sungmin9910/ColdChain-DigitalTwin-Platform/scratch/sensor_flip_guide.png

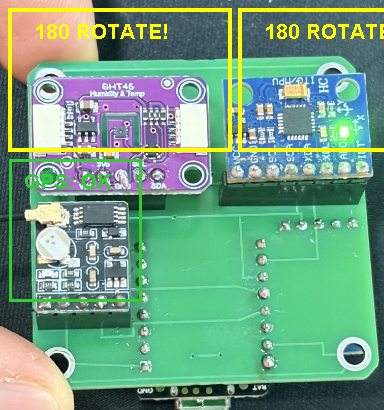
scratch/sensor_flip_guide.png
