sungmin9910/ColdChain-DigitalTwin-Platform/Final_Experiment/3_Consumer_Dashboard/consumer_guide.png

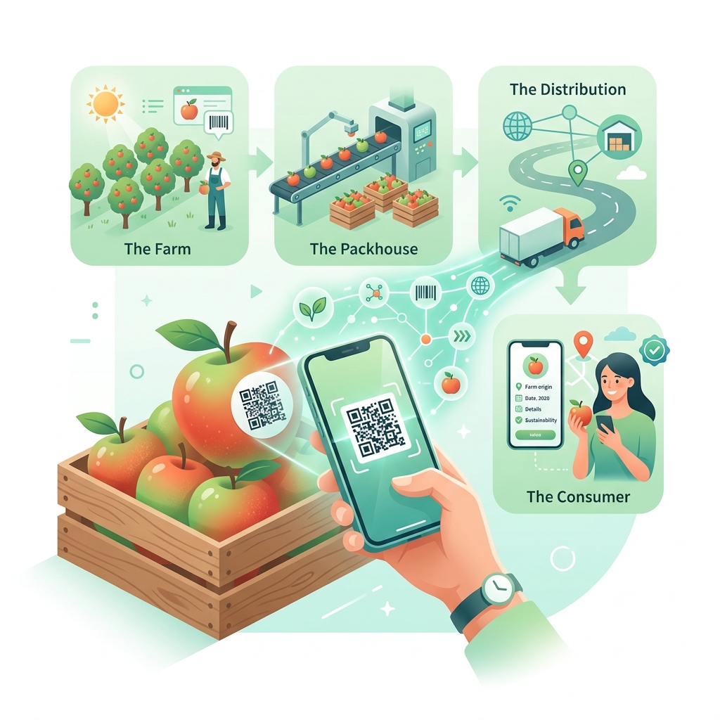
Final_Experiment/3_Consumer_Dashboard/consumer_guide.png
