sungmin9910/ColdChain-DigitalTwin-Platform/3D modeling/adafruit-sht45-breakout-board-1.snapshot.2/5665-00.jpg

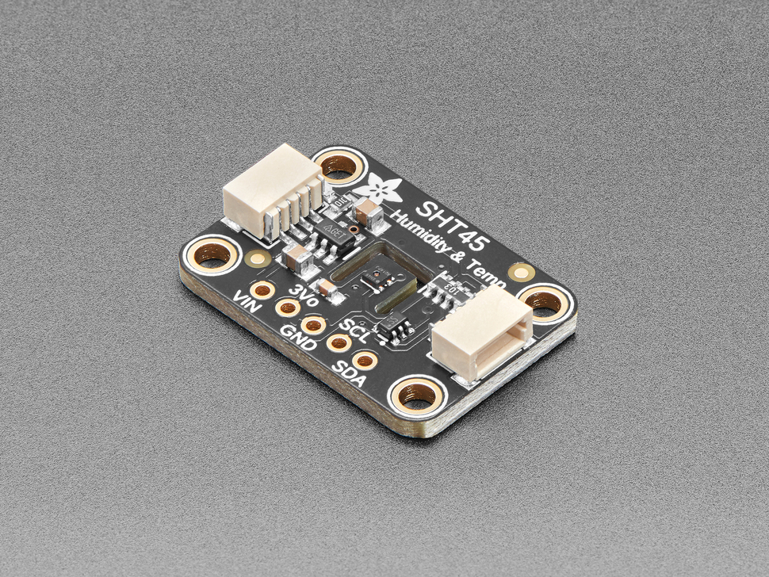
3D modeling/adafruit-sht45-breakout-board-1.snapshot.2/5665-00.jpg
