sungmin9910/ColdChain-DigitalTwin-Platform/3D modeling/CarrierBoard_BeetleC6_EdgeUSB_50x50_NoText/Fig2_CarrierBoard_3D_Isometric_Engineering_Drawing.png

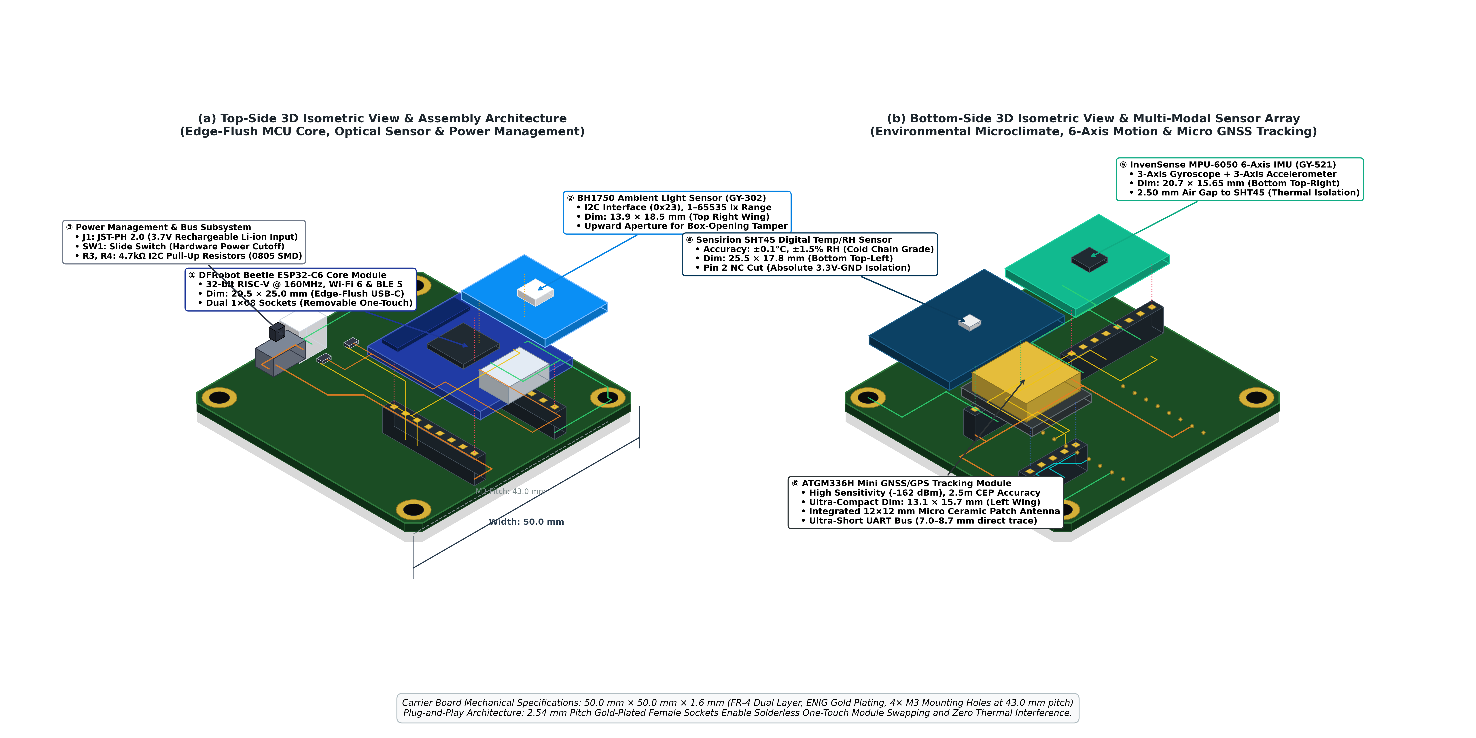
3D modeling/CarrierBoard_BeetleC6_EdgeUSB_50x50_NoText/Fig2_CarrierBoard_3D_Isometric_Engineering_Drawing.png
