sungmin9910/ColdChain-DigitalTwin-Platform/3D modeling/CarrierBoard_BeetleC6_EdgeUSB_50x50_NoText/Fig7_FDT_CrossSection_Engineering_Schematic.png

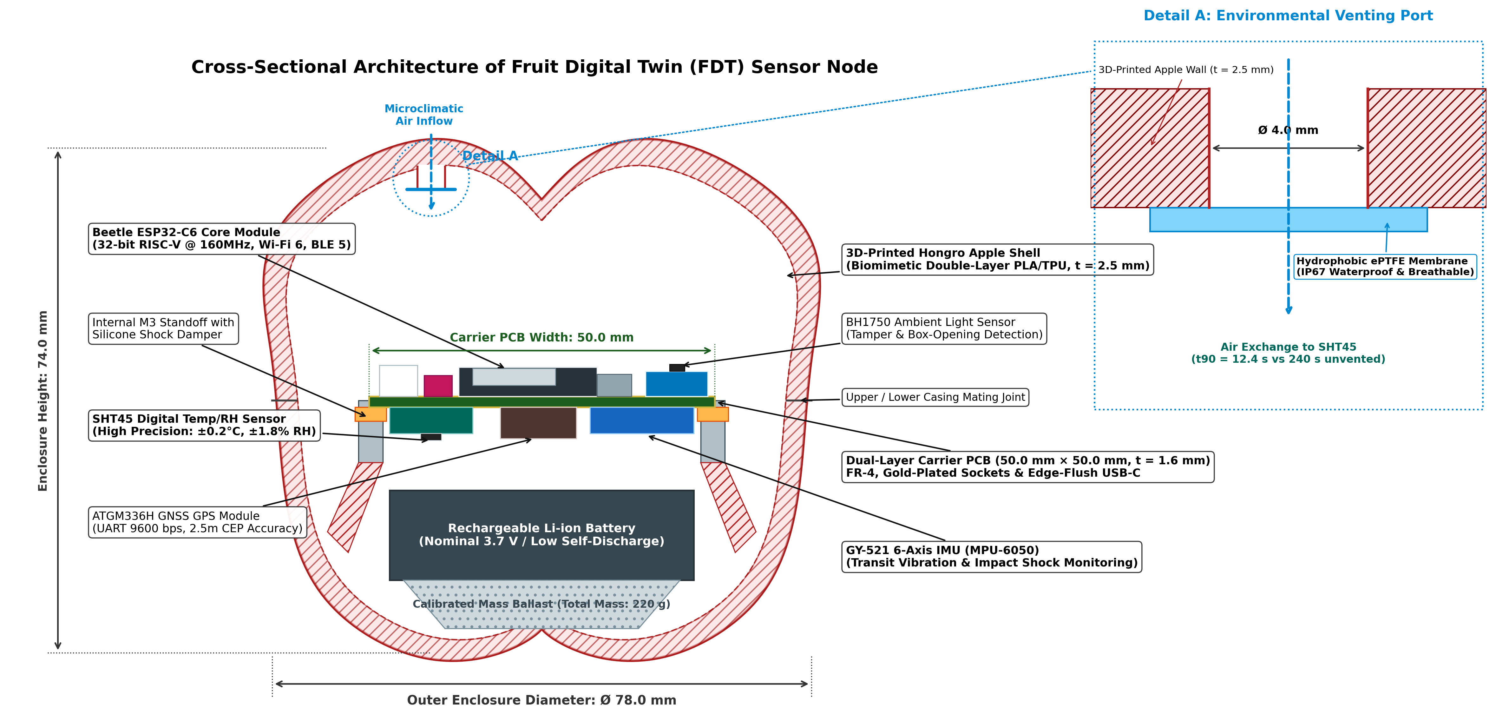
3D modeling/CarrierBoard_BeetleC6_EdgeUSB_50x50_NoText/Fig7_FDT_CrossSection_Engineering_Schematic.png
