sungmin9910/ColdChain-DigitalTwin-Platform/3D modeling/CarrierBoard_BeetleC6_EdgeUSB_50x50_NoText/Render_Bottom_NoText.png

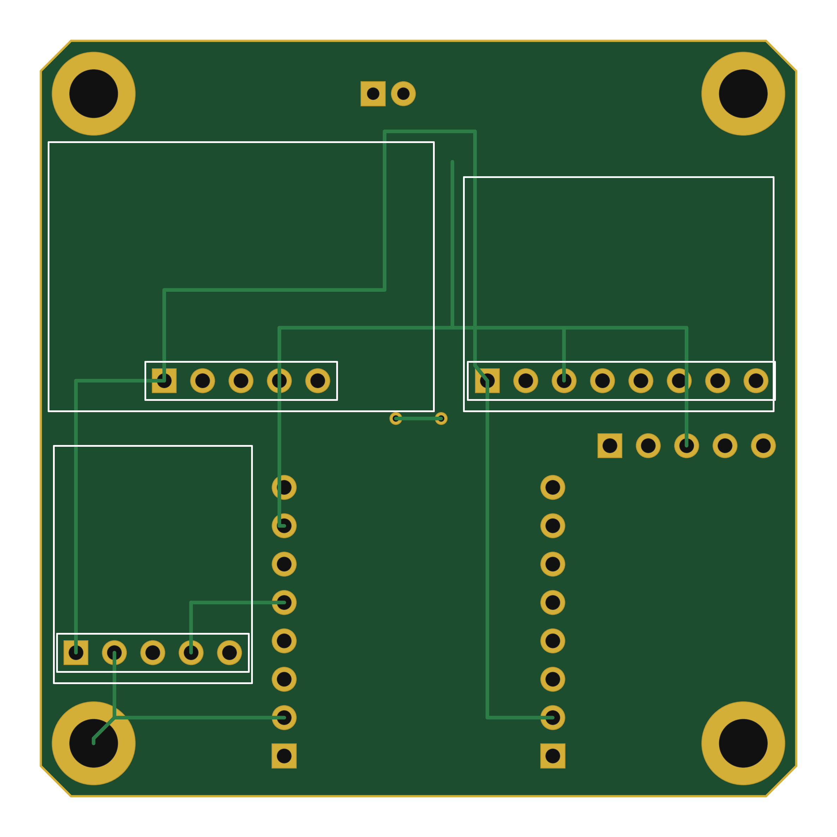
3D modeling/CarrierBoard_BeetleC6_EdgeUSB_50x50_NoText/Render_Bottom_NoText.png
