sungmin9910/ColdChain-DigitalTwin-Platform/3D modeling/CarrierBoard_BeetleC6_EdgeUSB_50x50_NoText/render_top_pcb.png

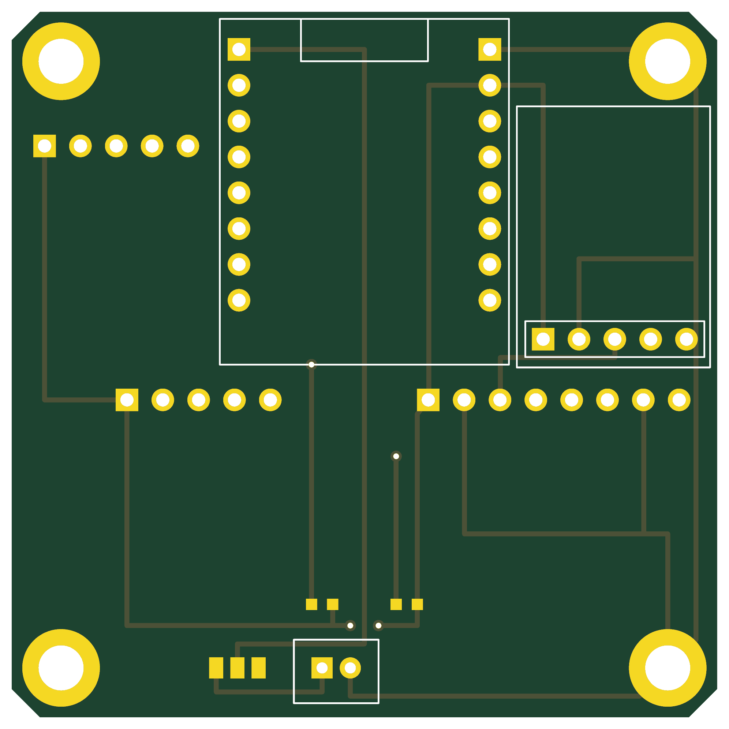
3D modeling/CarrierBoard_BeetleC6_EdgeUSB_50x50_NoText/render_top_pcb.png
