sungmin9910/ColdChain-DigitalTwin-Platform/3D modeling/GyroSensor_GY-521/Renderings/GY-521 MPU-6050_Webv004.jpg

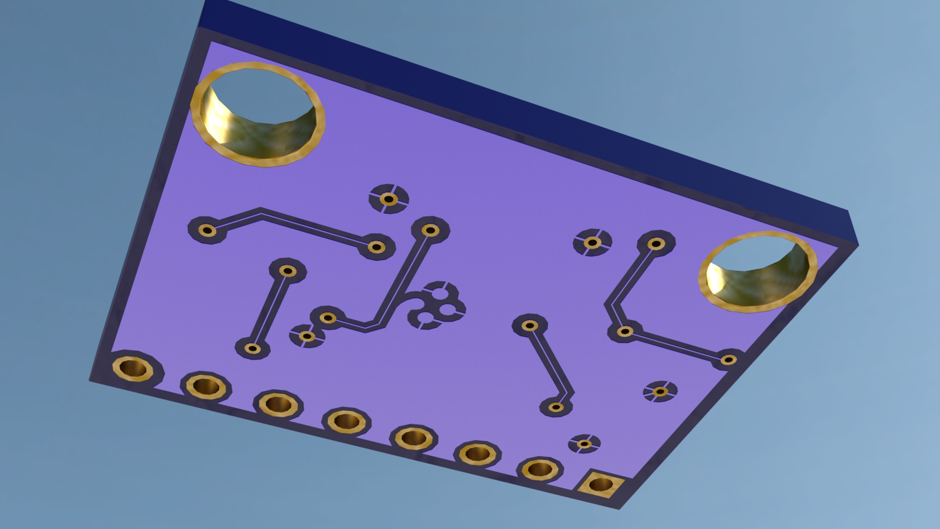
3D modeling/GyroSensor_GY-521/Renderings/GY-521 MPU-6050_Webv004.jpg
