sungmin9910/ColdChain-DigitalTwin-Platform/3D modeling/hw-373-1.snapshot.2/pic.jpg

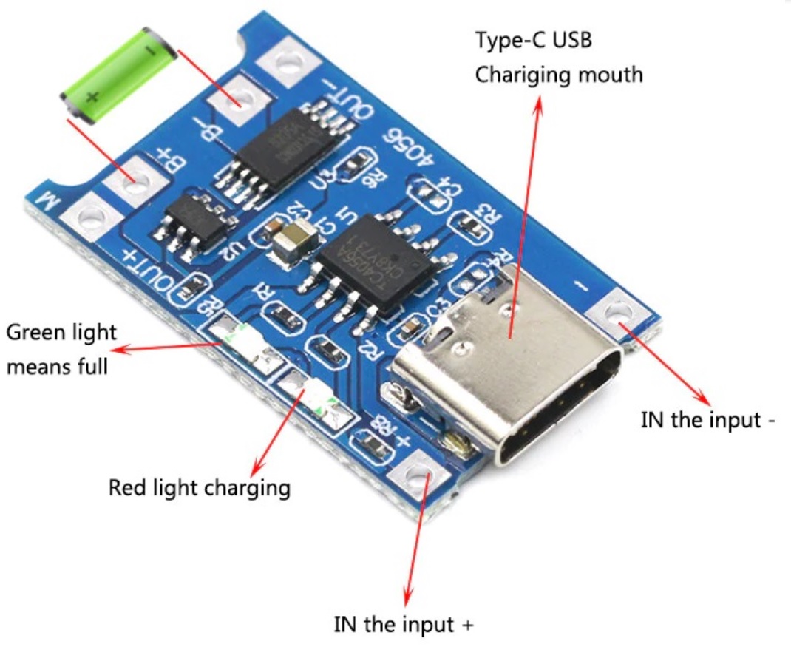
3D modeling/hw-373-1.snapshot.2/pic.jpg
