sungmin9910/ColdChain-DigitalTwin-Platform/3D modeling/mini dc dc boost module/mini dc dc boost module.png

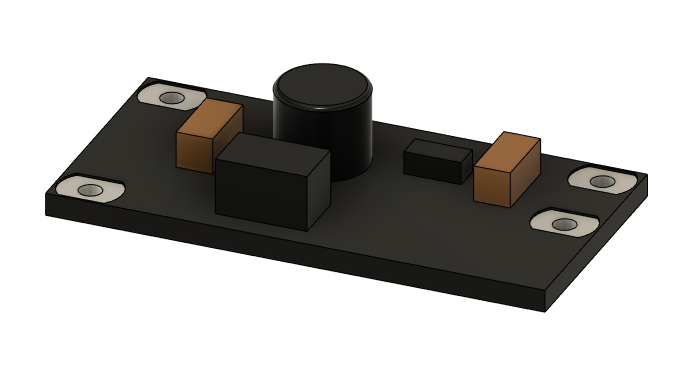
3D modeling/mini dc dc boost module/mini dc dc boost module.png
