sungmin9910/ColdChain-DigitalTwin-Platform/3D modeling/Neo-6m-0-001/Neo-6m-0-001.png

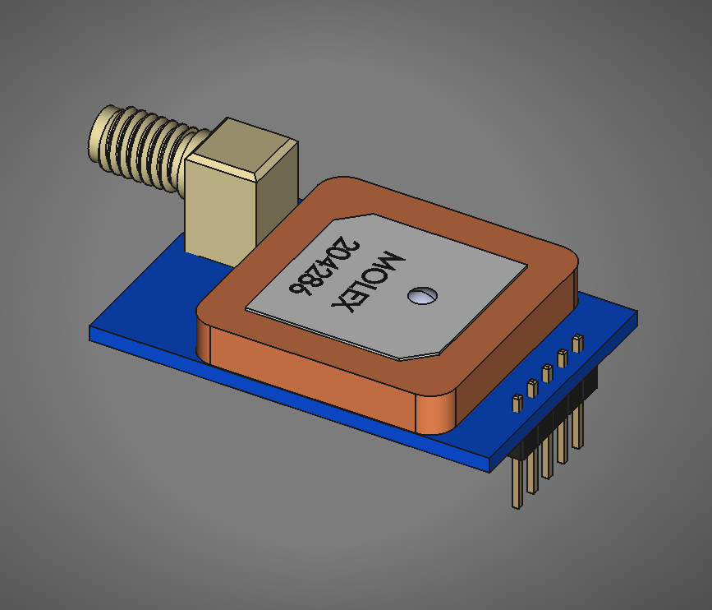
3D modeling/Neo-6m-0-001/Neo-6m-0-001.png
