sungmin9910/ColdChain-DigitalTwin-Platform/3D modeling/회로도.kicad_sch/pcb_layout.png

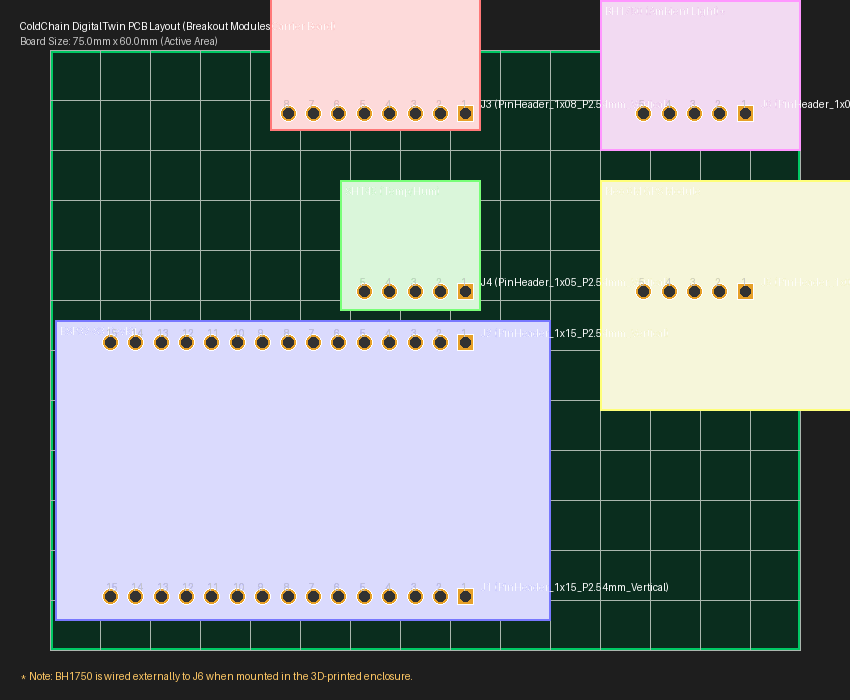
3D modeling/회로도.kicad_sch/pcb_layout.png
