sungmin9910/ColdChain-DigitalTwin-Platform/3D modeling/회로도_stack/pcb_stack_layout.png

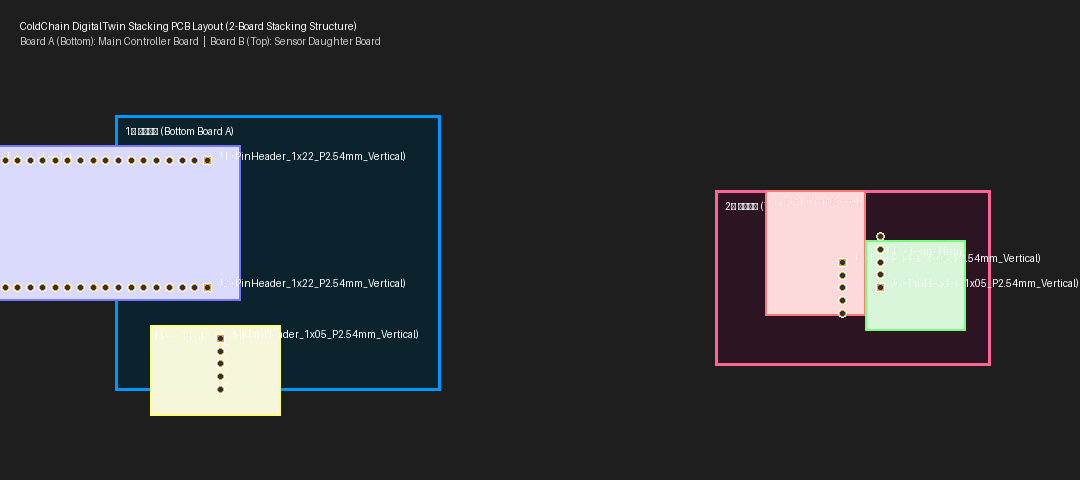
3D modeling/회로도_stack/pcb_stack_layout.png
