sungmin9910/ColdChain-DigitalTwin-Platform/KSHS/digital_twin_v2.png

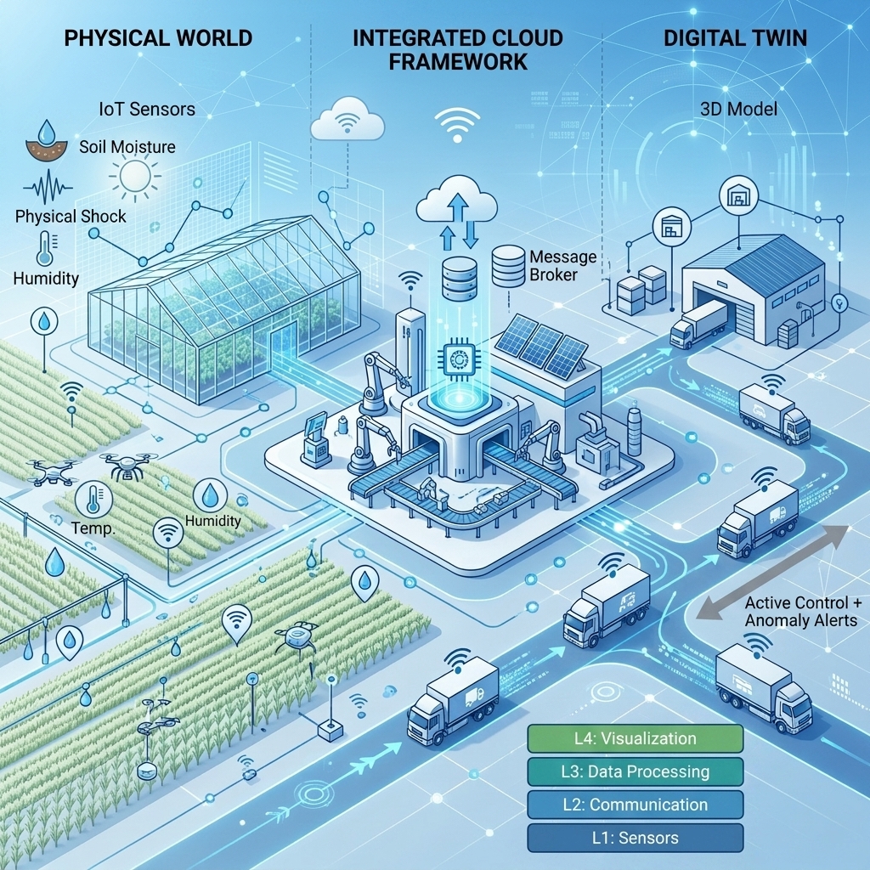
KSHS/digital_twin_v2.png
