sungmin9910/ColdChain-DigitalTwin-Platform/KSHS/extracted_images/slide_1_img_24_449x393.jpg

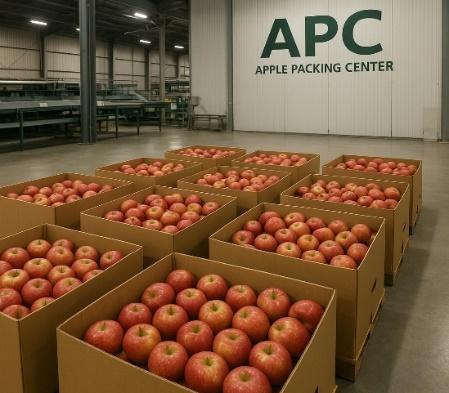
KSHS/extracted_images/slide_1_img_24_449x393.jpg
