sungmin9910/ColdChain-DigitalTwin-Platform/KSHS/extracted_images/slide_1_img_32_4032x2268.png

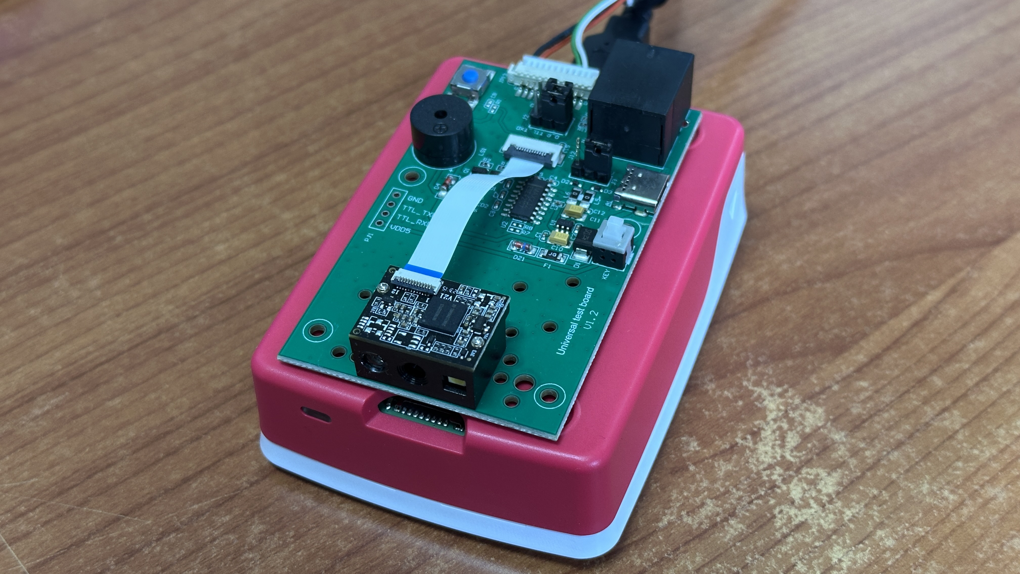
KSHS/extracted_images/slide_1_img_32_4032x2268.png
