sungmin9910/ColdChain-DigitalTwin-Platform/KSHS/extracted_images/slide_1_img_35_1330x1266.png

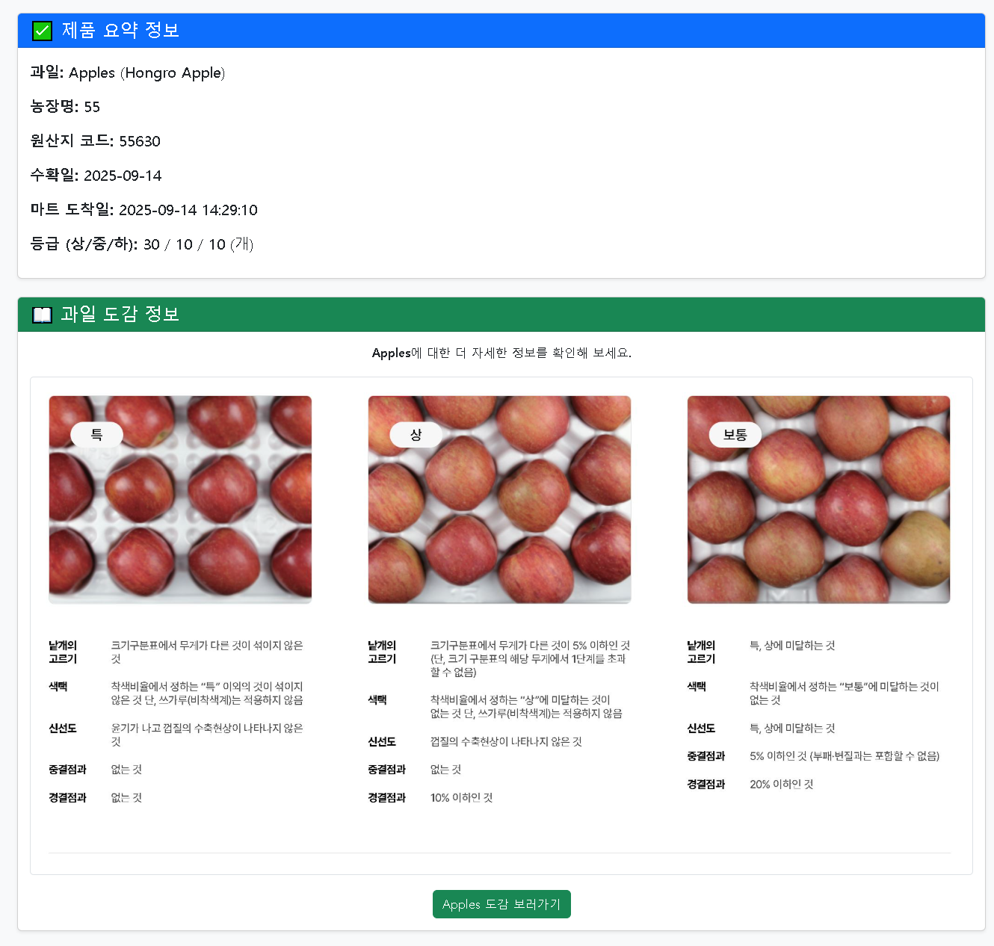
KSHS/extracted_images/slide_1_img_35_1330x1266.png
