sungmin9910/ColdChain-DigitalTwin-Platform/KSHS/extracted_images/slide_1_img_36_530x530.png

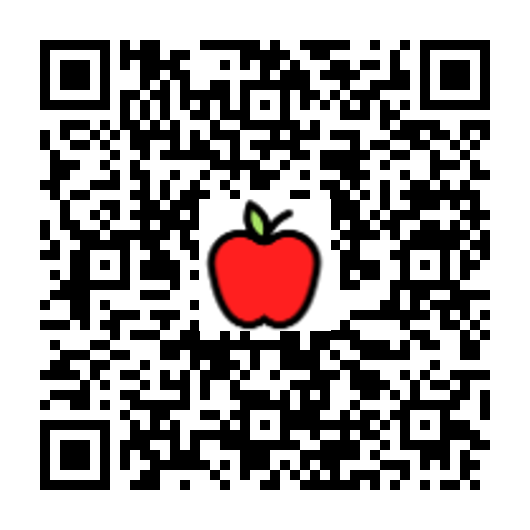
KSHS/extracted_images/slide_1_img_36_530x530.png
