sungmin9910/ColdChain-DigitalTwin-Platform/KSHS/extracted_images/slide_1_img_37_433x433.png

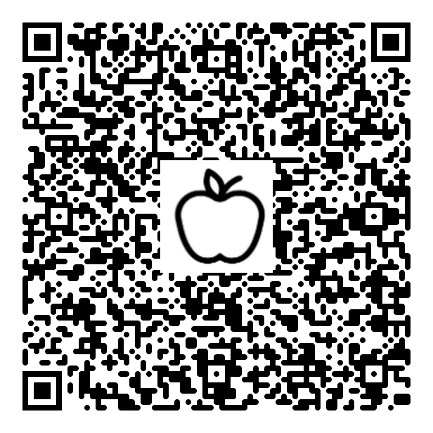
KSHS/extracted_images/slide_1_img_37_433x433.png
