sungmin9910/ColdChain-DigitalTwin-Platform/KSHS/extracted_images/slide_1_img_38_3024x3024.png

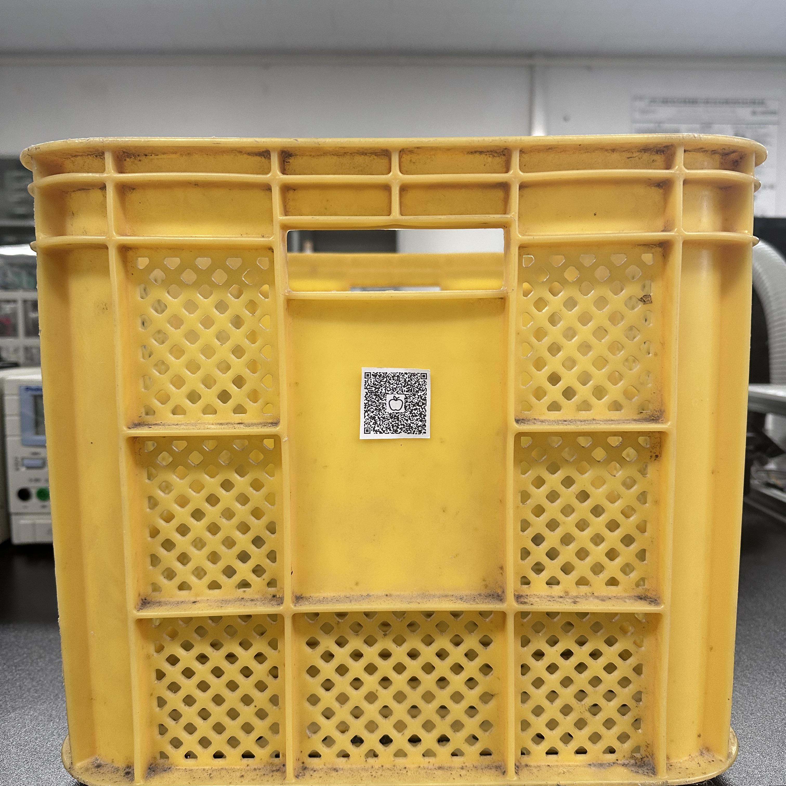
KSHS/extracted_images/slide_1_img_38_3024x3024.png
