sungmin9910/ColdChain-DigitalTwin-Platform/KSHS/extracted_images/slide_1_img_41_285x221.jpg

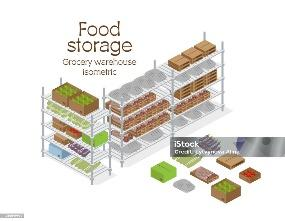
KSHS/extracted_images/slide_1_img_41_285x221.jpg
