sungmin9910/ColdChain-DigitalTwin-Platform/KSHS/extracted_images/slide_1_img_46_1651x1844.png

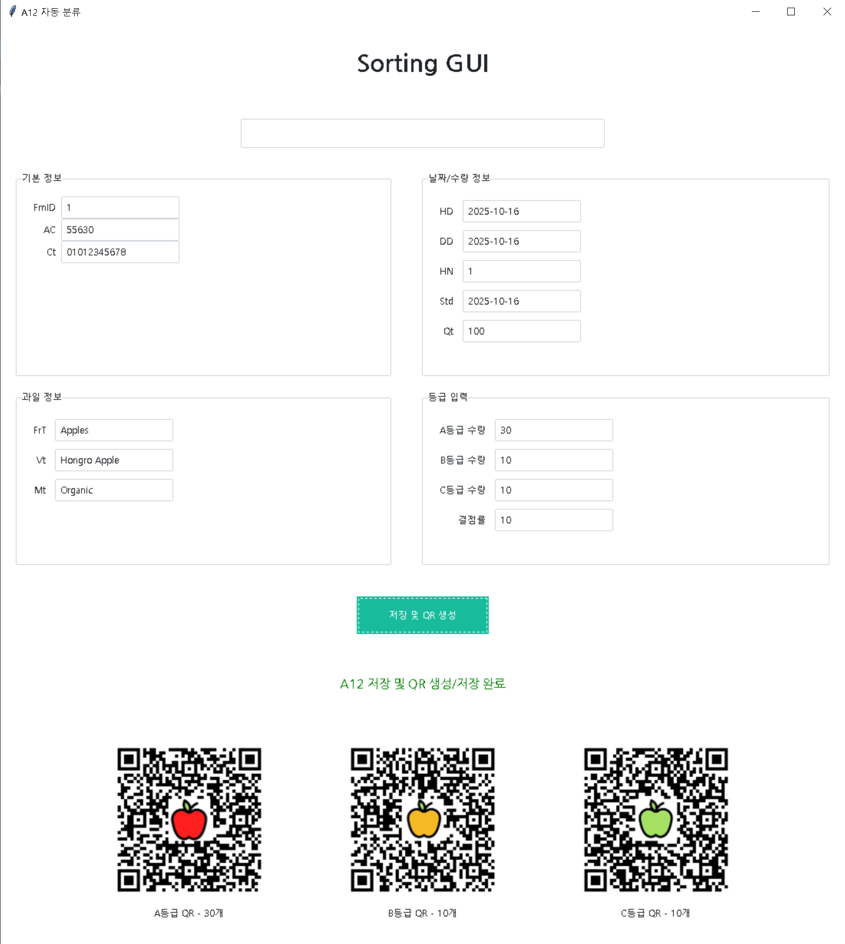
KSHS/extracted_images/slide_1_img_46_1651x1844.png
