sungmin9910/ColdChain-DigitalTwin-Platform/KSHS/extracted_images/slide_1_img_47_241x160.jpg

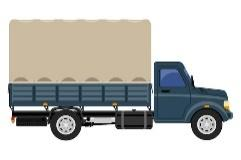
KSHS/extracted_images/slide_1_img_47_241x160.jpg
