sungmin9910/ColdChain-DigitalTwin-Platform/KSHS/extracted_images/slide_1_img_48_3216x1916.png

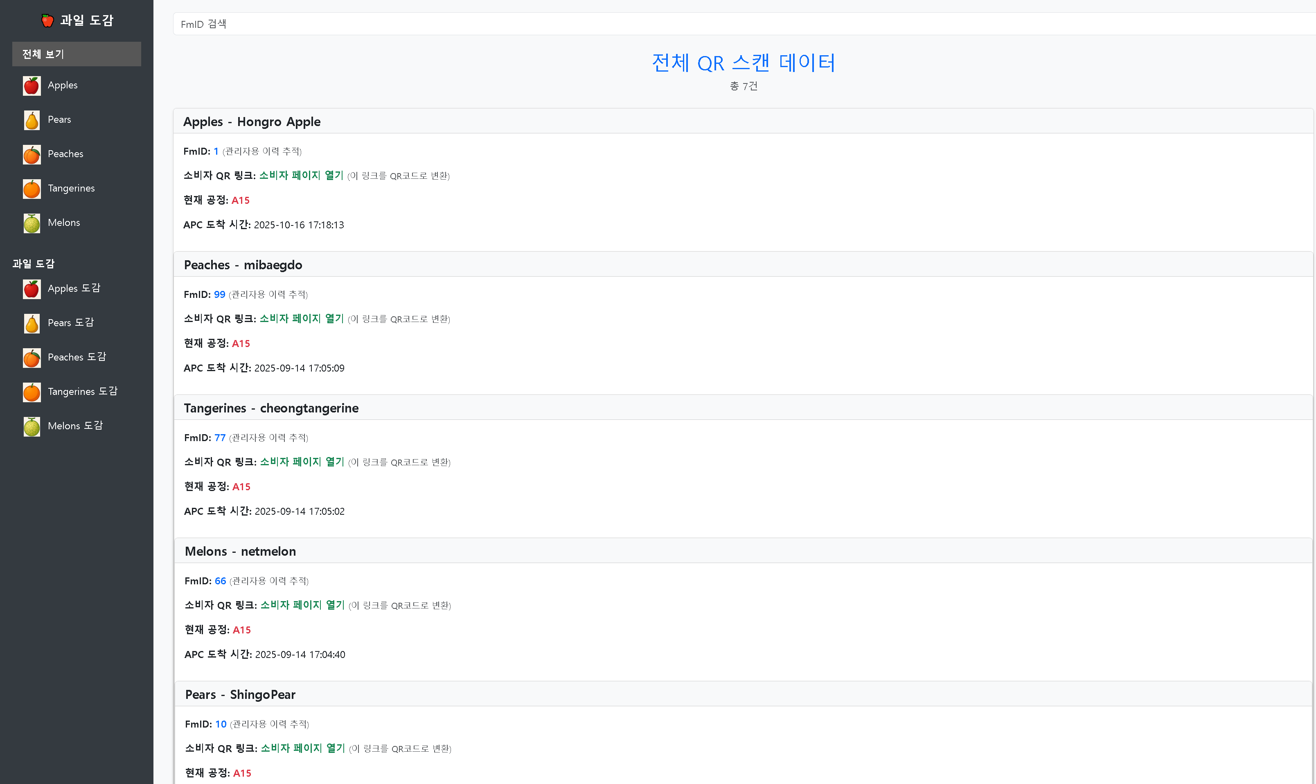
KSHS/extracted_images/slide_1_img_48_3216x1916.png
