sungmin9910/ColdChain-DigitalTwin-Platform/KSHS/extracted_images/slide_1_img_50_1024x1024.png

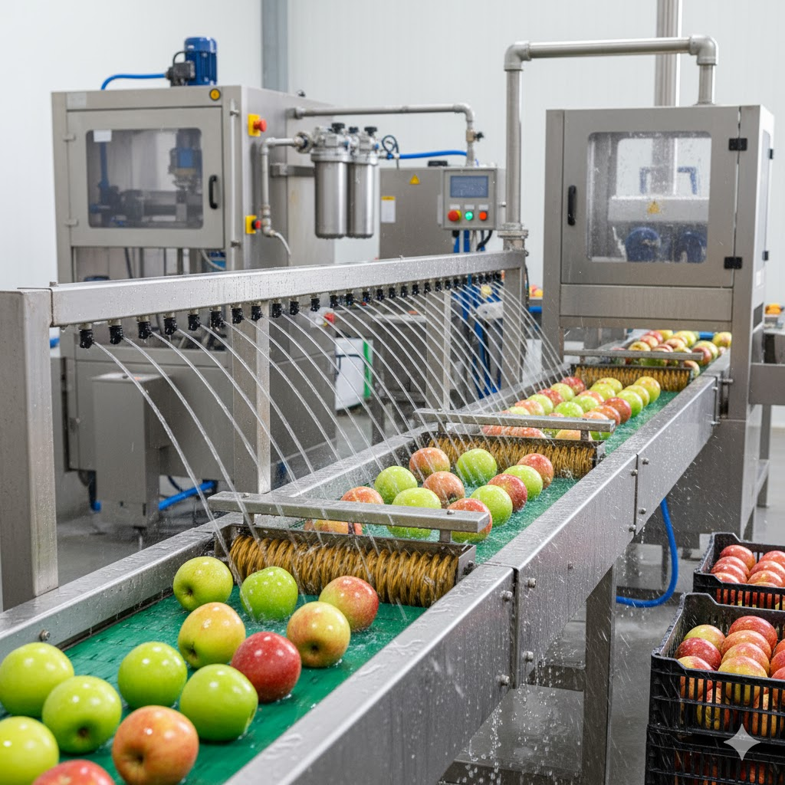
KSHS/extracted_images/slide_1_img_50_1024x1024.png
