sungmin9910/ColdChain-DigitalTwin-Platform/KSHS/extracted_images/slide_1_img_52_1024x1024.png

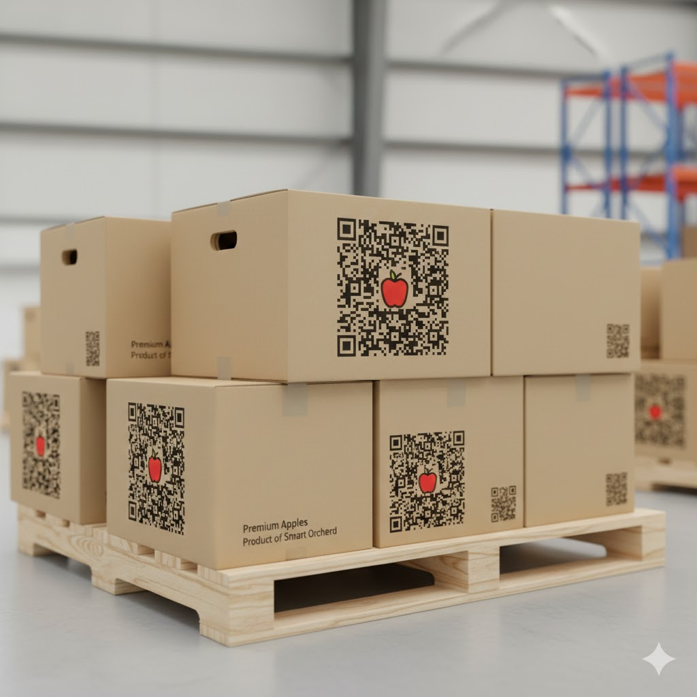
KSHS/extracted_images/slide_1_img_52_1024x1024.png
