sungmin9910/ColdChain-DigitalTwin-Platform/KSHS/extracted_images/slide_1_img_55_1232x591.png

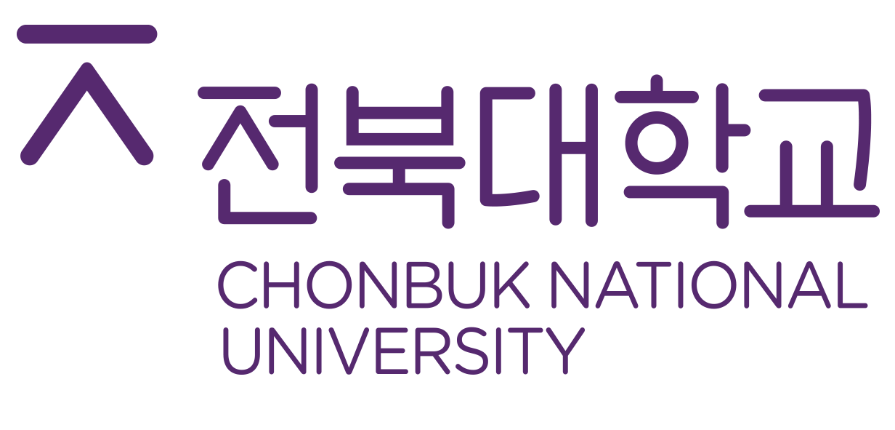
KSHS/extracted_images/slide_1_img_55_1232x591.png
