sungmin9910/ColdChain-DigitalTwin-Platform/KSHS/extracted_pdf_images/Agricultural_Digital_Twins_p2_img1_3823x2134.png

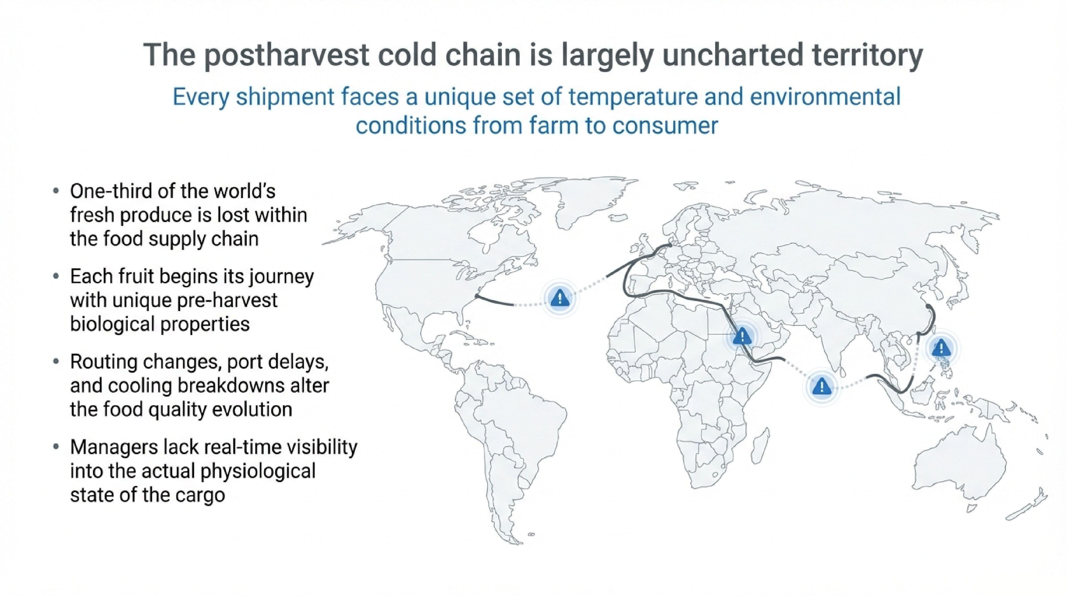
KSHS/extracted_pdf_images/Agricultural_Digital_Twins_p2_img1_3823x2134.png
