sungmin9910/ColdChain-DigitalTwin-Platform/KSHS/extracted_pdf_images/Digital_Produce_Logistics_p17_img1_3823x2134.png

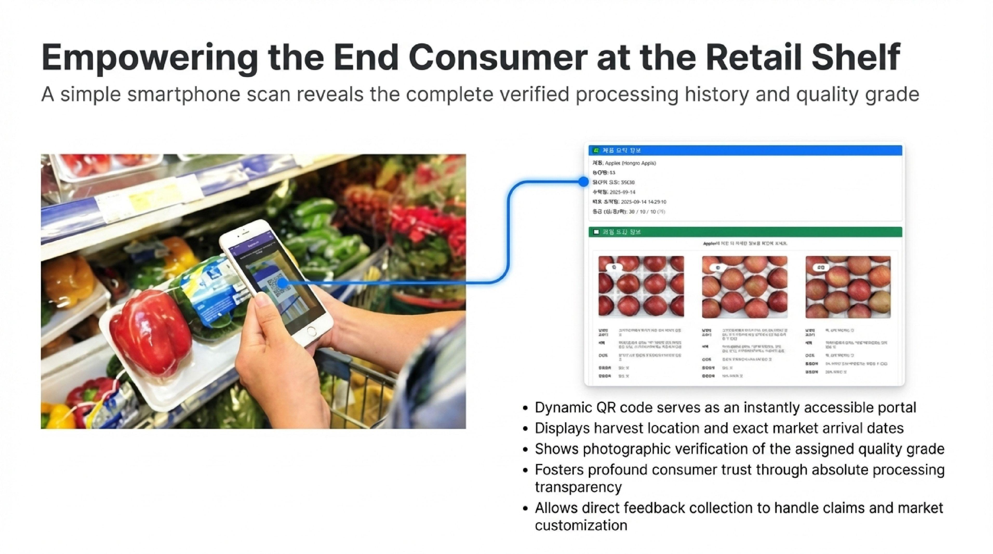
KSHS/extracted_pdf_images/Digital_Produce_Logistics_p17_img1_3823x2134.png
