sungmin9910/ColdChain-DigitalTwin-Platform/KSHS/extracted_pdf_images/디지털트윈 기반 APC농산물 유통 저장 통합 품질관리시스템 개발_p5_img1_2294x1281.png

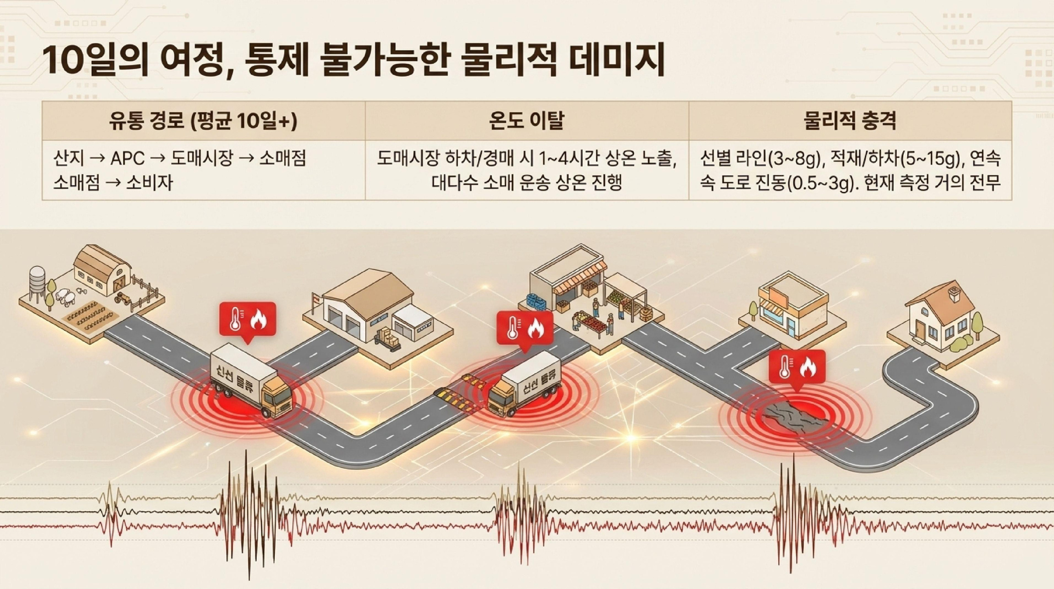
KSHS/extracted_pdf_images/디지털트윈 기반 APC농산물 유통 저장 통합 품질관리시스템 개발_p5_img1_2294x1281.png
