sungmin9910/ColdChain-DigitalTwin-Platform/KSHS/four_layer_digital_twin.png

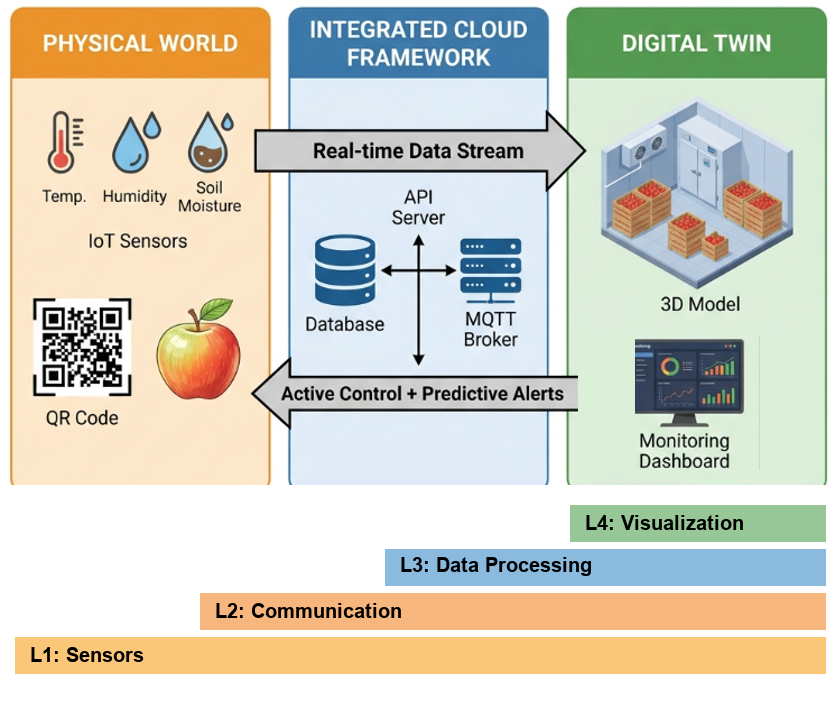
KSHS/four_layer_digital_twin.png
