sungmin9910/ColdChain-DigitalTwin-Platform/scratch/beetle_crop.png

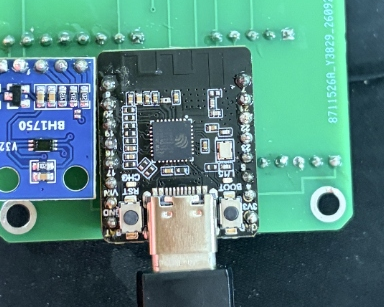
scratch/beetle_crop.png
