sungmin9910/ColdChain-DigitalTwin-Platform/scratch/bh1750_crop.png

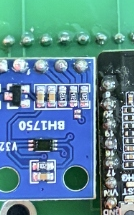
scratch/bh1750_crop.png
