sungmin9910/ColdChain-DigitalTwin-Platform/scratch/crop_bh1750.jpg

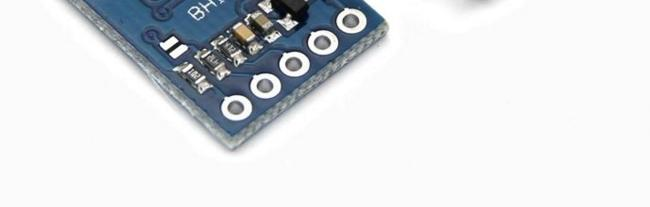
scratch/crop_bh1750.jpg
