sungmin9910/ColdChain-DigitalTwin-Platform/scratch/crop_gps.png

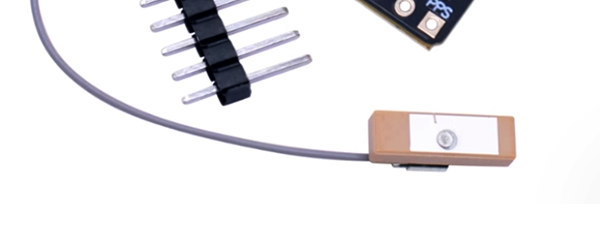
scratch/crop_gps.png
