sungmin9910/ColdChain-DigitalTwin-Platform/scratch/crop_gy521_bot.jpg

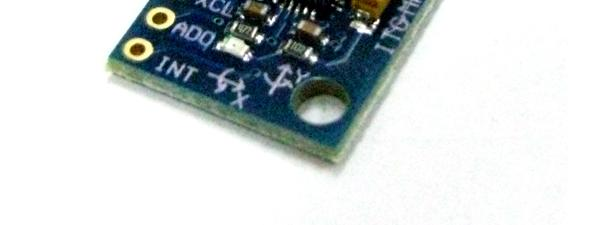
scratch/crop_gy521_bot.jpg
