sungmin9910/ColdChain-DigitalTwin-Platform/scratch/crop_gy521_top.jpg

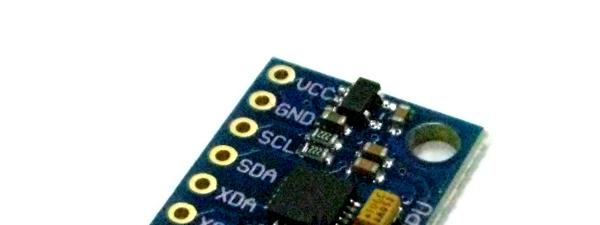
scratch/crop_gy521_top.jpg
