sungmin9910/ColdChain-DigitalTwin-Platform/scratch/crop_sht45.png

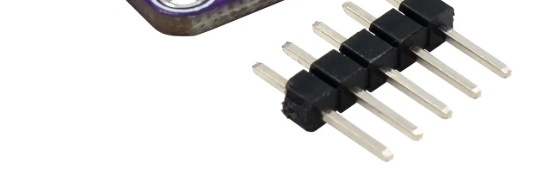
scratch/crop_sht45.png
