sungmin9910/ColdChain-DigitalTwin-Platform/scratch/DFR1117_dimension.png

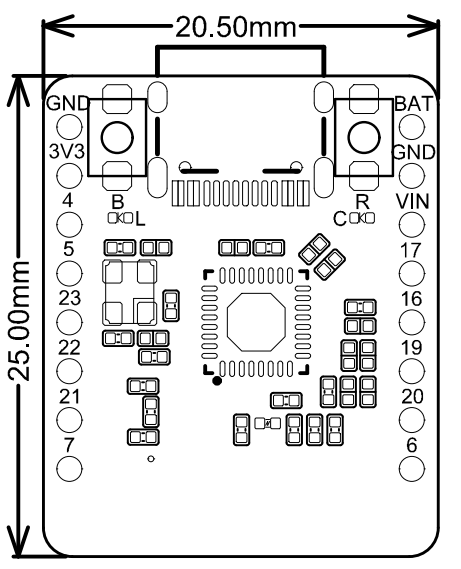
scratch/DFR1117_dimension.png
