sungmin9910/ColdChain-DigitalTwin-Platform/scratch/images/BH1750_2.jpg

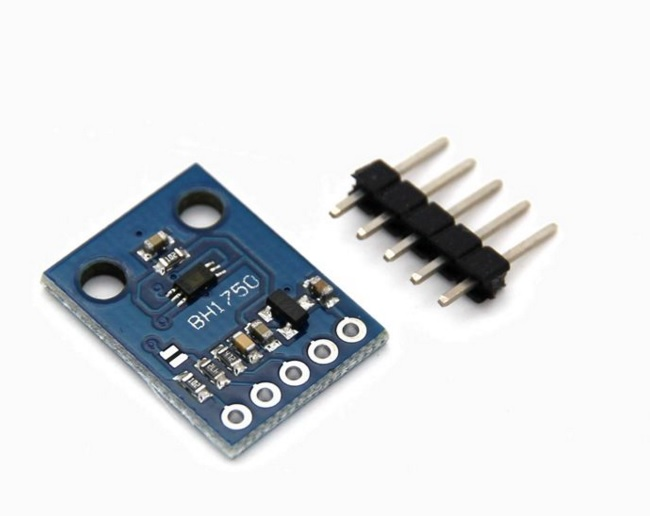
scratch/images/BH1750_2.jpg
