sungmin9910/ColdChain-DigitalTwin-Platform/scratch/images/BH1750_3.jpg

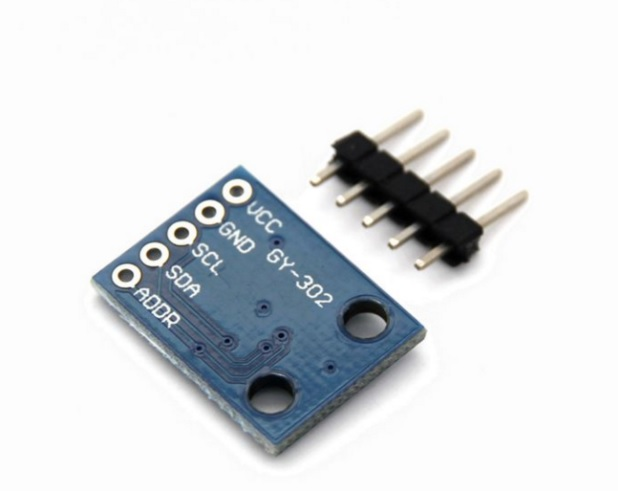
scratch/images/BH1750_3.jpg
