sungmin9910/ColdChain-DigitalTwin-Platform/scratch/images/GPS_ATGM336H_0.png

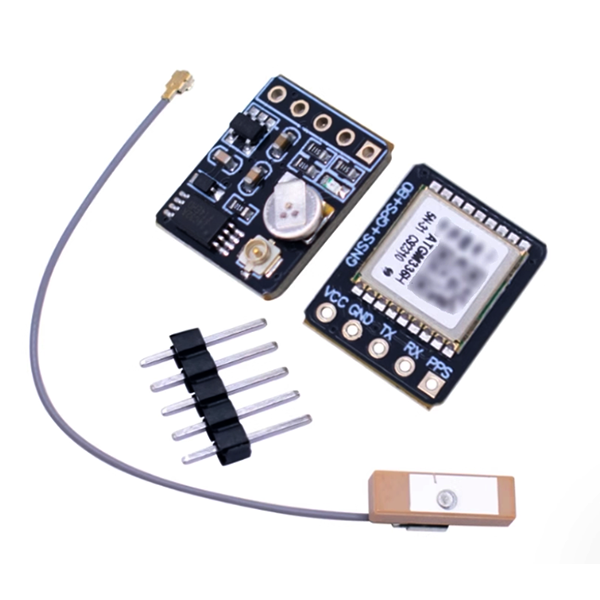
scratch/images/GPS_ATGM336H_0.png
