sungmin9910/ColdChain-DigitalTwin-Platform/scratch/images/GY-521_4.jpg

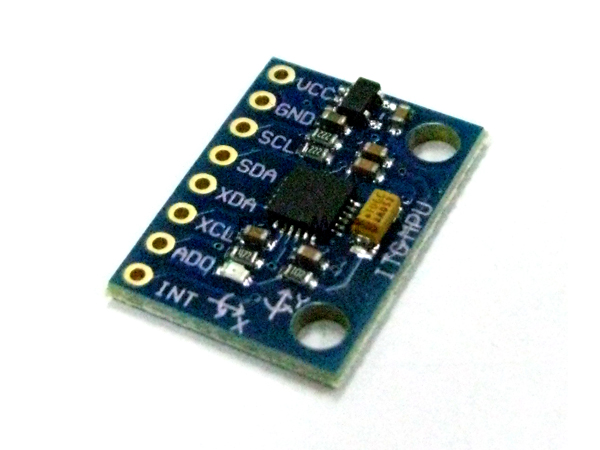
scratch/images/GY-521_4.jpg
