sungmin9910/ColdChain-DigitalTwin-Platform/scratch/images/GY-521_5.jpg

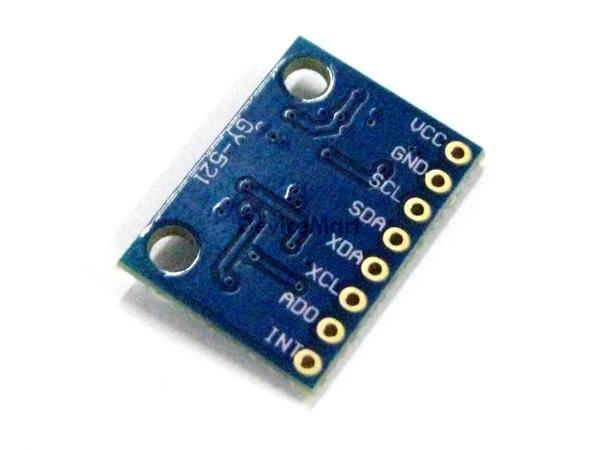
scratch/images/GY-521_5.jpg
