sungmin9910/ColdChain-DigitalTwin-Platform/scratch/images/GY-521_6.JPG

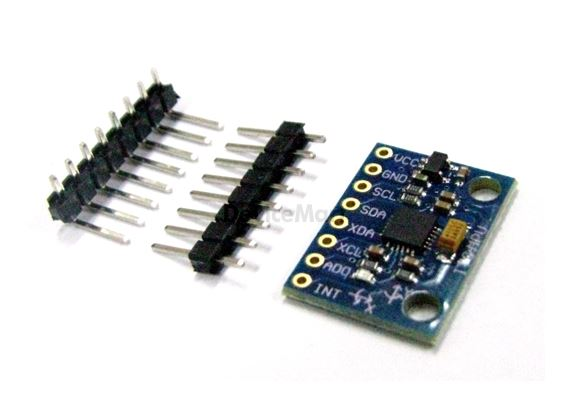
scratch/images/GY-521_6.JPG
