sungmin9910/ColdChain-DigitalTwin-Platform/scratch/images/SHT45_0.png

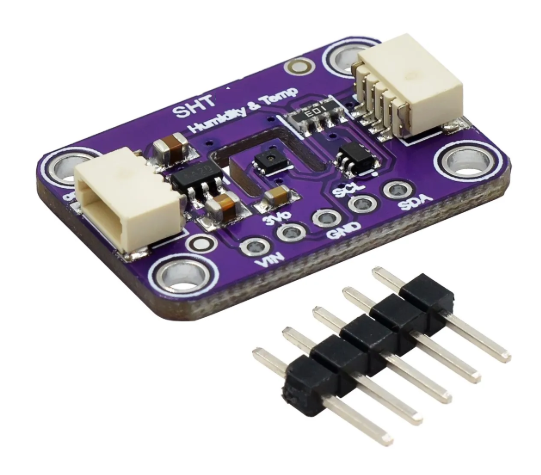
scratch/images/SHT45_0.png
