sungmin9910/ColdChain-DigitalTwin-Platform/scratch/pcb_photo_comparison.png

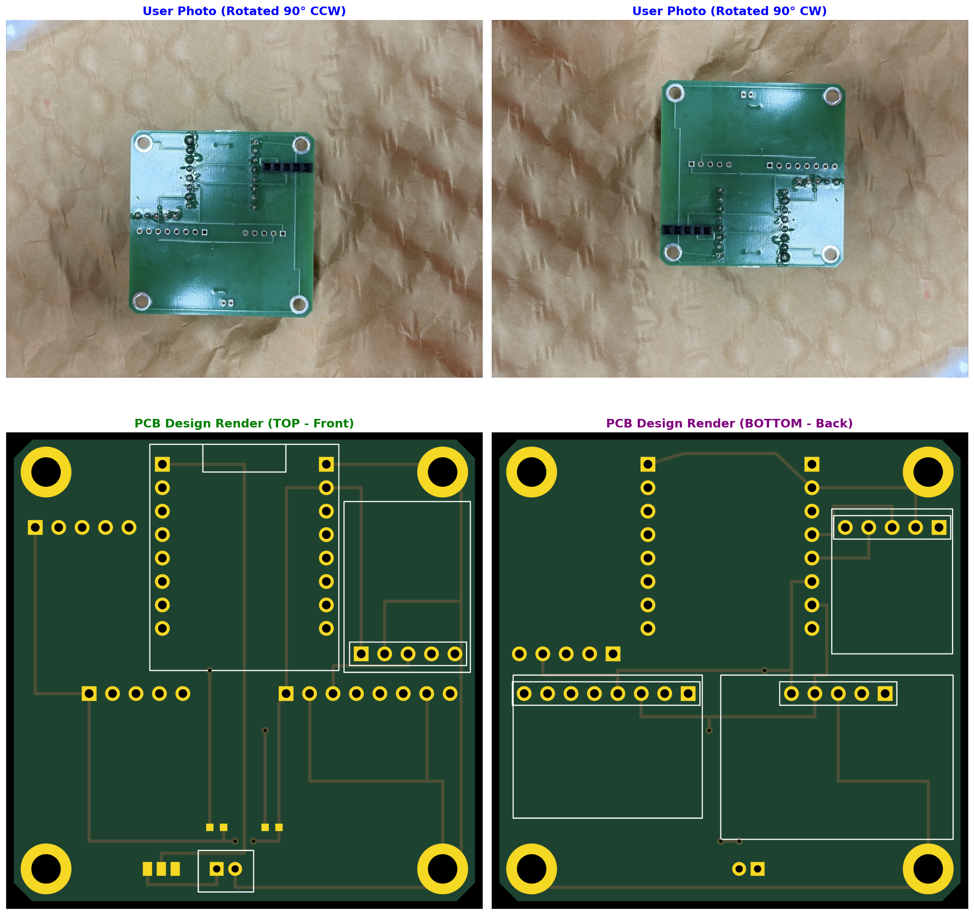
scratch/pcb_photo_comparison.png
