sungmin9910/ColdChain-DigitalTwin-Platform/scratch/photo_rot_180.jpg

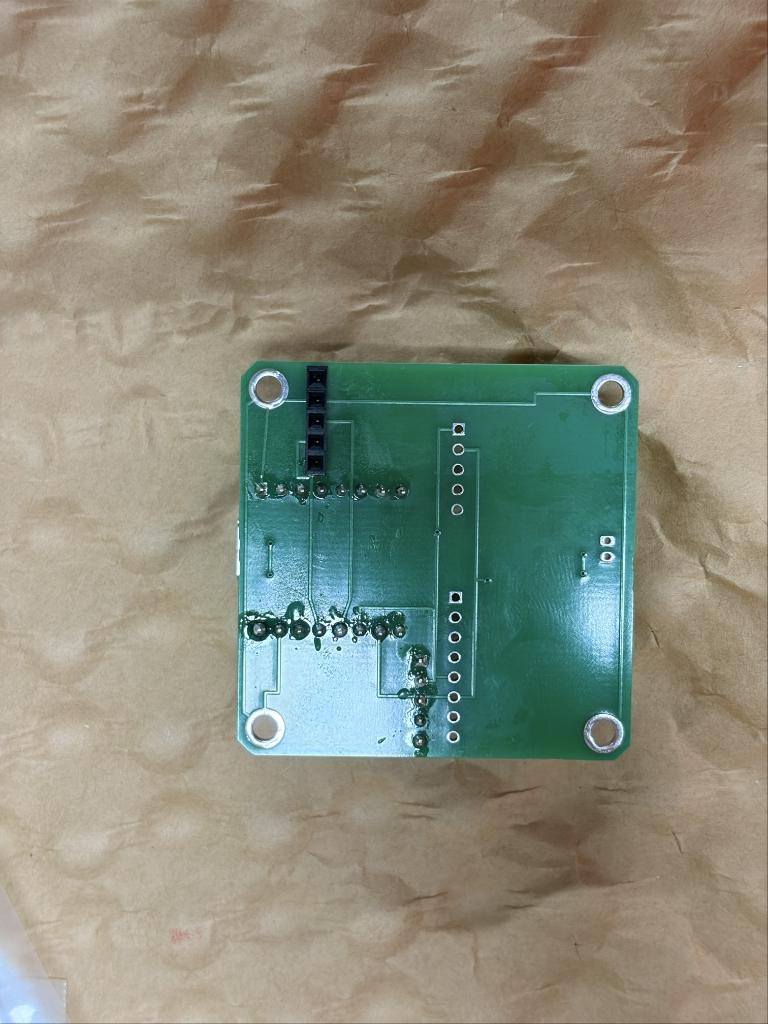
scratch/photo_rot_180.jpg
