sungmin9910/ColdChain-DigitalTwin-Platform/scratch/photo_rot_ccw.jpg

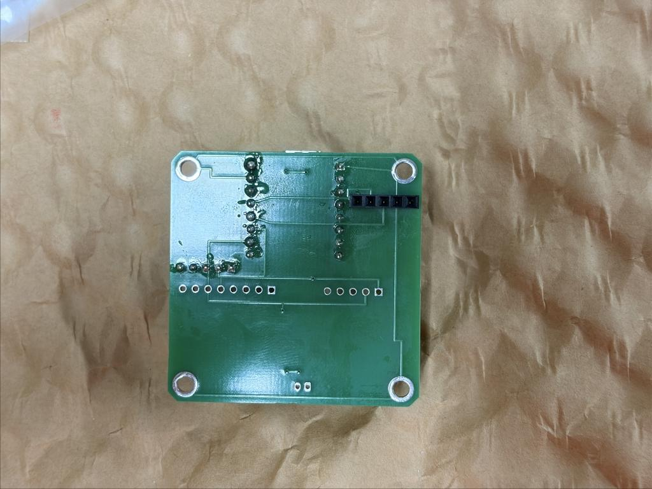
scratch/photo_rot_ccw.jpg
