sungmin9910/ColdChain-DigitalTwin-Platform/scratch/photo_rot_cw.jpg

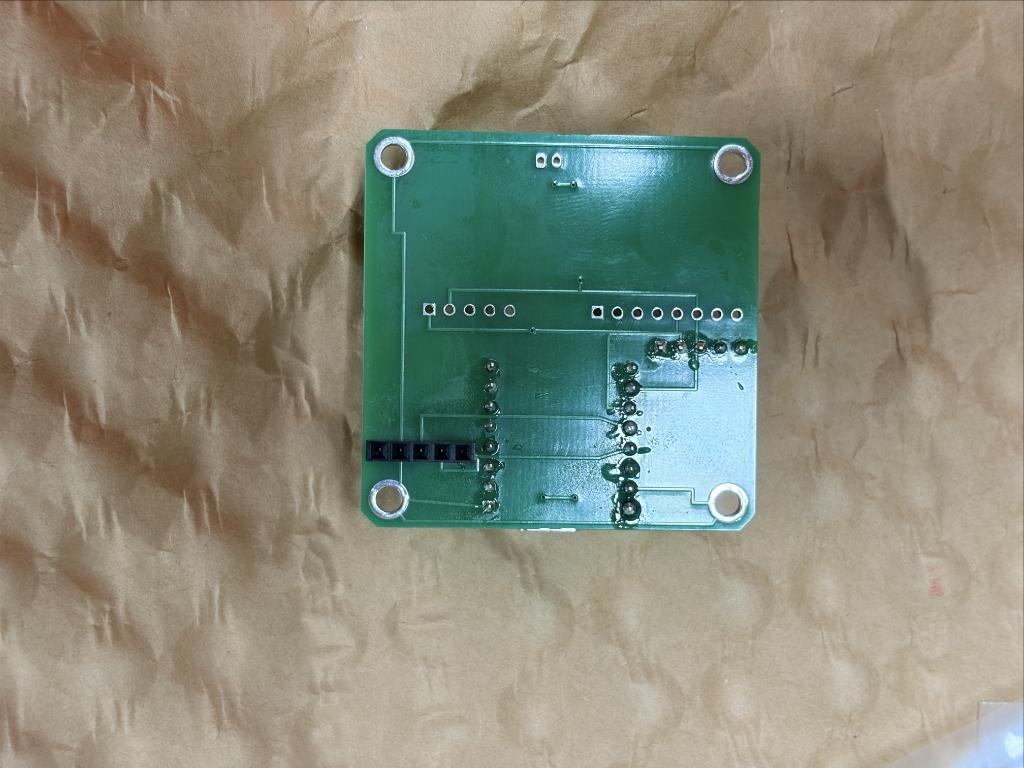
scratch/photo_rot_cw.jpg
