sungmin9910/ColdChain-DigitalTwin-Platform/scratch/preview_aesthetic_master.png

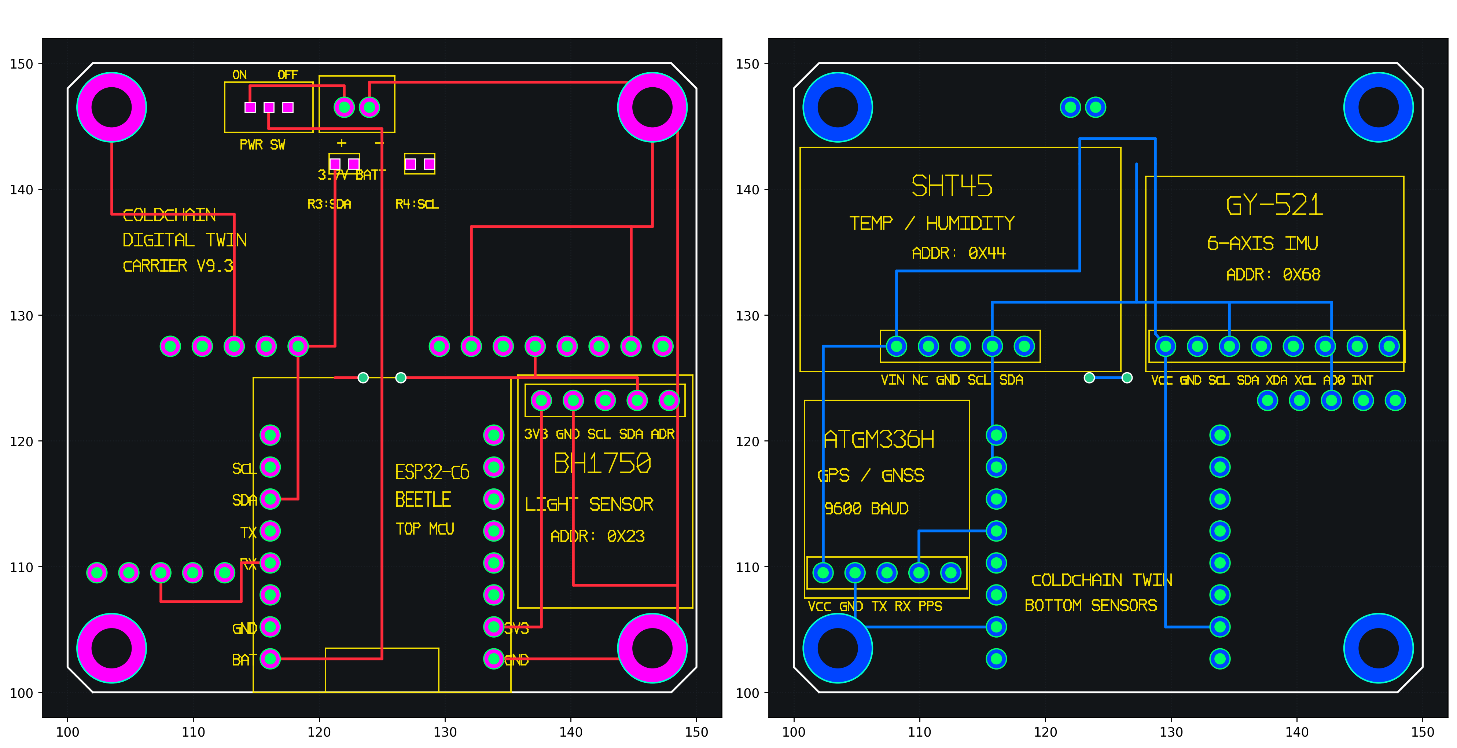
scratch/preview_aesthetic_master.png
