sungmin9910/ColdChain-DigitalTwin-Platform/scratch/preview_clean_layout.png

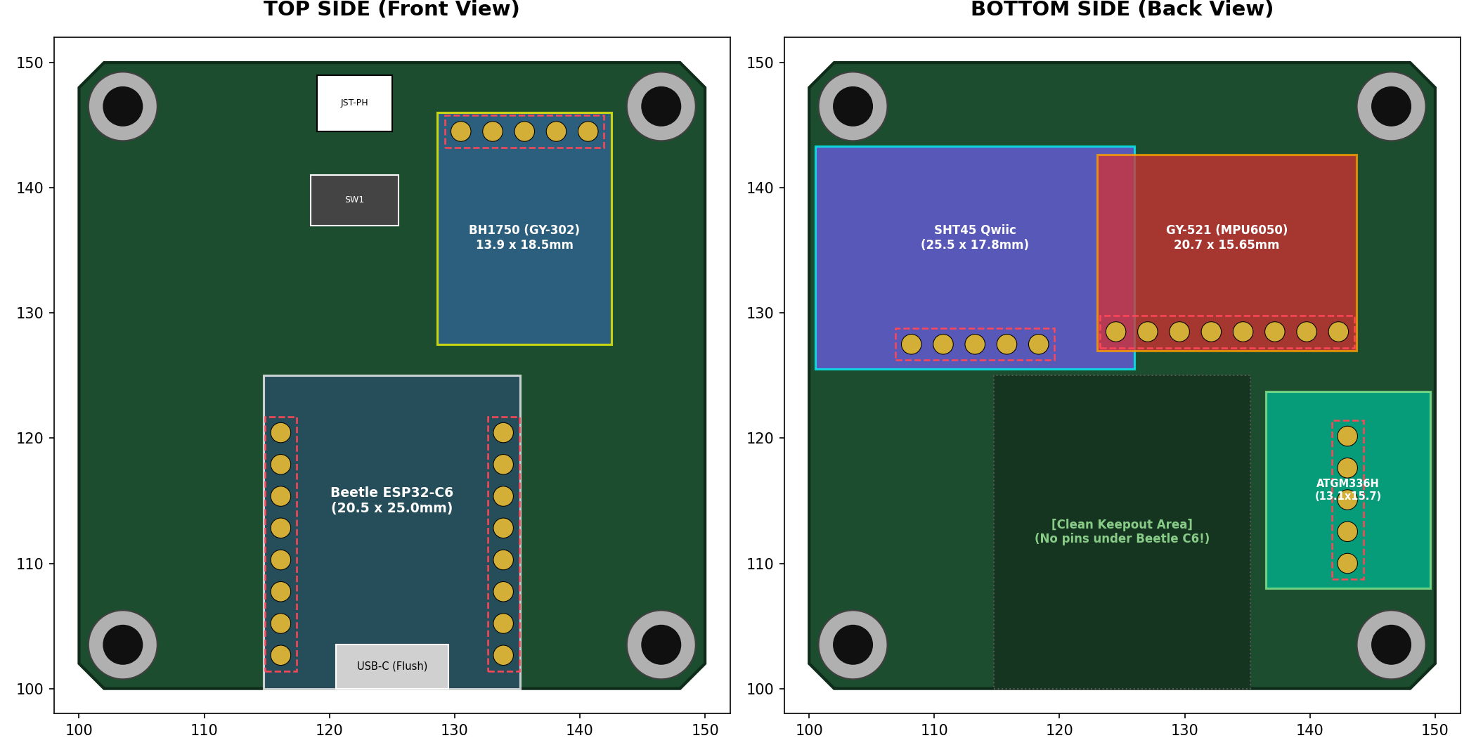
scratch/preview_clean_layout.png
