sungmin9910/ColdChain-DigitalTwin-Platform/scratch/preview_perfect_router.png

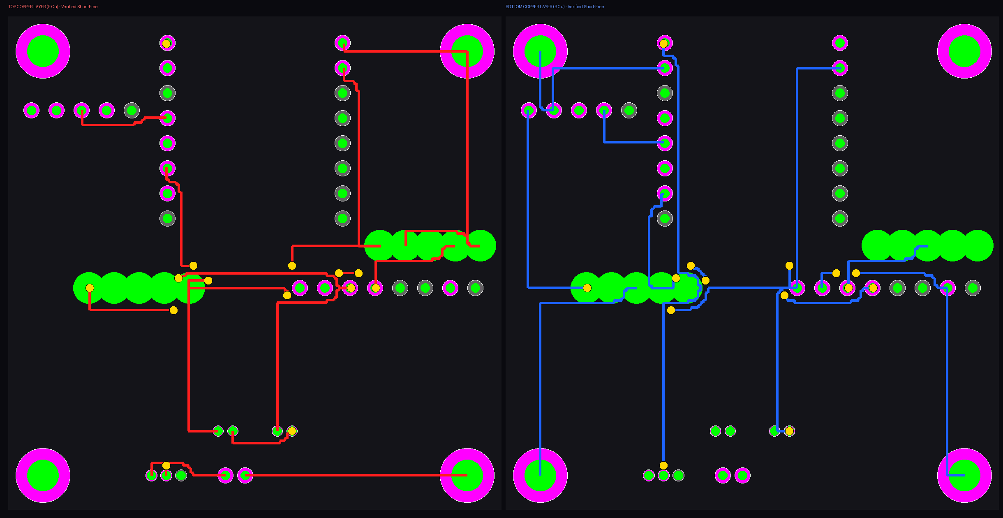
scratch/preview_perfect_router.png
