sungmin9910/ColdChain-DigitalTwin-Platform/scratch/preview_routed_layers.png

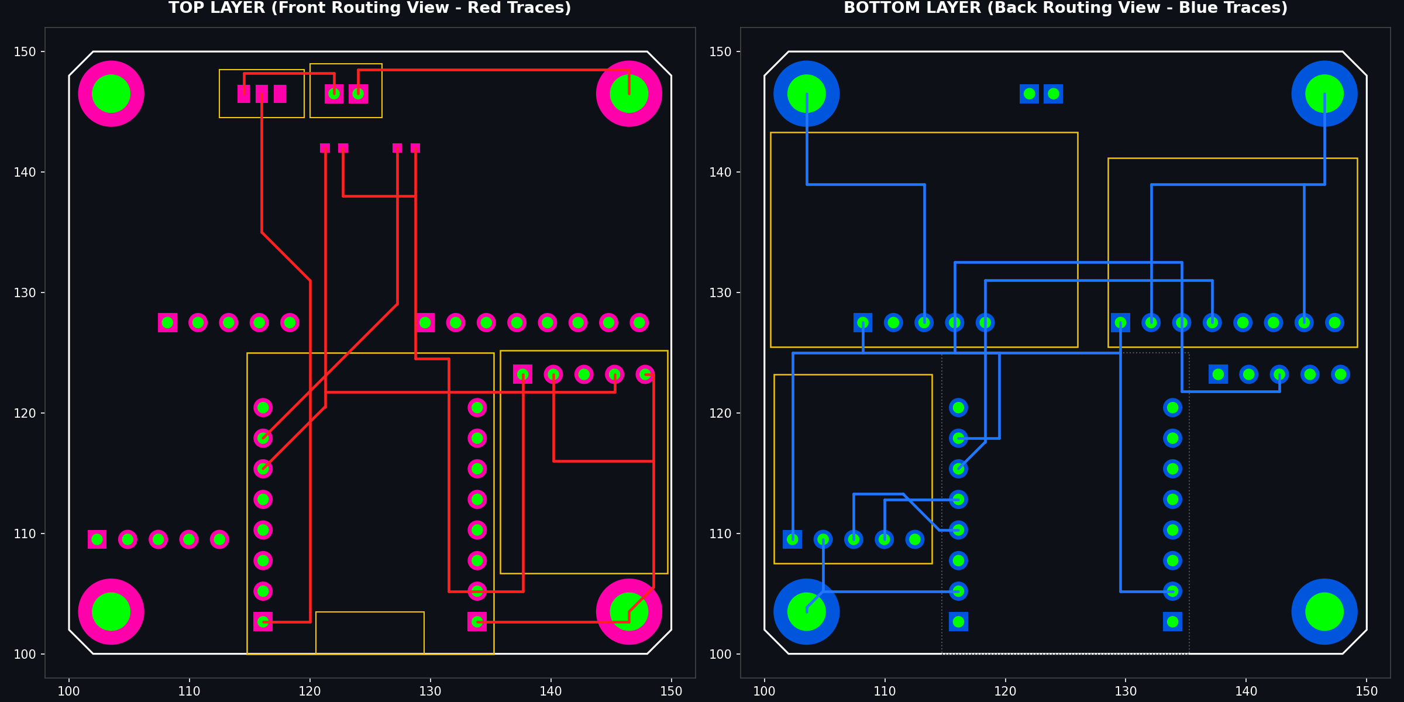
scratch/preview_routed_layers.png
