sungmin9910/ColdChain-DigitalTwin-Platform/scratch/preview_zero_overlap_v8.png

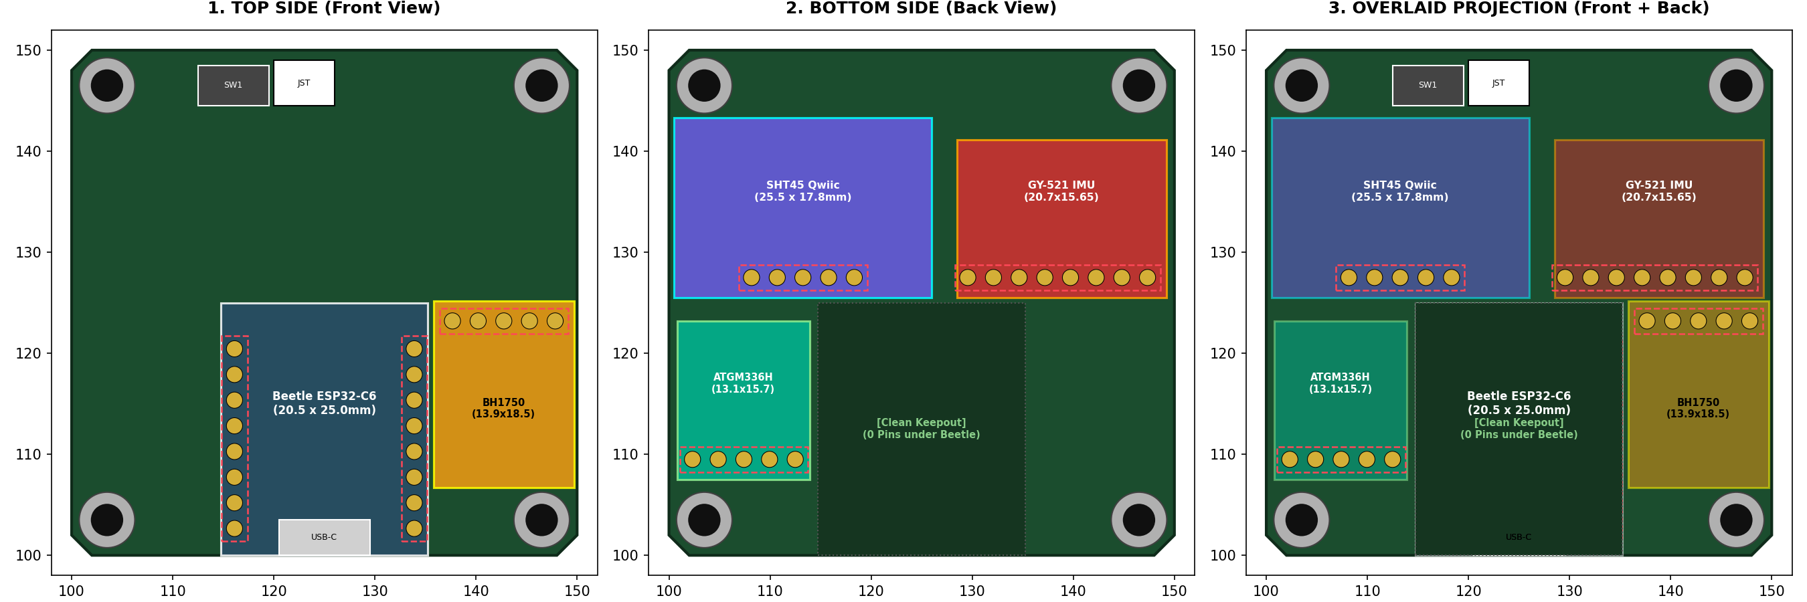
scratch/preview_zero_overlap_v8.png
