sungmin9910/ColdChain-DigitalTwin-Platform/3D_Printer_Housing/v14_QR_Scanner_Housing_Final/14_housing_right.stl

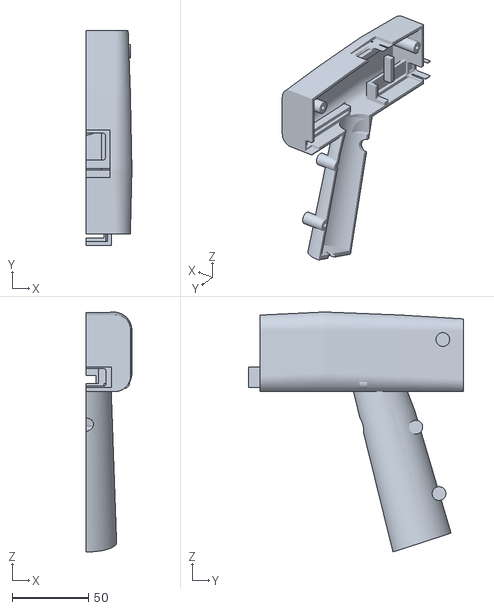
[picture p144: CAD file, 2026-06-22]
3D_Printer_Housing/v14_QR_Scanner_Housing_Final/14_housing_right.stl
30.0 x 140.6 x 157.0
