sungmin9910/ColdChain-DigitalTwin-Platform/3D_Printer_Housing/v17_QR_Scanner_Housing/17_qr_scanner_housing_right_half.stl

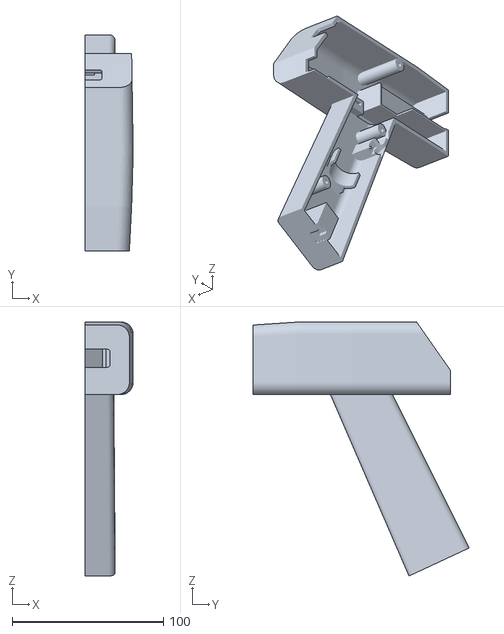
[picture p145: CAD file, 2026-07-07]
3D_Printer_Housing/v17_QR_Scanner_Housing/17_qr_scanner_housing_right_half.stl
32.0 x 143.3 x 168.1
