sungmin9910/ColdChain-DigitalTwin-Platform/3D_Printer_Housing/v18_Apple_Sensor_Pod/18_apple_stem.stl

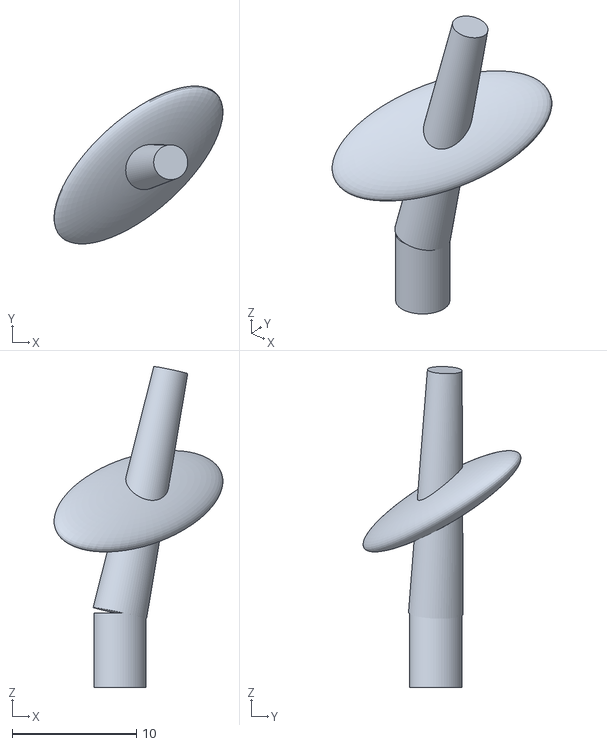
[picture p146: CAD file, 2026-09-14]
3D_Printer_Housing/v18_Apple_Sensor_Pod/18_apple_stem.stl
13.6 x 12.7 x 25.9
