sungmin9910/ColdChain-DigitalTwin-Platform/3D_Printer_Housing/v19_Apple_Sensor_Pod_5000mAh/19_apple_stem.stl

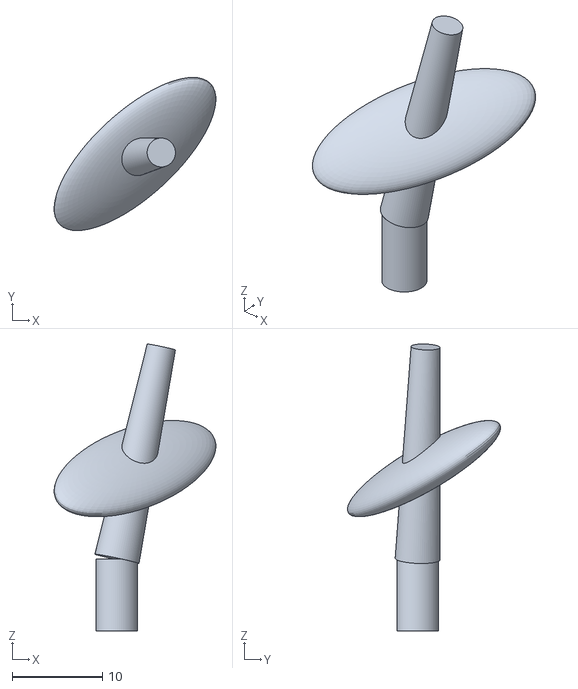
[picture p147: CAD file, 2026-10-10]
3D_Printer_Housing/v19_Apple_Sensor_Pod_5000mAh/19_apple_stem.stl
17.9 x 17.0 x 31.8
