sungmin9910/ColdChain-DigitalTwin-Platform/3D modeling/Neo-6m-0-001/Neo-6m-0-001.step

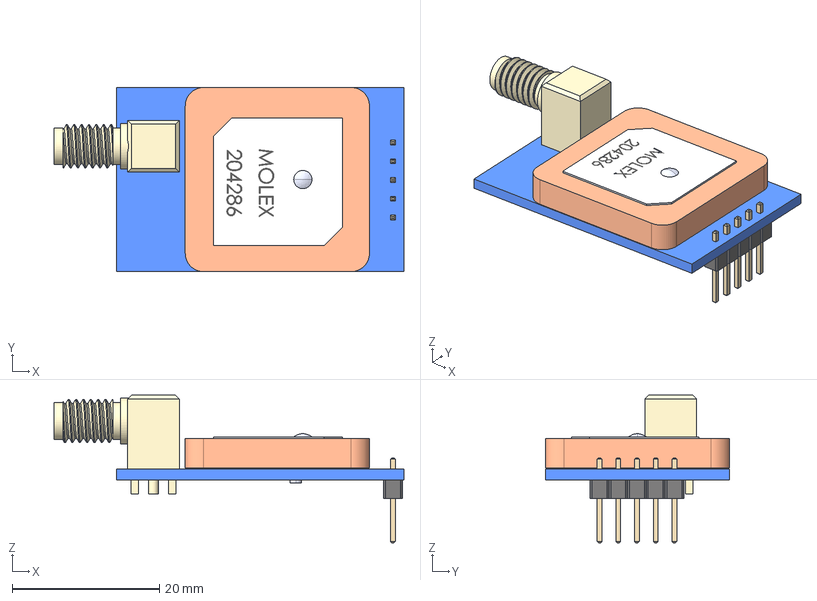
[picture p148: CAD file, 2026-07-27]
3D modeling/Neo-6m-0-001/Neo-6m-0-001.step
47.5 x 25.0 x 20.0 mm
Cubo x 2
L-KLS1-SMA006 v3 x 2
MOLEX 2042860001 x 2
PinHeader_1x05_P254mm_Vertical x 2
