sungmin9910/ColdChain-DigitalTwin-Platform/3D modeling/zsp32-s3-wroom-1-devkit-1.snapshot.9/ESP32-S3-WROOM-1_devkit_2xUSBC.FCStd

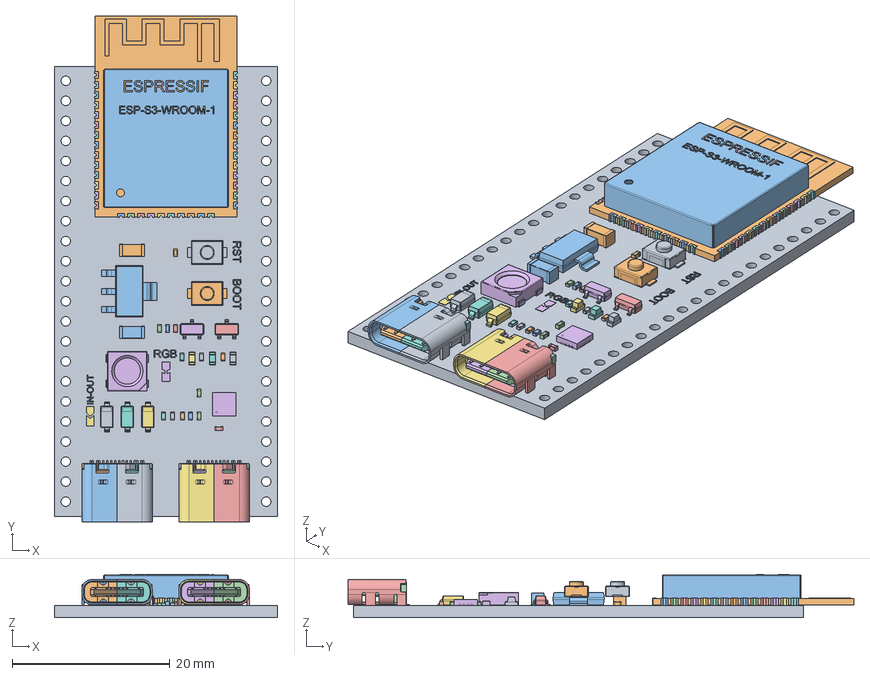
[picture p149: CAD file, 2026-07-27]
3D modeling/zsp32-s3-wroom-1-devkit-1.snapshot.9/ESP32-S3-WROOM-1_devkit_2xUSBC.FCStd
28.3 x 64.1 x 5.45 mm
Corps
PCB_mince
Text_ESP32
Text_ESP033
Text_ESP034
Text_ESP035
Text_ESP036
Text_ESP037
Text_ESP038
Text_ESP039
Text_ESP040
Text_ESP041
Text_ESP042
Text_ESP043
Text_ESP044
Text_ESP045
Text_Espressif
Text_Espressif001
Text_Espressif002
Text_Espressif003
Text_Espressif004
Text_Espressif005
Text_Espressif006
Text_Espressif007
Text_Espressif008
pin_002
pin_003
pin_004
pin_005
pin_006
pin_007
pin_008
pin_009
pin_010
pin_011
pin_012
pin_013
pin_014
pin_015
pin_016
pin_017
pin_018
pin_019
pin_020
pin_021
pin_022
pin_023
pin_024
pin_025
pin_026
pin_027
pin_028
pin_029
pin_030
pin_031
pin_032
pin_033
pin_034
pin_035
pin_036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
