sungmin9910/ColdChain-DigitalTwin-Platform/3D_Printer_Housing/10_cable_clip_abs.stl

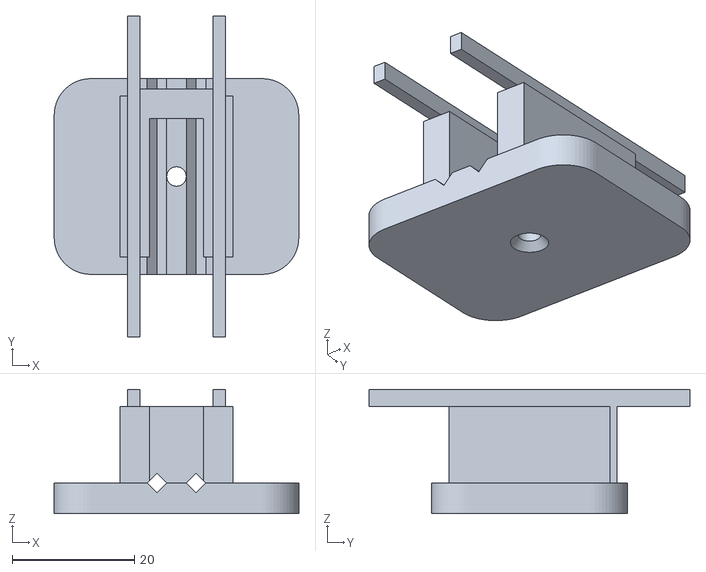
[picture p150: CAD file, 2026-09-09]
3D_Printer_Housing/10_cable_clip_abs.stl
40.0 x 52.5 x 20.3
