sungmin9910/ColdChain-DigitalTwin-Platform/3D_Printer_Housing/v06_Housing_And_Stand/06_housing_body.stl

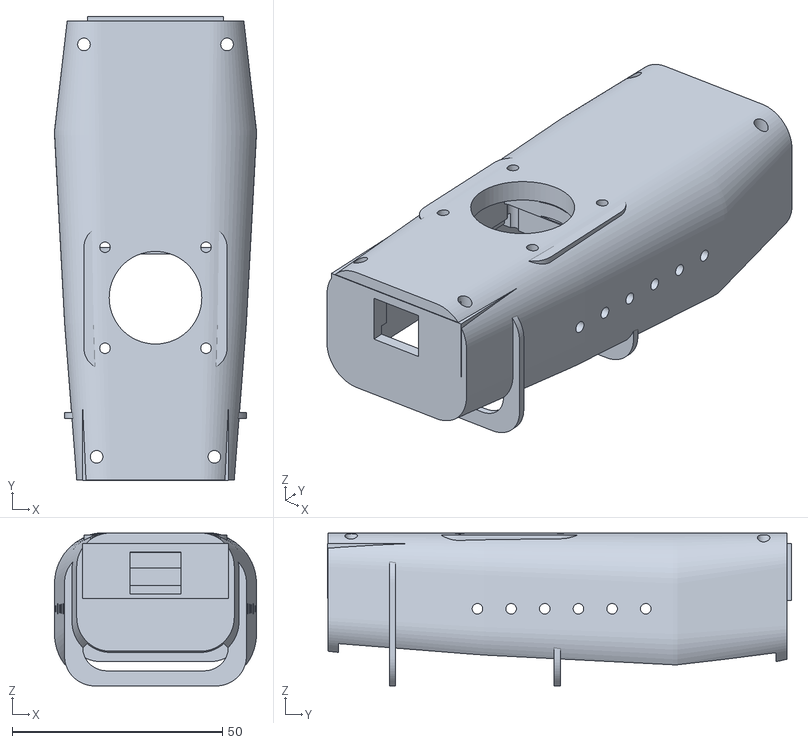
[picture p151: CAD file, 2026-05-31]
3D_Printer_Housing/v06_Housing_And_Stand/06_housing_body.stl
48.0 x 110.3 x 36.3
