sungmin9910/ColdChain-DigitalTwin-Platform/3D_Printer_Housing/v09_QR_Scanner_Housing_Snapfit/09_left_half_v2.stl

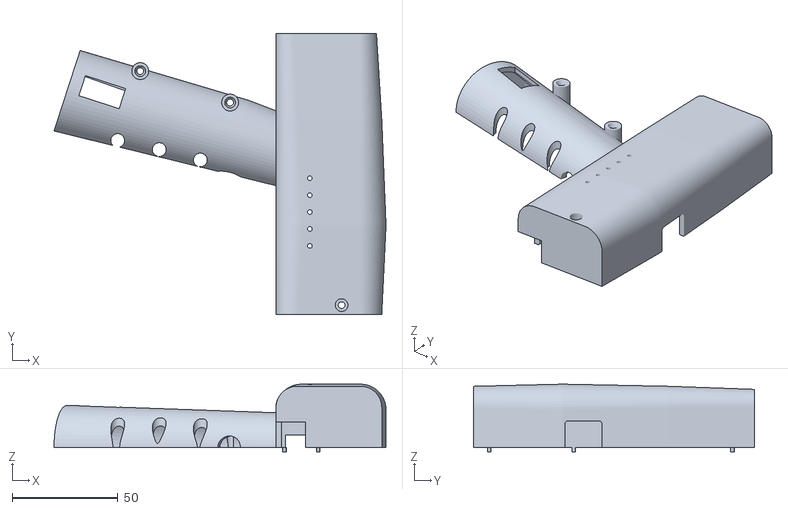
[picture p152: CAD file, 2026-06-23]
3D_Printer_Housing/v09_QR_Scanner_Housing_Snapfit/09_left_half_v2.stl
157.0 x 133.0 x 32.0
