sungmin9910/ColdChain-DigitalTwin-Platform/3D_Printer_Housing/v11_QR_Scanner_Housing_Flush_OLED/11_housing_right.stl

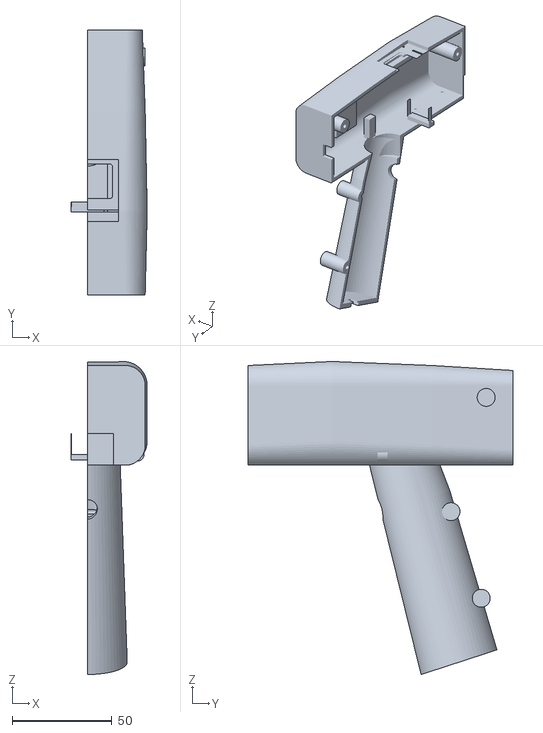
[picture p153: CAD file, 2026-06-22]
3D_Printer_Housing/v11_QR_Scanner_Housing_Flush_OLED/11_housing_right.stl
38.3 x 133.0 x 157.0
