sungmin9910/ColdChain-DigitalTwin-Platform/3D_Printer_Housing/v13_QR_Scanner_Housing_Slide_Fit/13_housing_left.stl

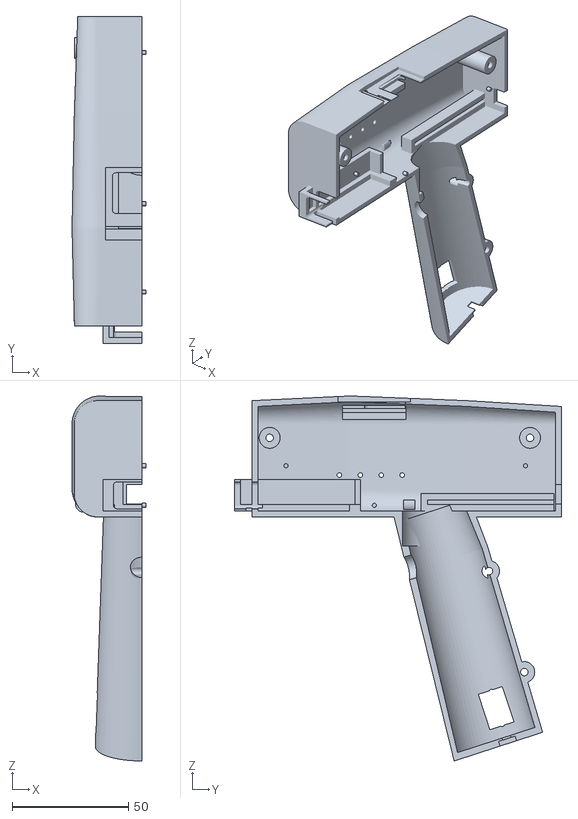
[picture p154: CAD file, 2026-06-22]
3D_Printer_Housing/v13_QR_Scanner_Housing_Slide_Fit/13_housing_left.stl
31.8 x 140.6 x 157.0
