sungmin9910/ColdChain-DigitalTwin-Platform/3D_Printer_Housing/v20_Apple_Sensor_Pod_Modular5000mAh/20_apple_front_shell.stl

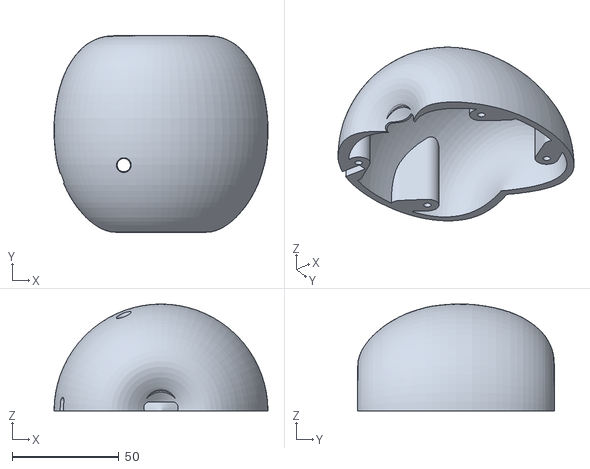
[picture p157: CAD file, 2026-10-10]
3D_Printer_Housing/v20_Apple_Sensor_Pod_Modular5000mAh/20_apple_front_shell.stl
100.0 x 91.9 x 50.0
