sungmin9910/ColdChain-DigitalTwin-Platform/3D modeling/Neo-6m-0-001/L-KLS1-SMA006 v3.step

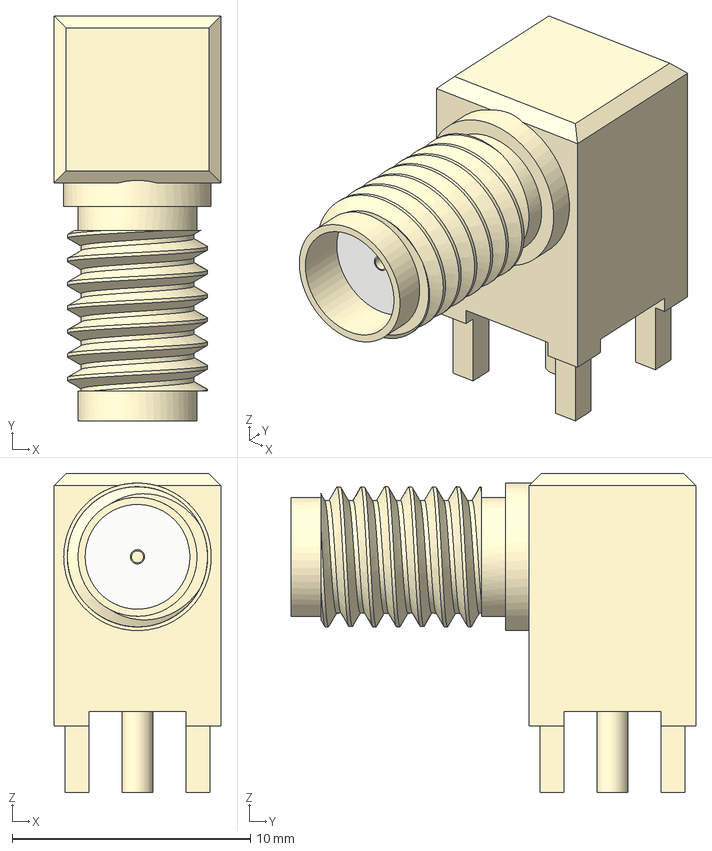
[picture p158: CAD file, 2026-07-27]
3D modeling/Neo-6m-0-001/L-KLS1-SMA006 v3.step
7.00 x 17.0 x 13.4 mm
