sungmin9910/ColdChain-DigitalTwin-Platform/3D_Printer_Housing/v06_Housing_And_Stand/06_housing_handle.stl

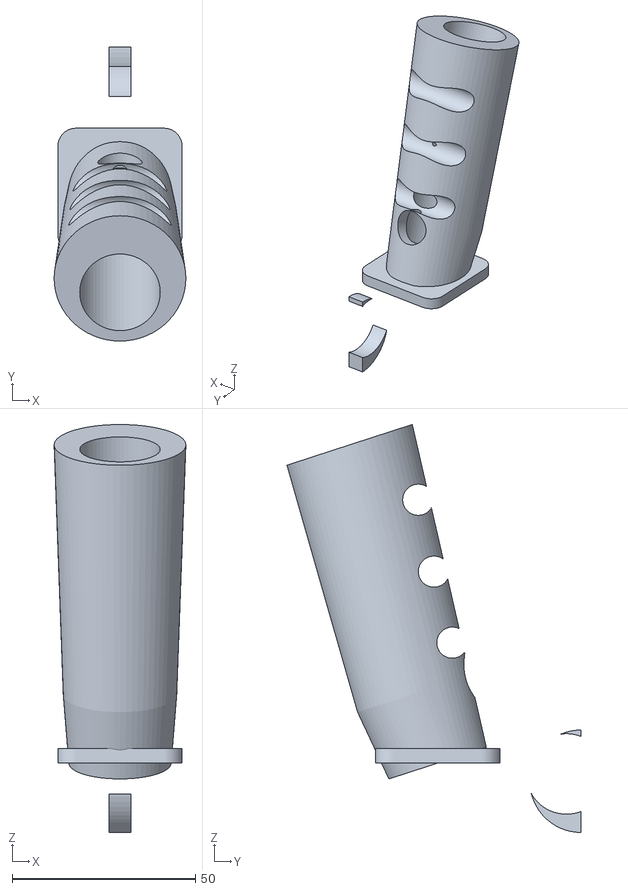
[picture p159: CAD file, 2026-05-31]
3D_Printer_Housing/v06_Housing_And_Stand/06_housing_handle.stl
36.0 x 80.3 x 111.4
