sungmin9910/ColdChain-DigitalTwin-Platform/3D_Printer_Housing/v09_QR_Scanner_Housing_Snapfit/09_trigger_v2.stl

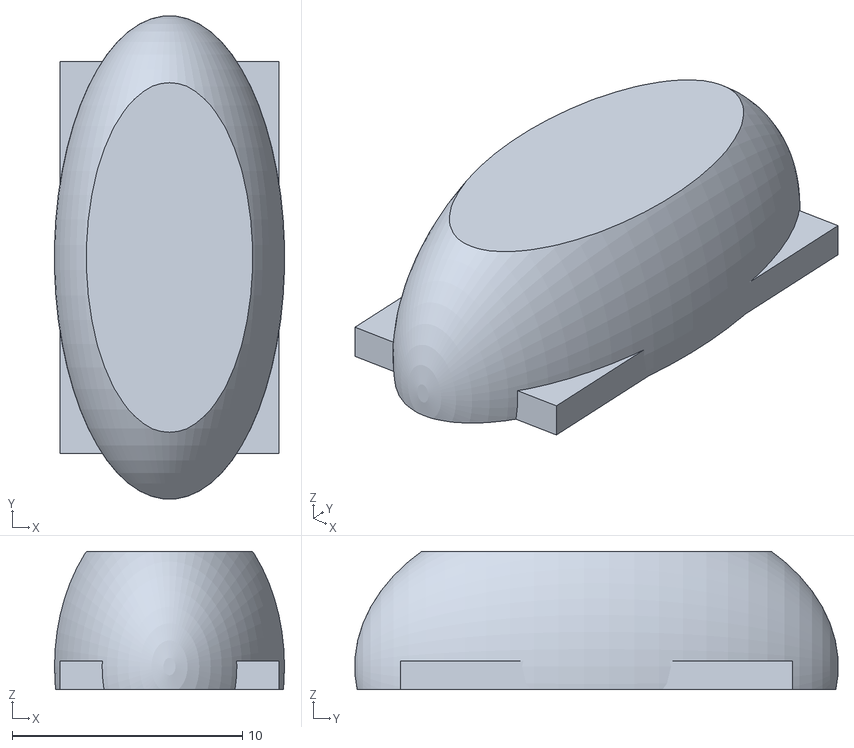
[picture p160: CAD file, 2026-06-23]
3D_Printer_Housing/v09_QR_Scanner_Housing_Snapfit/09_trigger_v2.stl
9.99 x 21.0 x 6.00
