sungmin9910/ColdChain-DigitalTwin-Platform/3D_Printer_Housing/v11_QR_Scanner_Housing_Flush_OLED/11_housing_left.stl

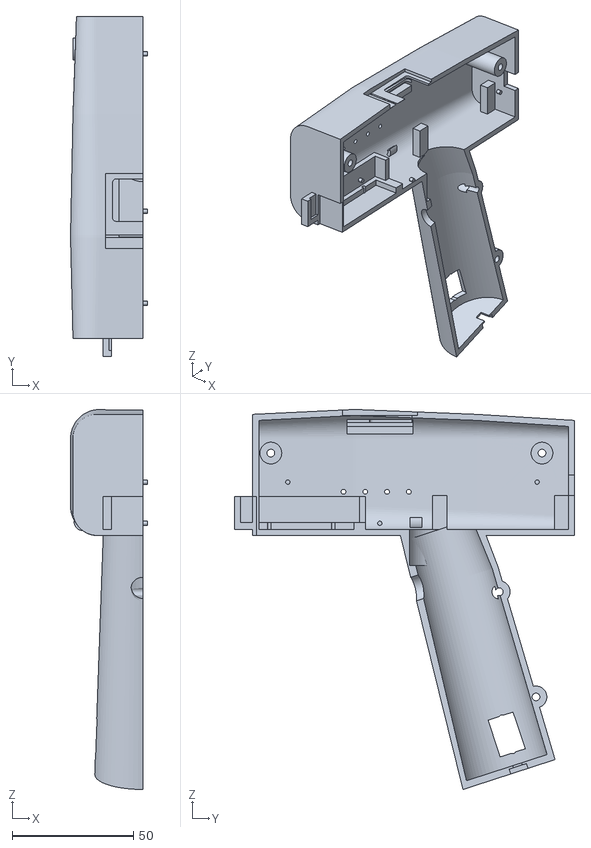
[picture p161: CAD file, 2026-06-22]
3D_Printer_Housing/v11_QR_Scanner_Housing_Flush_OLED/11_housing_left.stl
31.8 x 140.6 x 157.0
