sungmin9910/ColdChain-DigitalTwin-Platform/3D_Printer_Housing/v17_QR_Scanner_Housing/17_qr_scanner_housing_left_half.stl

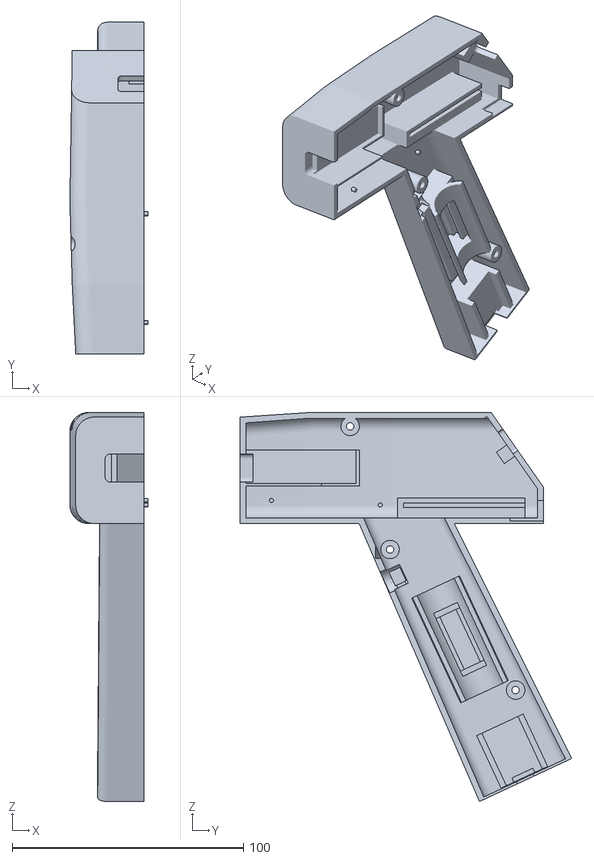
[picture p162: CAD file, 2026-07-07]
3D_Printer_Housing/v17_QR_Scanner_Housing/17_qr_scanner_housing_left_half.stl
33.8 x 143.3 x 168.1
