sungmin9910/ColdChain-DigitalTwin-Platform/3D_Printer_Housing/v18_Apple_Sensor_Pod/18_apple_front_shell.stl

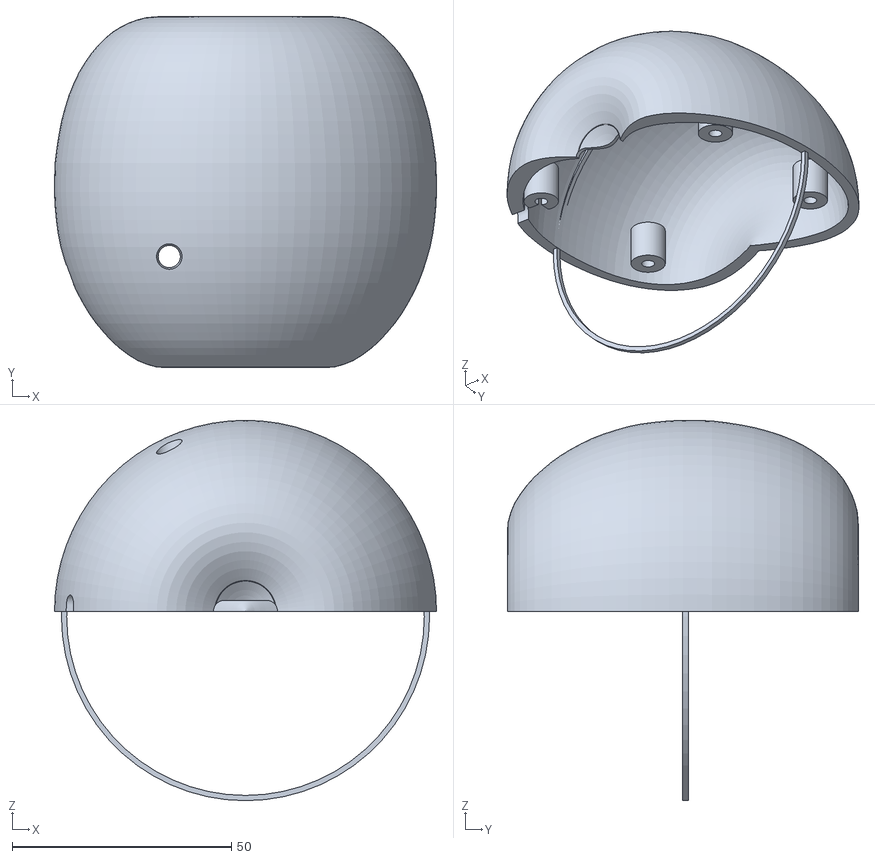
[picture p163: CAD file, 2026-09-14]
3D_Printer_Housing/v18_Apple_Sensor_Pod/18_apple_front_shell.stl
87.1 x 80.0 x 86.7
