sungmin9910/ColdChain-DigitalTwin-Platform/3D_Printer_Housing/v19_Apple_Sensor_Pod_5000mAh/19_apple_rear_shell.stl

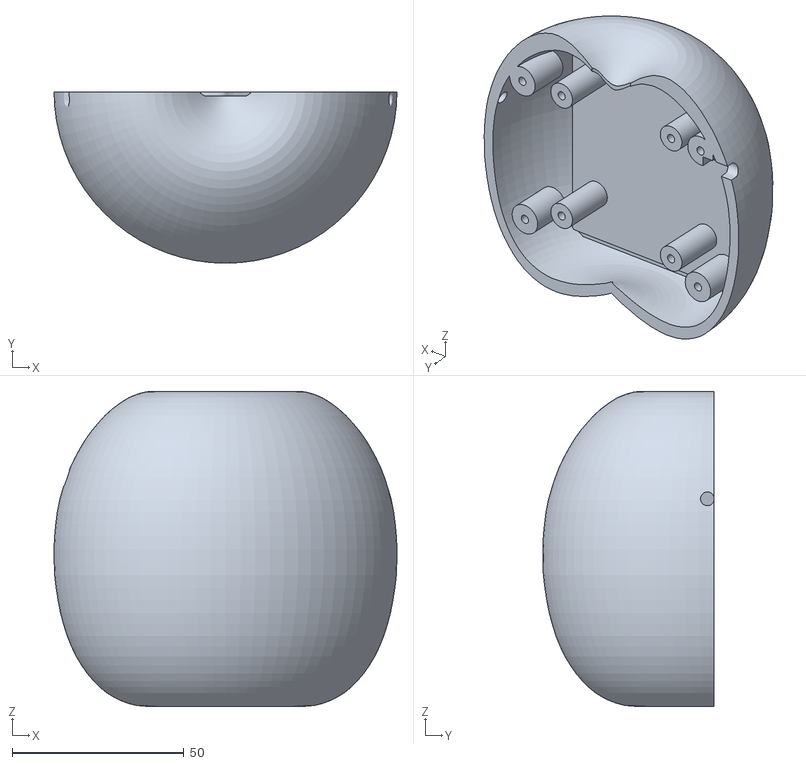
[picture p164: CAD file, 2026-10-10]
3D_Printer_Housing/v19_Apple_Sensor_Pod_5000mAh/19_apple_rear_shell.stl
100.0 x 50.0 x 91.9
