sungmin9910/ColdChain-DigitalTwin-Platform/3D modeling/Neo-6m-0-001/PinHeader.step

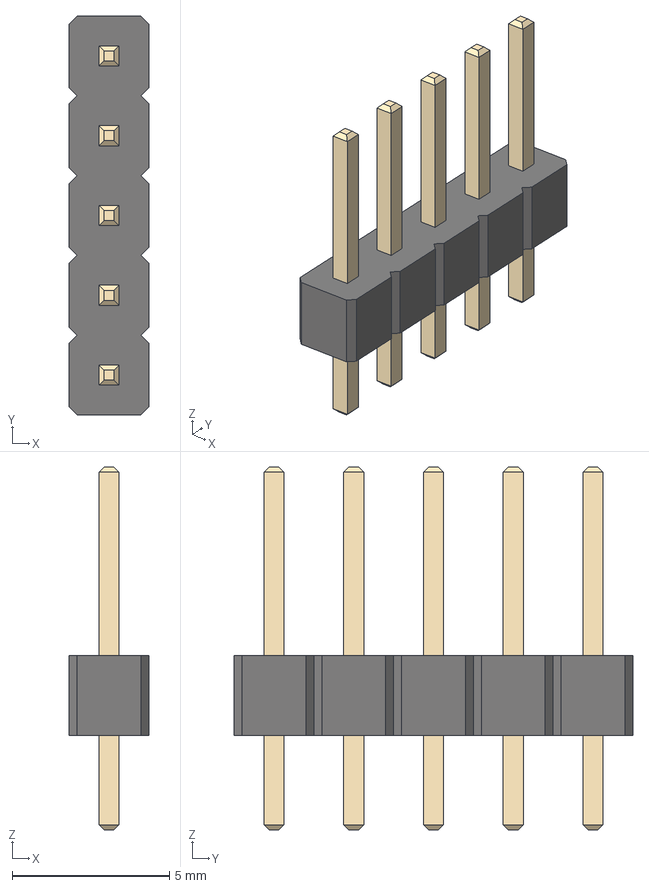
[picture p165: CAD file, 2026-07-27]
3D modeling/Neo-6m-0-001/PinHeader.step
2.54 x 12.7 x 11.5 mm
