sungmin9910/ColdChain-DigitalTwin-Platform/3D_Printer_Housing/v06_Housing_And_Stand/06_housing_lid.stl

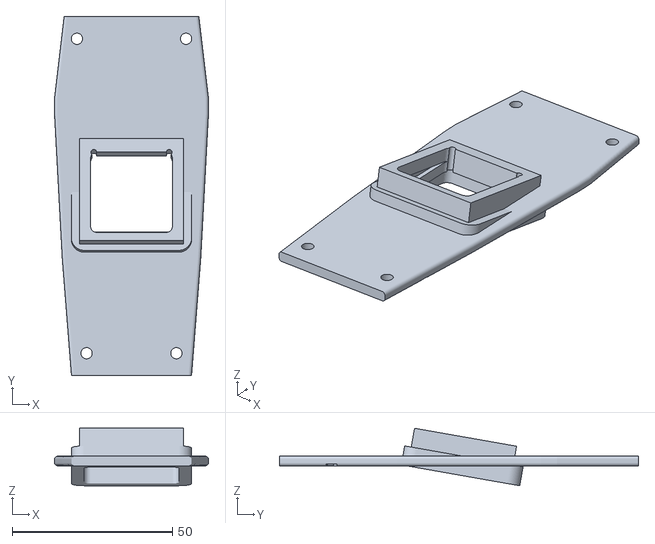
[picture p166: CAD file, 2026-05-31]
3D_Printer_Housing/v06_Housing_And_Stand/06_housing_lid.stl
48.0 x 112.0 x 17.9
