sungmin9910/ColdChain-DigitalTwin-Platform/3D_Printer_Housing/v09_QR_Scanner_Housing_Snapfit/09_right_half_v2.stl

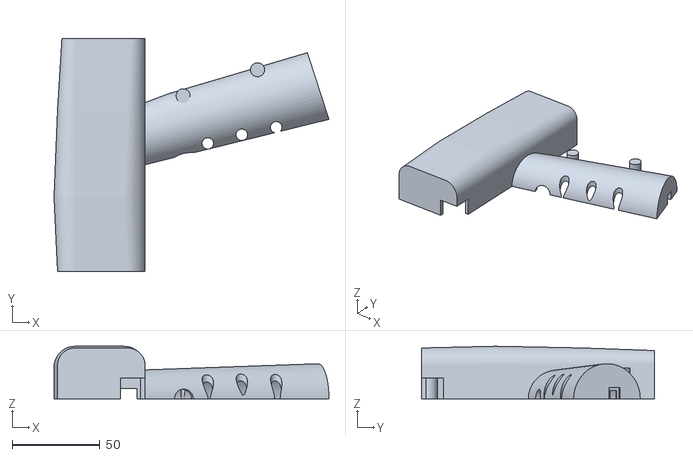
[picture p167: CAD file, 2026-06-23]
3D_Printer_Housing/v09_QR_Scanner_Housing_Snapfit/09_right_half_v2.stl
157.0 x 133.0 x 30.0
