sungmin9910/ColdChain-DigitalTwin-Platform/3D_Printer_Housing/v20_Apple_Sensor_Pod_Modular5000mAh/20_apple_battery_tray.stl

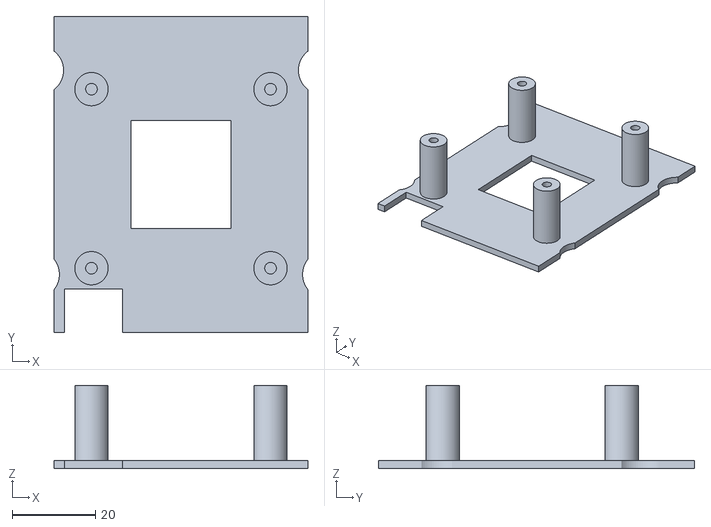
[picture p168: CAD file, 2026-10-10]
3D_Printer_Housing/v20_Apple_Sensor_Pod_Modular5000mAh/20_apple_battery_tray.stl
61.0 x 76.0 x 20.0
