sungmin9910/ColdChain-DigitalTwin-Platform/3D_Printer_Housing/v09_QR_Scanner_Housing_Snapfit/09_plug_v2.stl

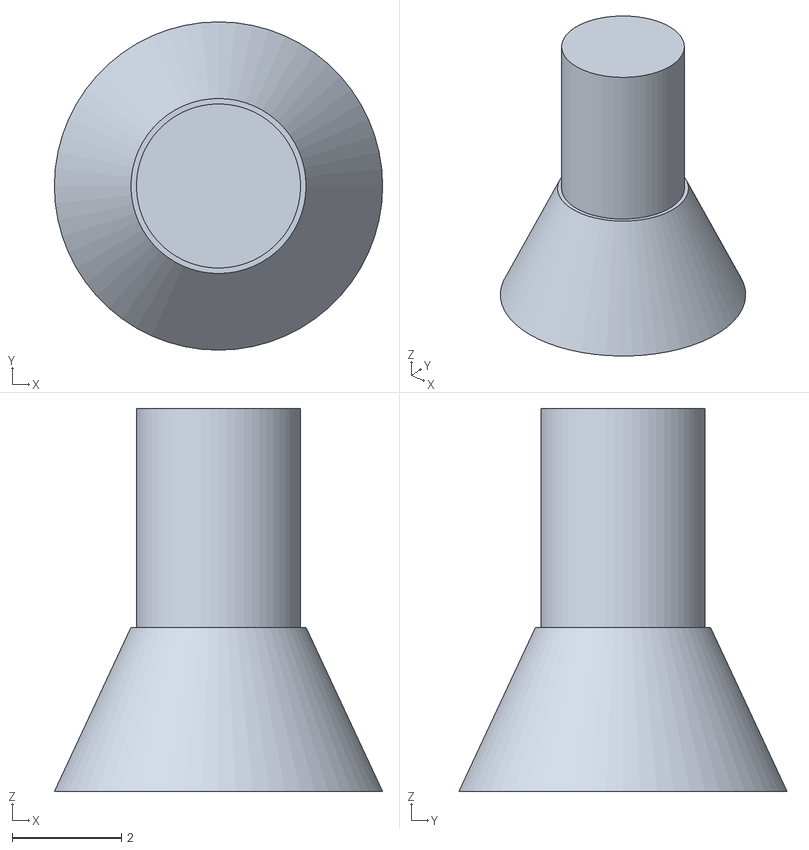
[picture p169: CAD file, 2026-06-23]
3D_Printer_Housing/v09_QR_Scanner_Housing_Snapfit/09_plug_v2.stl
6.00 x 6.00 x 7.00
