sungmin9910/ColdChain-DigitalTwin-Platform/3D_Printer_Housing/v09_QR_Scanner_Housing_Snapfit/09_print_all_v2.stl

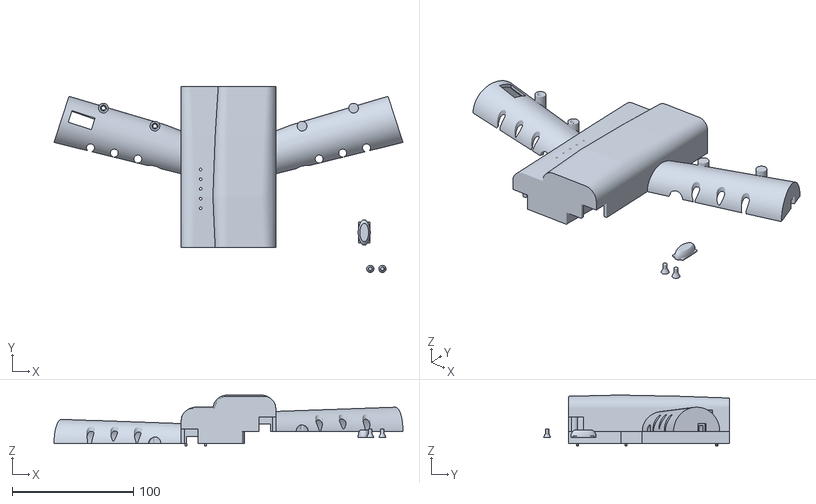
[picture p170: CAD file, 2026-06-23]
3D_Printer_Housing/v09_QR_Scanner_Housing_Snapfit/09_print_all_v2.stl
288.0 x 153.5 x 42.0
