sungmin9910/ColdChain-DigitalTwin-Platform/3D_Printer_Housing/v09_QR_Scanner_Housing_Snapfit/09_housing_left.stl

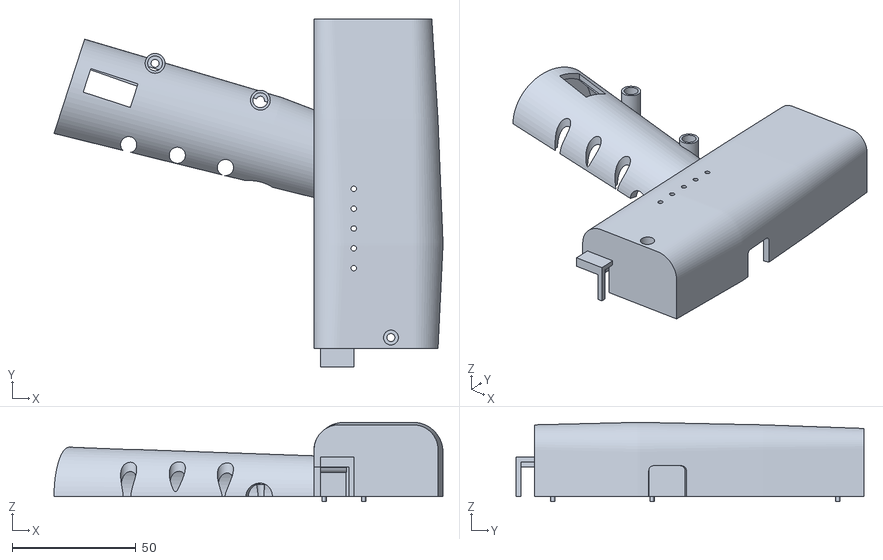
[picture p171: CAD file, 2026-06-22]
3D_Printer_Housing/v09_QR_Scanner_Housing_Snapfit/09_housing_left.stl
157.0 x 140.3 x 32.0
