sungmin9910/ColdChain-DigitalTwin-Platform/3D_Printer_Housing/v09_QR_Scanner_Housing_Snapfit/09_housing_print_all.stl

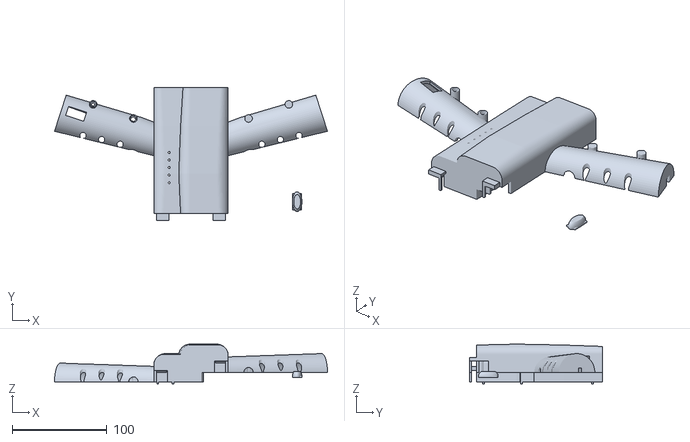
[picture p172: CAD file, 2026-06-22]
3D_Printer_Housing/v09_QR_Scanner_Housing_Snapfit/09_housing_print_all.stl
288.0 x 140.3 x 42.0
