sungmin9910/ColdChain-DigitalTwin-Platform/3D_Printer_Housing/v09_QR_Scanner_Housing_Snapfit/09_housing_right.stl

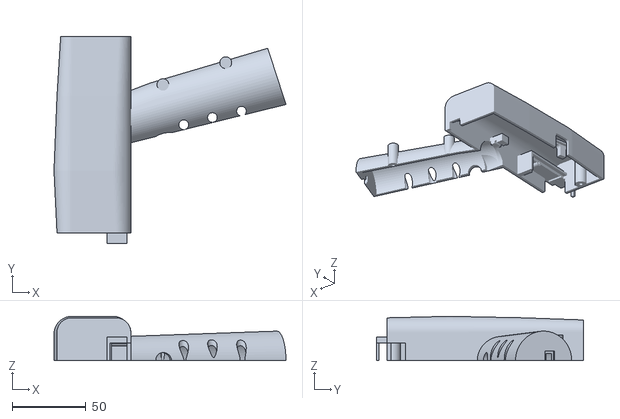
[picture p173: CAD file, 2026-06-22]
3D_Printer_Housing/v09_QR_Scanner_Housing_Snapfit/09_housing_right.stl
157.0 x 140.3 x 30.0
