sungmin9910/ColdChain-DigitalTwin-Platform/scratch/apple_profiles.scad

// Auto-generated apple profile coordinates

apple_outer_profile = [
  [0.0, -32.5],
  [1.22, -33.13],
  [2.44, -33.76],
  [3.65, -34.37],
  [4.86, -34.97],
  [6.08, -35.53],
  [7.28, -36.07],
  [8.49, -36.57],
  [9.7, -37.04],
  [10.92, -37.46],
  [12.15, -37.85],
  [13.4, -38.18],
  [14.68, -38.46],
  [15.99, -38.66],
  [17.35, -38.78],
  [18.77, -38.8],
  [20.25, -38.71],
  [21.78, -38.52],
  [23.32, -38.23],
  [24.86, -37.84],
  [26.38, -37.37],
  [27.85, -36.8],
  [29.3, -36.08],
  [30.7, -35.16],
  [32.07, -33.98],
  [33.42, -32.5],
  [34.72, -30.69],
  [35.99, -28.59],
  [37.19, -26.24],
  [38.33, -23.69],
  [39.39, -20.96],
  [40.35, -18.12],
  [41.2, -15.23],
  [41.93, -12.34],
  [42.53, -9.53],
  [42.98, -6.85],
  [43.29, -4.31],
  [43.47, -1.89],
  [43.54, 0.48],
  [43.53, 2.82],
  [43.45, 5.19],
  [43.31, 7.59],
  [43.1, 10.03],
  [42.8, 12.48],
  [42.41, 14.93],
  [41.9, 17.37],
  [41.29, 19.79],
  [40.58, 22.16],
  [39.77, 24.47],
  [38.86, 26.69],
  [37.87, 28.81],
  [36.78, 30.81],
  [35.61, 32.68],
  [34.33, 34.43],
  [32.95, 36.03],
  [31.47, 37.48],
  [29.9, 38.76],
  [28.26, 39.82],
  [26.59, 40.62],
  [24.92, 41.12],
  [23.26, 41.3],
  [21.62, 41.17],
  [20.01, 40.81],
  [18.4, 40.28],
  [16.8, 39.63],
  [15.2, 38.93],
  [13.62, 38.2],
  [12.07, 37.45],
  [10.58, 36.68],
  [9.17, 35.9],
  [7.85, 35.12],
  [6.63, 34.36],
  [5.51, 33.66],
  [4.48, 33.04],
  [3.55, 32.53],
  [2.72, 32.15],
  [1.97, 31.89],
  [1.28, 31.71],
  [0.63, 31.59],
  [0.0, 31.5],
];

apple_inner_profile = [
  [0.0, -29.0],
  [1.22, -29.64],
  [2.44, -30.27],
  [3.66, -30.89],
  [4.87, -31.48],
  [6.08, -32.03],
  [7.27, -32.55],
  [8.47, -33.03],
  [9.68, -33.47],
  [10.91, -33.88],
  [12.16, -34.24],
  [13.44, -34.57],
  [14.75, -34.84],
  [16.08, -35.05],
  [17.41, -35.17],
  [18.75, -35.2],
  [20.08, -35.12],
  [21.41, -34.94],
  [22.73, -34.66],
  [24.03, -34.31],
  [25.32, -33.89],
  [26.59, -33.38],
  [27.84, -32.74],
  [29.05, -31.93],
  [30.22, -30.88],
  [31.35, -29.55],
  [32.42, -27.92],
  [33.45, -26.03],
  [34.44, -23.89],
  [35.41, -21.55],
  [36.35, -19.04],
  [37.26, -16.41],
  [38.11, -13.72],
  [38.87, -11.04],
  [39.51, -8.42],
  [39.99, -5.93],
  [40.31, -3.59],
  [40.49, -1.36],
  [40.56, 0.8],
  [40.54, 2.93],
  [40.45, 5.08],
  [40.3, 7.26],
  [40.09, 9.47],
  [39.79, 11.72],
  [39.4, 13.99],
  [38.91, 16.3],
  [38.3, 18.62],
  [37.59, 20.9],
  [36.78, 23.12],
  [35.87, 25.24],
  [34.86, 27.22],
  [33.76, 29.04],
  [32.56, 30.71],
  [31.29, 32.23],
  [29.94, 33.6],
  [28.51, 34.82],
  [27.03, 35.87],
  [25.5, 36.73],
  [23.95, 37.37],
  [22.39, 37.75],
  [20.84, 37.85],
  [19.31, 37.71],
  [17.79, 37.38],
  [16.28, 36.89],
  [14.78, 36.31],
  [13.29, 35.69],
  [11.81, 35.04],
  [10.37, 34.38],
  [8.98, 33.73],
  [7.66, 33.08],
  [6.43, 32.46],
  [5.29, 31.87],
  [4.26, 31.35],
  [3.34, 30.89],
  [2.55, 30.52],
  [1.88, 30.25],
  [1.31, 30.06],
  [0.83, 29.94],
  [0.4, 29.86],
  [0.0, 29.8],
];
