sungmin9910/ColdChain-DigitalTwin-Platform/scratch/test_apple.scad

// test_apple.scad
$fn = 60;

apple_profile = [
  [0.0, -32.34],
  [1.21, -32.94],
  [2.42, -33.54],
  [3.64, -34.15],
  [4.86, -34.76],
  [6.08, -35.38],
  [7.3, -36.0],
  [8.52, -36.6],
  [9.74, -37.18],
  [10.95, -37.72],
  [12.15, -38.19],
  [13.33, -38.59],
  [14.51, -38.9],
  [15.72, -39.13],
  [16.95, -39.28],
  [18.25, -39.34],
  [19.6, -39.31],
  [21.01, -39.17],
  [22.44, -38.91],
  [23.9, -38.52],
  [25.37, -37.99],
  [26.82, -37.3],
  [28.26, -36.44],
  [29.67, -35.43],
  [31.06, -34.25],
  [32.42, -32.9],
  [33.73, -31.37],
  [35.0, -29.67],
  [36.2, -27.79],
  [37.33, -25.73],
  [38.38, -23.47],
  [39.35, -21.03],
  [40.22, -18.44],
  [40.99, -15.73],
  [41.66, -12.94],
  [42.24, -10.08],
  [42.71, -7.2],
  [43.07, -4.32],
  [43.32, -1.48],
  [43.47, 1.31],
  [43.5, 3.99],
  [43.43, 6.57],
  [43.26, 9.05],
  [43.0, 11.42],
  [42.67, 13.7],
  [42.27, 15.88],
  [41.8, 17.98],
  [41.24, 20.01],
  [40.59, 21.99],
  [39.82, 23.94],
  [38.92, 25.87],
  [37.89, 27.78],
  [36.73, 29.64],
  [35.42, 31.44],
  [33.98, 33.15],
  [32.4, 34.75],
  [30.71, 36.2],
  [28.95, 37.43],
  [27.18, 38.41],
  [25.43, 39.06],
  [23.74, 39.34],
  [22.11, 39.29],
  [20.52, 38.97],
  [18.92, 38.44],
  [17.31, 37.79],
  [15.65, 37.08],
  [13.96, 36.31],
  [12.29, 35.51],
  [10.69, 34.66],
  [9.18, 33.78],
  [7.81, 32.86],
  [6.57, 31.95],
  [5.46, 31.08],
  [4.46, 30.32],
  [3.55, 29.7],
  [2.74, 29.25],
  [1.99, 28.97],
  [1.3, 28.8],
  [0.64, 28.71],
  [0.0, 28.66]
];

// Revolve solid
module apple_solid() {
    rotate_extrude(angle=360, $fn=80) {
        polygon(concat([[0, apple_profile[0][1]]], apple_profile, [[0, apple_profile[len(apple_profile)-1][1]]]));
    }
}

// Hollow out with uniform wall thickness
module apple_shell(wall=2.8) {
    difference() {
        apple_solid();
        // Inner cavity
        scale([(87 - 2*wall)/87, (87 - 2*wall)/87, (78 - 2*wall)/78])
            apple_solid();
    }
}

// Split cut for inspection
difference() {
    color([0.85, 0.15, 0.15])
    apple_shell(wall=3.0);
    translate([0, -100, -100])
        cube([200, 200, 200]);
}

// PCB mockup inside
color([0.1, 0.5, 0.2, 0.9])
translate([0, 0, 5])
cube([50, 1.6, 50], center=true);

// Battery mockup below PCB
color([0.7, 0.7, 0.7, 0.9])
translate([0, 0, -26])
cube([48, 8, 25], center=true);
