sungmin9910/ColdChain-DigitalTwin-Platform/3D_Printer_Housing/10_cable_clip_abs_preview.png

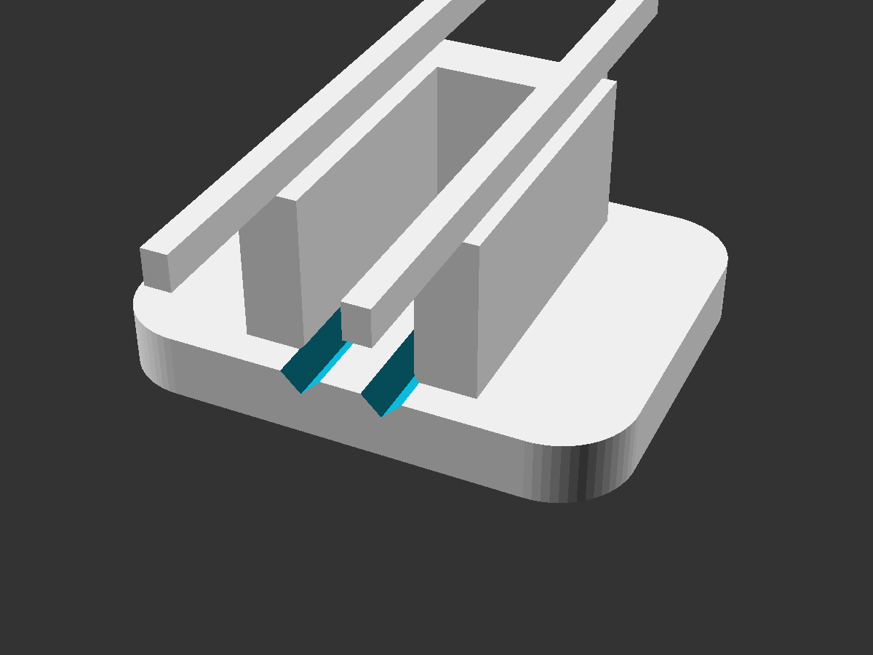
3D_Printer_Housing/10_cable_clip_abs_preview.png
