sungmin9910/ColdChain-DigitalTwin-Platform/3D_Printer_Housing/10_cable_clip_preview.png

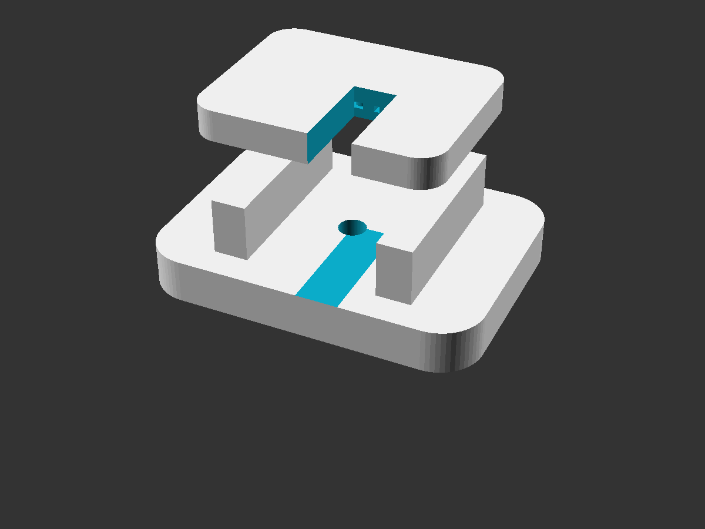
3D_Printer_Housing/10_cable_clip_preview.png
