sungmin9910/ColdChain-DigitalTwin-Platform/3D_Printer_Housing/v06_Housing_And_Stand/06_assembly_view.png

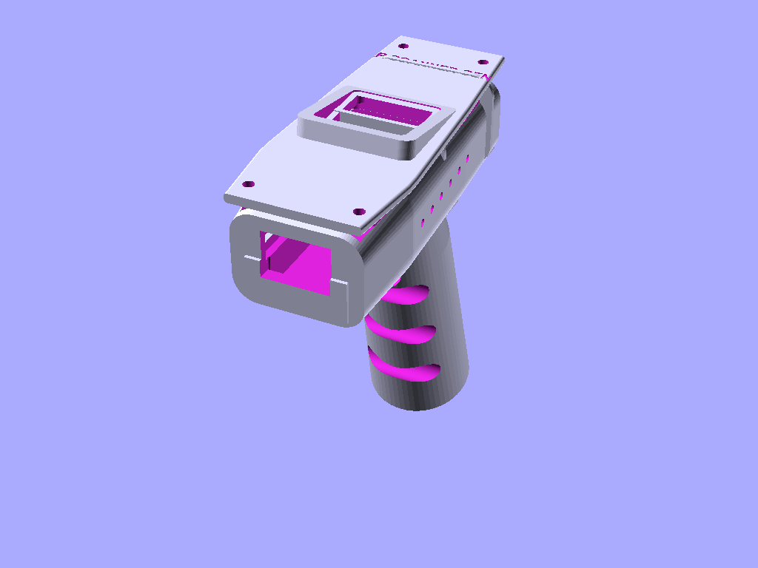
3D_Printer_Housing/v06_Housing_And_Stand/06_assembly_view.png
