sungmin9910/ColdChain-DigitalTwin-Platform/3D_Printer_Housing/v07_Coldchain_Sensor_Pod/07_exploded_view.png

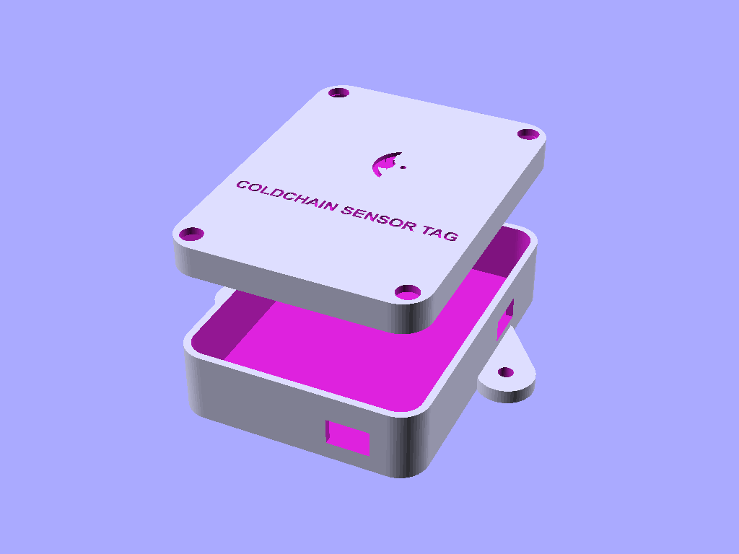
3D_Printer_Housing/v07_Coldchain_Sensor_Pod/07_exploded_view.png
