sungmin9910/ColdChain-DigitalTwin-Platform/3D_Printer_Housing/v09_QR_Scanner_Housing_Snapfit/09_finished_product_render.png

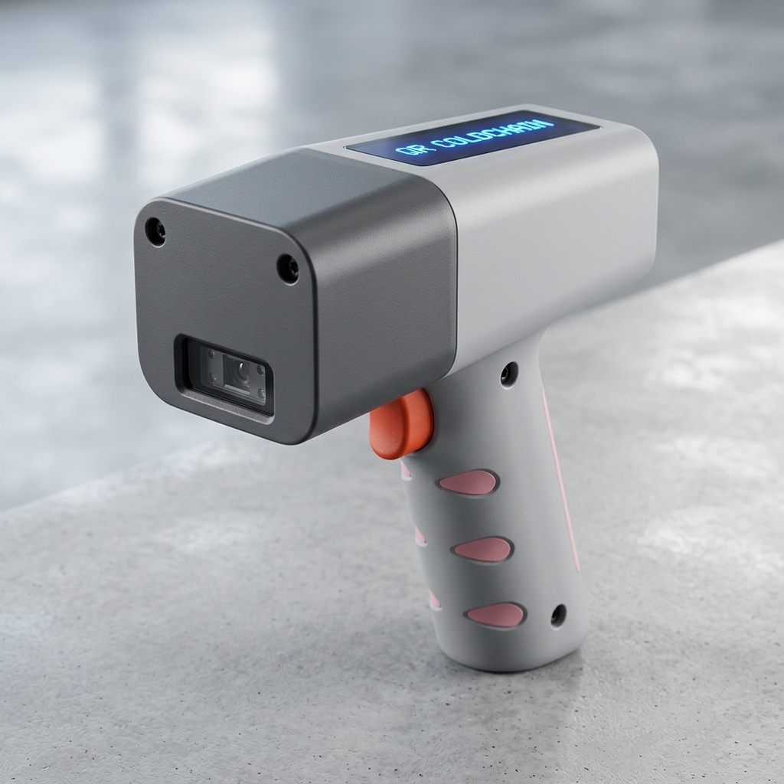
3D_Printer_Housing/v09_QR_Scanner_Housing_Snapfit/09_finished_product_render.png
