sungmin9910/ColdChain-DigitalTwin-Platform/3D_Printer_Housing/v10_QR_Scanner_Housing_Industrial/10_assembly_view.png

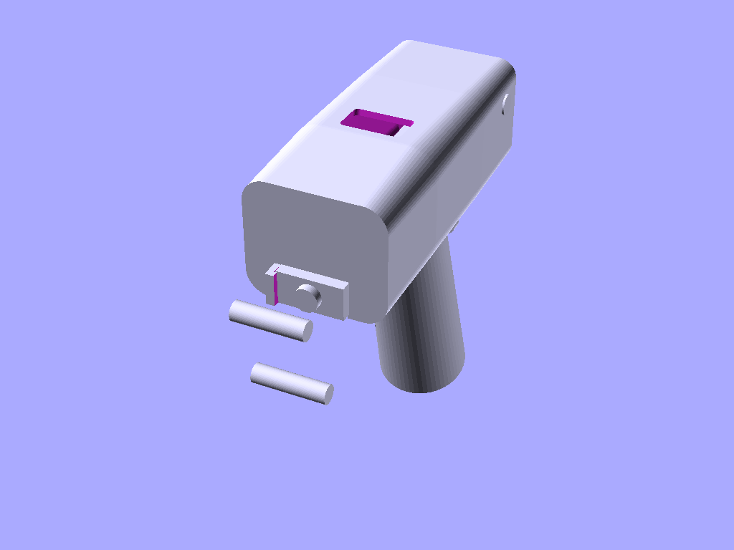
3D_Printer_Housing/v10_QR_Scanner_Housing_Industrial/10_assembly_view.png
