sungmin9910/ColdChain-DigitalTwin-Platform/3D_Printer_Housing/v11_QR_Scanner_Housing_Flush_OLED/11_cross_section_view.png

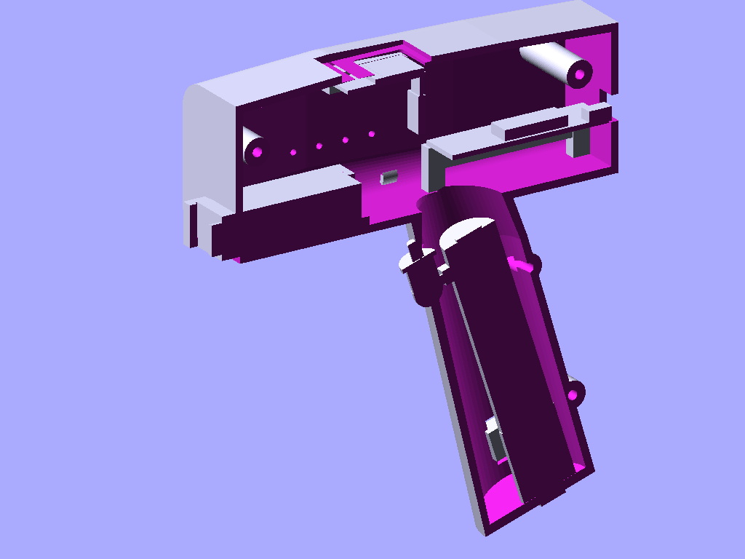
3D_Printer_Housing/v11_QR_Scanner_Housing_Flush_OLED/11_cross_section_view.png
