sungmin9910/ColdChain-DigitalTwin-Platform/3D_Printer_Housing/v14_QR_Scanner_Housing_Final/14_right_half_view.png

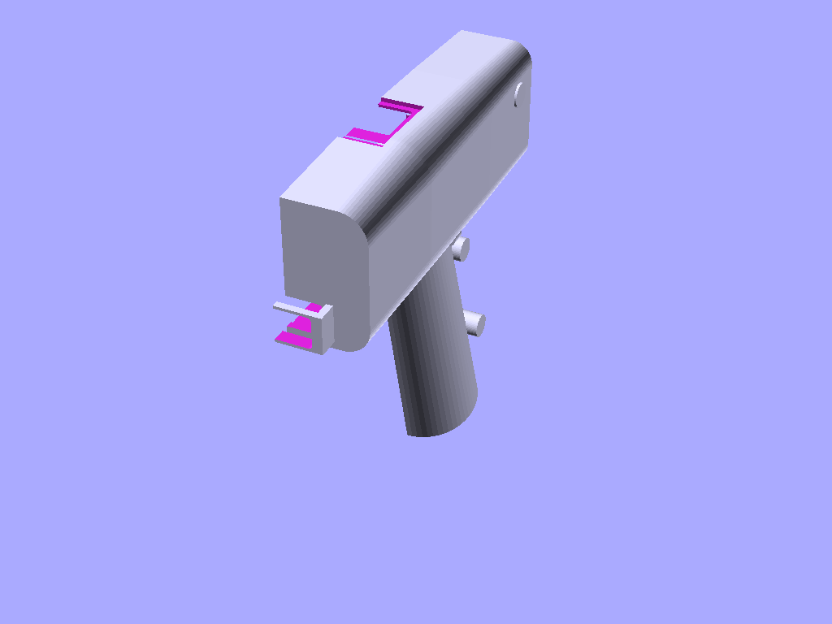
3D_Printer_Housing/v14_QR_Scanner_Housing_Final/14_right_half_view.png
