sungmin9910/ColdChain-DigitalTwin-Platform/3D_Printer_Housing/v17_QR_Scanner_Housing/hardware_mockups_assembly.png

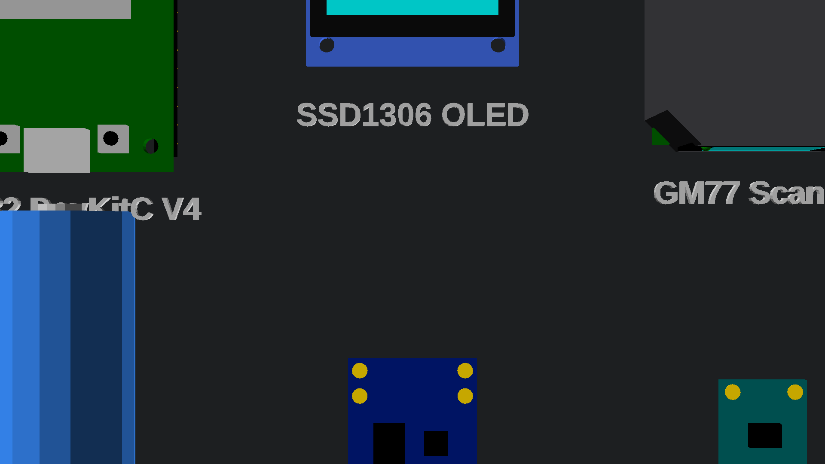
3D_Printer_Housing/v17_QR_Scanner_Housing/hardware_mockups_assembly.png
