sungmin9910/ColdChain-DigitalTwin-Platform/3D_Printer_Housing/v17_QR_Scanner_Housing/system_assembly_3d.png

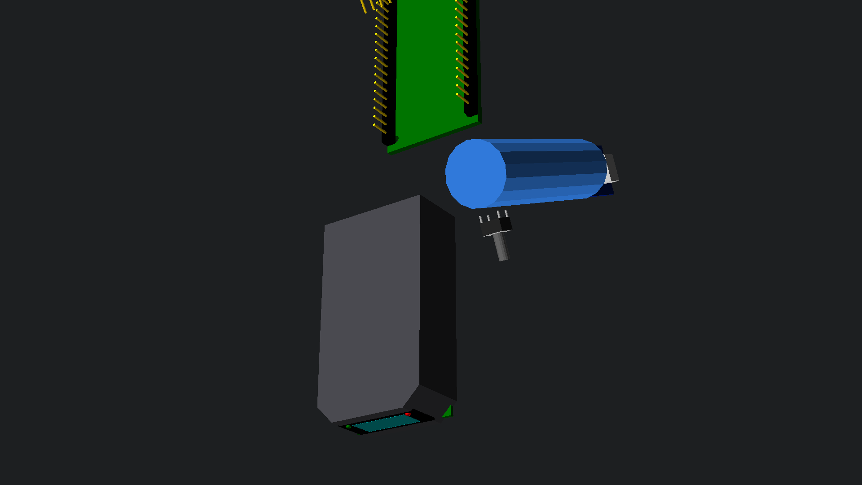
3D_Printer_Housing/v17_QR_Scanner_Housing/system_assembly_3d.png
