sungmin9910/ColdChain-DigitalTwin-Platform/3D_Printer_Housing/v18_Apple_Sensor_Pod/18_assembly_view.png

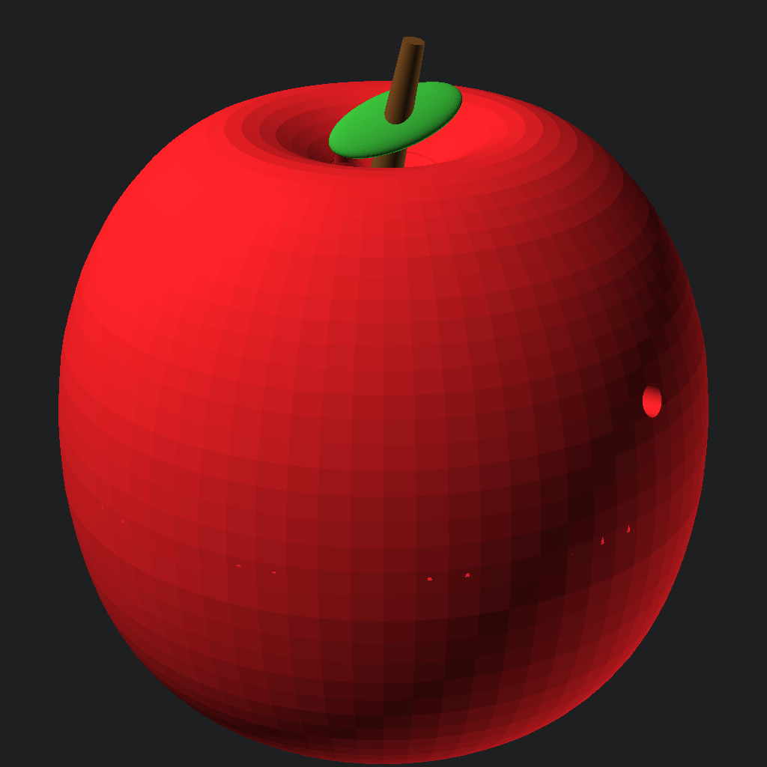
3D_Printer_Housing/v18_Apple_Sensor_Pod/18_assembly_view.png
