sungmin9910/ColdChain-DigitalTwin-Platform/3D_Printer_Housing/v19_Apple_Sensor_Pod_5000mAh/19_assembly_view.png

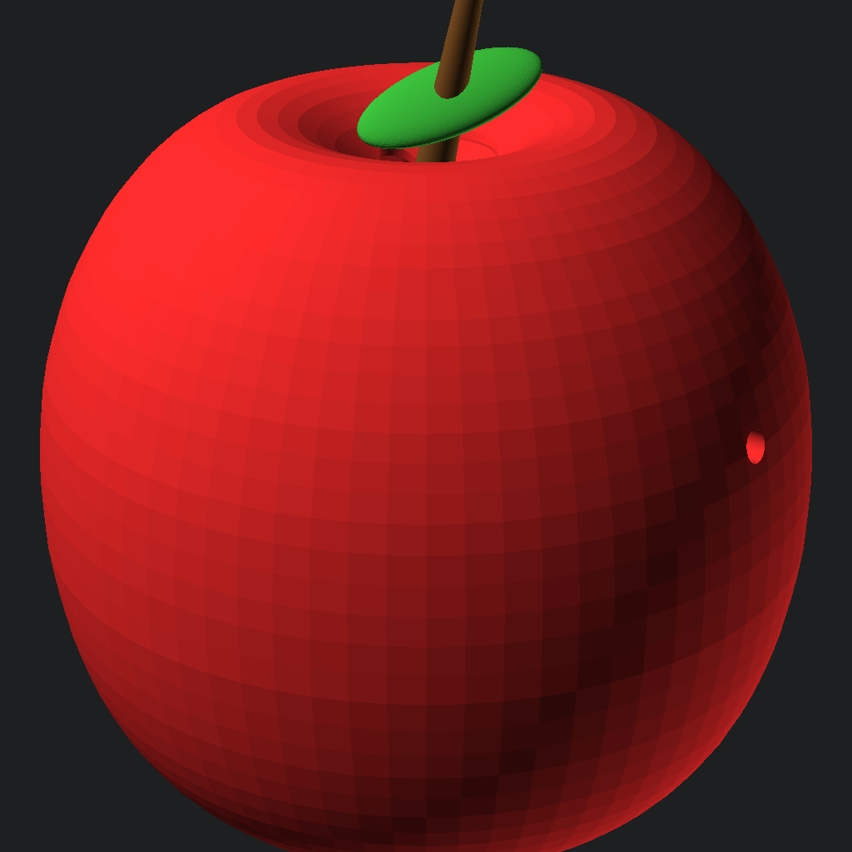
3D_Printer_Housing/v19_Apple_Sensor_Pod_5000mAh/19_assembly_view.png
