sungmin9910/ColdChain-DigitalTwin-Platform/3D_Printer_Housing/v20_Apple_Sensor_Pod_Modular5000mAh/20_boss_rear_wall_close.png

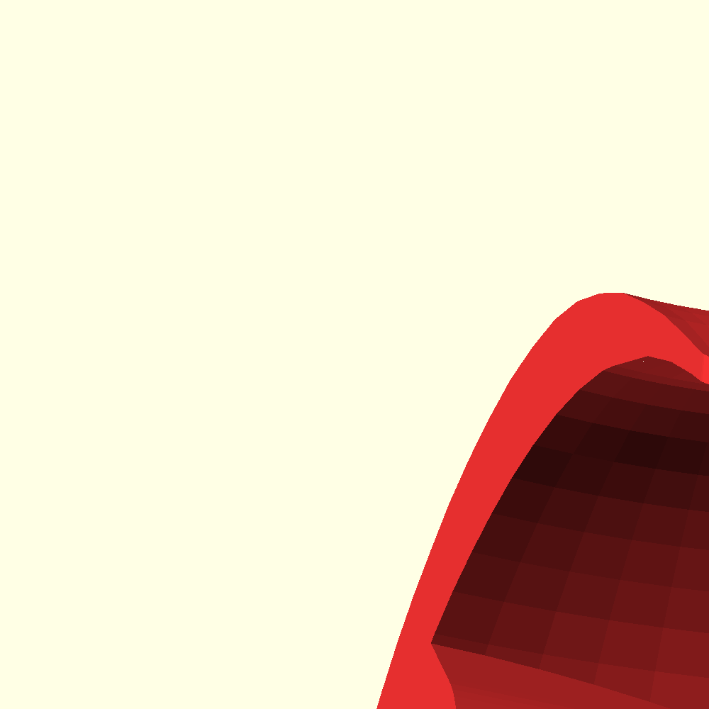
3D_Printer_Housing/v20_Apple_Sensor_Pod_Modular5000mAh/20_boss_rear_wall_close.png
