sungmin9910/ColdChain-DigitalTwin-Platform/3D_Printer_Housing/v20_Apple_Sensor_Pod_Modular5000mAh/20_part5_front_shell.png

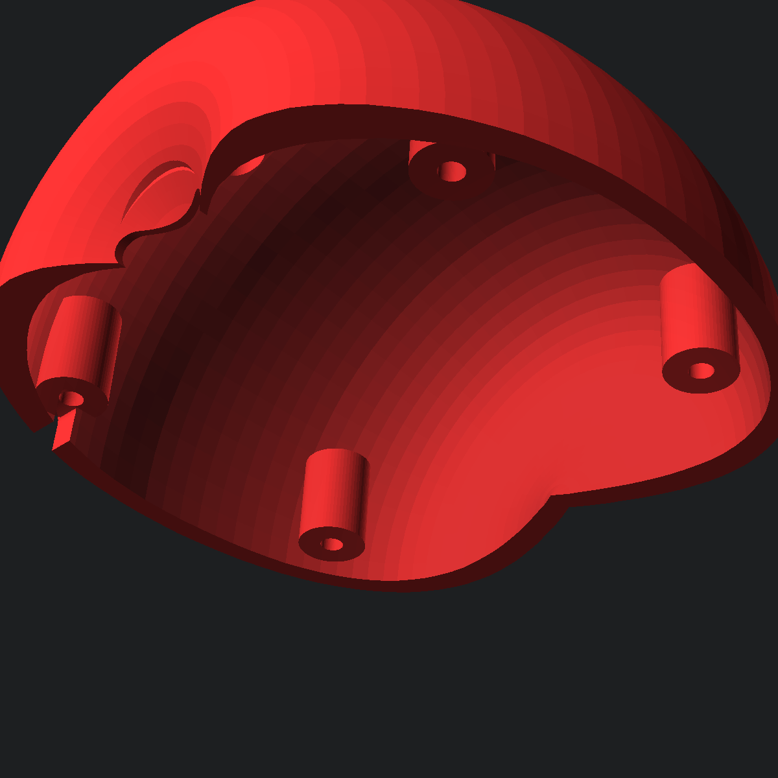
3D_Printer_Housing/v20_Apple_Sensor_Pod_Modular5000mAh/20_part5_front_shell.png
