sungmin9910/ColdChain-DigitalTwin-Platform/3D_Printer_Housing/v20_Apple_Sensor_Pod_Modular5000mAh/20_print_layout_view.png

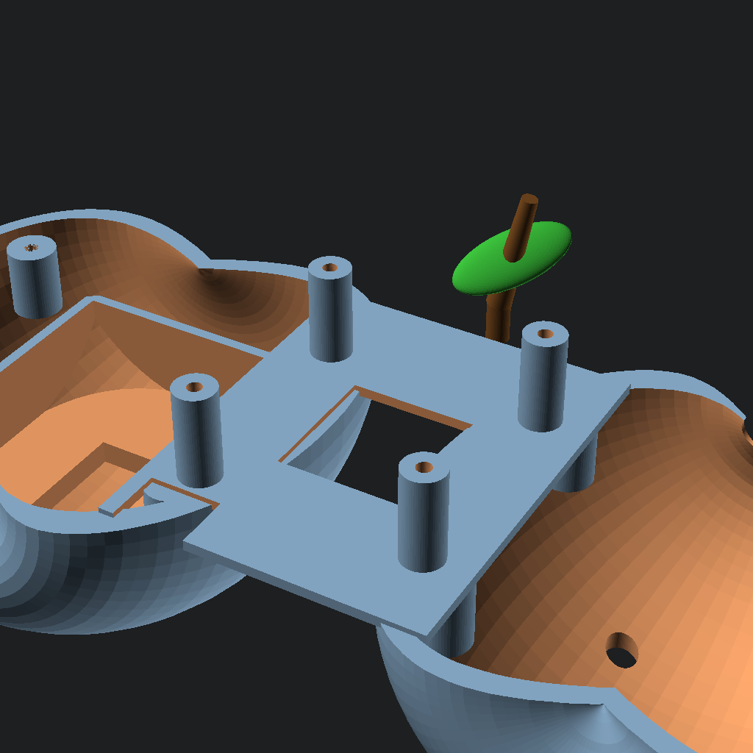
3D_Printer_Housing/v20_Apple_Sensor_Pod_Modular5000mAh/20_print_layout_view.png
