sungmin9910/ColdChain-DigitalTwin-Platform/scratch/guide_your_board.png

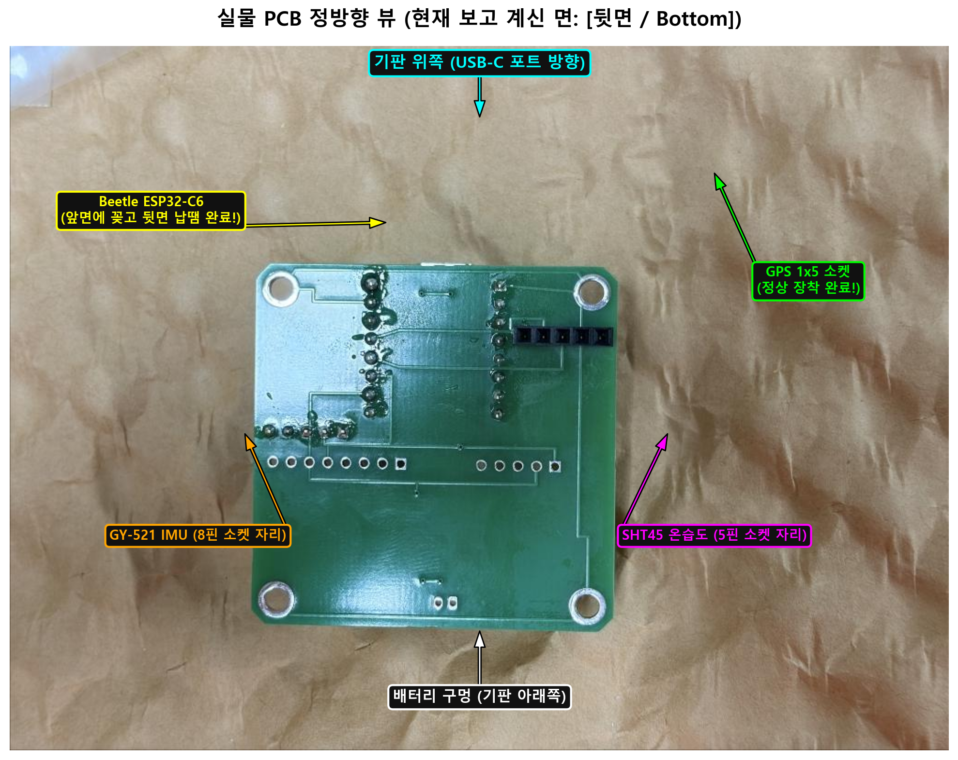
scratch/guide_your_board.png
