sungmin9910/ColdChain-DigitalTwin-Platform/3D modeling/CarrierBoard_BeetleC6_EdgeUSB_50x50_NoText/Fig_CarrierBoard_Routing_Verification.png

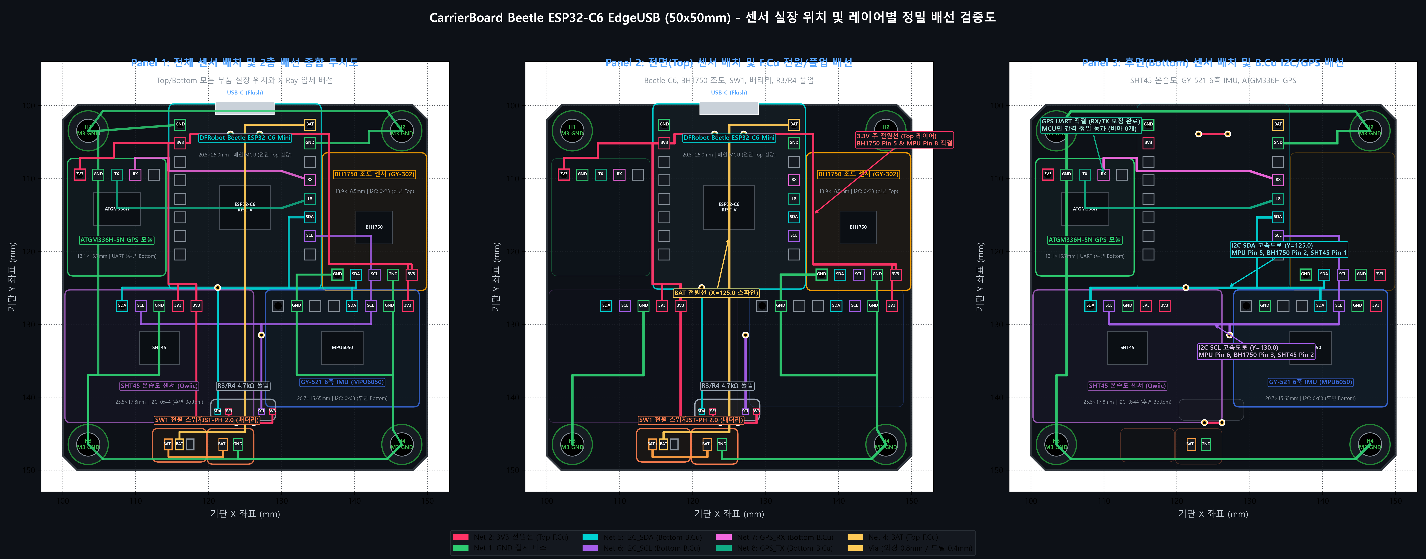
3D modeling/CarrierBoard_BeetleC6_EdgeUSB_50x50_NoText/Fig_CarrierBoard_Routing_Verification.png
