sungmin9910/ColdChain-DigitalTwin-Platform/scratch/test_apple.png

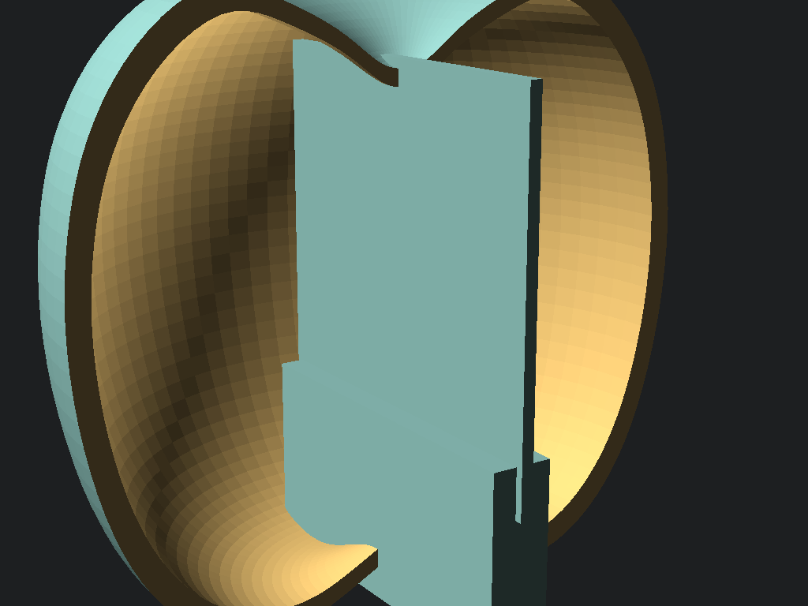
scratch/test_apple.png
