sungmin9910/ColdChain-DigitalTwin-Platform/scratch/font_renderer.py

# Vector stroke font renderer for Gerber and PCB silkscreen

# 5x7 Font definitions (grid coordinates: x in [0, 4], y in [0, 6])
FONT_STROKES = {
    'A': [((0,0),(0,5)), ((0,5),(2,7)), ((2,7),(4,5)), ((4,5),(4,0)), ((0,3),(4,3))],
    'B': [((0,0),(0,7)), ((0,7),(3,7)), ((3,7),(4,5.5)), ((4,5.5),(3,4)), ((0,4),(3,4)), ((3,4),(4,2)), ((4,2),(3,0)), ((3,0),(0,0))],
    'C': [((4,6),(1,6)), ((1,6),(0,5)), ((0,5),(0,2)), ((0,2),(1,0)), ((1,0),(4,0))],
    'D': [((0,0),(0,7)), ((0,7),(2.5,7)), ((2.5,7),(4,5)), ((4,5),(4,2)), ((4,2),(2.5,0)), ((2.5,0),(0,0))],
    'E': [((4,7),(0,7)), ((0,7),(0,0)), ((0,0),(4,0)), ((0,3.5),(3,3.5))],
    'F': [((4,7),(0,7)), ((0,7),(0,0)), ((0,3.5),(3,3.5))],
    'G': [((4,6),(1,6)), ((1,6),(0,5)), ((0,5),(0,2)), ((0,2),(1,0)), ((1,0),(4,0)), ((4,0),(4,3.5)), ((4,3.5),(2,3.5))],
    'H': [((0,0),(0,7)), ((4,0),(4,7)), ((0,3.5),(4,3.5))],
    'I': [((0,7),(4,7)), ((2,7),(2,0)), ((0,0),(4,0))],
    'J': [((0,2),(1,0)), ((1,0),(3,0)), ((3,0),(4,1)), ((4,1),(4,7)), ((2,7),(4,7))],
    'K': [((0,0),(0,7)), ((4,7),(0,3.5)), ((1,4.5),(4,0))],
    'L': [((0,7),(0,0)), ((0,0),(4,0))],
    'M': [((0,0),(0,7)), ((0,7),(2,3.5)), ((2,3.5),(4,7)), ((4,7),(4,0))],
    'N': [((0,0),(0,7)), ((0,7),(4,0)), ((4,0),(4,7))],
    'O': [((1,7),(3,7)), ((3,7),(4,5)), ((4,5),(4,2)), ((4,2),(3,0)), ((3,0),(1,0)), ((1,0),(0,2)), ((0,2),(0,5)), ((0,5),(1,7))],
    'P': [((0,0),(0,7)), ((0,7),(3,7)), ((3,7),(4,5.5)), ((4,5.5),(3,4)), ((3,4),(0,4))],
    'Q': [((1,7),(3,7)), ((3,7),(4,5)), ((4,5),(4,2)), ((4,2),(3,0)), ((3,0),(1,0)), ((1,0),(0,2)), ((0,2),(0,5)), ((0,5),(1,7)), ((2,2),(4,0))],
    'R': [((0,0),(0,7)), ((0,7),(3,7)), ((3,7),(4,5.5)), ((4,5.5),(3,4)), ((3,4),(0,4)), ((2,4),(4,0))],
    'S': [((4,6),(3,7)), ((3,7),(1,7)), ((1,7),(0,6)), ((0,6),(0,4.5)), ((0,4.5),(1,3.5)), ((1,3.5),(3,3.5)), ((3,3.5),(4,2.5)), ((4,2.5),(4,1)), ((4,1),(3,0)), ((3,0),(1,0)), ((1,0),(0,1))],
    'T': [((0,7),(4,7)), ((2,7),(2,0))],
    'U': [((0,7),(0,2)), ((0,2),(1,0)), ((1,0),(3,0)), ((3,0),(4,2)), ((4,2),(4,7))],
    'V': [((0,7),(2,0)), ((2,0),(4,7))],
    'W': [((0,7),(1,0)), ((1,0),(2,4)), ((2,4),(3,0)), ((3,0),(4,7))],
    'X': [((0,0),(4,7)), ((0,7),(4,0))],
    'Y': [((0,7),(2,4)), ((4,7),(2,4)), ((2,4),(2,0))],
    'Z': [((0,7),(4,7)), ((4,7),(0,0)), ((0,0),(4,0))],
    '0': [((1,7),(3,7)), ((3,7),(4,5)), ((4,5),(4,2)), ((4,2),(3,0)), ((3,0),(1,0)), ((1,0),(0,2)), ((0,2),(0,5)), ((0,5),(1,7)), ((0,2),(4,5))],
    '1': [((1,5),(2,7)), ((2,7),(2,0)), ((0,0),(4,0))],
    '2': [((0,6),(1,7)), ((1,7),(3,7)), ((3,7),(4,6)), ((4,6),(4,4.5)), ((4,4.5),(0,0)), ((0,0),(4,0))],
    '3': [((0,6),(1,7)), ((1,7),(3,7)), ((3,7),(4,5.5)), ((4,5.5),(2.5,4)), ((4,2.5),(2.5,4)), ((4,2.5),(4,1)), ((4,1),(3,0)), ((3,0),(1,0)), ((1,0),(0,1))],
    '4': [((3,0),(3,7)), ((0,7),(0,3)), ((0,3),(4,3))],
    '5': [((4,7),(0,7)), ((0,7),(0,4)), ((0,4),(3,4)), ((3,4),(4,2.5)), ((4,2.5),(4,1)), ((4,1),(3,0)), ((3,0),(0,0))],
    '6': [((3,7),(1,7)), ((1,7),(0,5)), ((0,5),(0,1)), ((0,1),(1,0)), ((1,0),(3,0)), ((3,0),(4,1)), ((4,1),(4,3.5)), ((4,3.5),(3,4.5)), ((3,4.5),(0,4.5))],
    '7': [((0,7),(4,7)), ((4,7),(1.5,0))],
    '8': [((1,7),(3,7)), ((3,7),(4,5.5)), ((4,5.5),(3,4)), ((3,4),(1,4)), ((1,4),(0,5.5)), ((0,5.5),(1,7)),
          ((3,4),(4,2.5)), ((4,2.5),(3,0)), ((3,0),(1,0)), ((1,0),(0,2.5)), ((0,2.5),(1,4))],
    '9': [((4,3.5),(1,3.5)), ((1,3.5),(0,5)), ((0,5),(1,7)), ((1,7),(3,7)), ((3,7),(4,5)), ((4,5),(4,1)), ((4,1),(3,0)), ((3,0),(1,0))],
    '-': [((0,3.5),(4,3.5))],
    '+': [((2,1.5),(2,5.5)), ((0,3.5),(4,3.5))],
    '/': [((0,0),(4,7))],
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
    ' ': []
}

def render_text_to_segments(text, start_x, start_y, char_height=1.2, char_width=0.8, spacing=0.3):
    """
    Renders text to line segments [(x1, y1, x2, y2), ...]
    start_x, start_y is bottom-left origin of first character.
    """
    segments = []
    curr_x = start_x
    scale_y = char_height / 7.0
    scale_x = char_width / 4.0

    for ch in text.upper():
        strokes = FONT_STROKES.get(ch, [])
        for (p1, p2) in strokes:
            x1 = curr_x + p1[0] * scale_x
            y1 = start_y + p1[1] * scale_y
            x2 = curr_x + p2[0] * scale_x
            y2 = start_y + p2[1] * scale_y
            segments.append((x1, y1, x2, y2))
        curr_x += char_width + spacing
    return segments

if __name__ == '__main__':
    segs = render_text_to_segments("BEETLE ESP32-C6", 115.0, 110.0, char_height=1.2, char_width=0.8)
    print(f"Rendered {len(segs)} segments for text.")
