sungmin9910/ColdChain-DigitalTwin-Platform/Hardware_Prototypes/code26/test/examples/mpu6050/mpu6050_example.ino

/*
 GY-521 (MPU6050) 예시 (ESP32, I2C)
 연결: SDA -> 21, SCL -> 22
 라이브러리: Adafruit MPU6050
*/

#include <Wire.h>
#include <Adafruit_MPU6050.h>
#include <Adafruit_Sensor.h>

Adafruit_MPU6050 mpu;

void setup() {
  Serial.begin(115200);
  Wire.begin();
  if (!mpu.begin()) {
    Serial.println("Failed to find MPU6050");
    while (1) delay(10);
  }
  Serial.println("MPU6050 found");
  mpu.setAccelerometerRange(MPU6050_RANGE_8_G);
  mpu.setGyroRange(MPU6050_RANGE_500_DEG);
  mpu.setFilterBandwidth(MPU6050_BAND_21_HZ);
}

void loop() {
  sensors_event_t a, g, temp;
  mpu.getEvent(&a, &g, &temp);

  Serial.print("Accel X: "); Serial.print(a.acceleration.x); Serial.print(", Y: "); Serial.print(a.acceleration.y); Serial.print(", Z: "); Serial.println(a.acceleration.z);
  Serial.print("Gyro  X: "); Serial.print(g.gyro.x); Serial.print(", Y: "); Serial.print(g.gyro.y); Serial.print(", Z: "); Serial.println(g.gyro.z);
  delay(500);
}
