sungmin9910/ColdChain-DigitalTwin-Platform/scratch/generate_routing_diagram.py

import os
import re
import matplotlib.pyplot as plt
import matplotlib.patches as patches
import numpy as np

PCB_PATH = r"c:\Users\korea\Desktop\1hsm\hanhanhan\ColdChain-DigitalTwin-Platform\3D modeling\CarrierBoard_BeetleC6_EdgeUSB_50x50_NoText\CarrierBoard_BeetleC6_EdgeUSB_50x50.kicad_pcb"
OUT_IMG = r"c:\Users\korea\Desktop\1hsm\hanhanhan\ColdChain-DigitalTwin-Platform\3D modeling\CarrierBoard_BeetleC6_EdgeUSB_50x50_NoText\Fig_CarrierBoard_Routing_Verification.png"
ARTIFACT_DIR = r"C:\Users\korea\.gemini\antigravity-ide\brain\531a7f17-5cfb-4c4c-a6c8-8be28bb2ba15"
ARTIFACT_IMG = os.path.join(ARTIFACT_DIR, "Fig_CarrierBoard_Routing_Verification.png")

with open(PCB_PATH, "r", encoding="utf-8") as f:
    pcb_text = f.read()

# 1. Parse Nets
net_names = {
    0: "NC",
    1: "GND",
    2: "3V3",
    3: "BAT+",
    4: "BAT",
    5: "I2C_SDA",
    6: "I2C_SCL",
    7: "GPS_RX",
    8: "GPS_TX"
}

net_colors = {
    1: "#27AE60", # GND (Green)
    2: "#E74C3C", # 3V3 (Red)
    3: "#E67E22", # BAT+ (Orange)
    4: "#F39C12", # BAT (Amber)
    5: "#00BCD4", # SDA (Cyan)
    6: "#9B59B6", # SCL (Purple)
    7: "#F1C40F", # GPS_RX (Yellow)
    8: "#1ABC9C", # GPS_TX (Teal)
}

# 2. Parse Segments
# (segment (start 122.0 146.5) (end 122.0 148.2) (width 0.35) (layer "F.Cu") (net 3))
seg_pattern = re.compile(r'\(segment\s+\(start\s+([0-9.-]+)\s+([0-9.-]+)\)\s+\(end\s+([0-9.-]+)\s+([0-9.-]+)\)\s+\(width\s+([0-9.-]+)\)\s+\(layer\s+"([^"]+)"\)\s+\(net\s+([0-9]+)\)\)')
segments = []
for m in seg_pattern.finditer(pcb_text):
    x1, y1, x2, y2, w, layer, net = float(m.group(1)), float(m.group(2)), float(m.group(3)), float(m.group(4)), float(m.group(5)), m.group(6), int(m.group(7))
    segments.append({
        'x1': x1, 'y1': y1, 'x2': x2, 'y2': y2, 'w': w, 'layer': layer, 'net': net
    })

# 3. Parse Vias
# (via (at 126.00 143.50) (size 0.8) (drill 0.4) (layers "F.Cu" "B.Cu") (net 2))
via_pattern = re.compile(r'\(via\s+\(at\s+([0-9.-]+)\s+([0-9.-]+)\)\s+\(size\s+([0-9.-]+)\)\s+\(drill\s+([0-9.-]+)\).*?\(net\s+([0-9]+)\)\)')
vias = []
for m in via_pattern.finditer(pcb_text):
    x, y, s, d, net = float(m.group(1)), float(m.group(2)), float(m.group(3)), float(m.group(4)), int(m.group(5))
    vias.append({
        'x': x, 'y': y, 'size': s, 'drill': d, 'net': net
    })

# 4. Parse Footprints and Pads
# Extract footprints
fp_blocks = re.findall(r'\(footprint\s+"([^"]+)"\s+\(layer\s+"([^"]+)"\)\s+\(at\s+([0-9.-]+)\s+([0-9.-]+)(?:\s+([0-9.-]+))?\)(.*?)\n\t\)', pcb_text, re.DOTALL)
pads = []
for fp_name, fp_layer, fp_x, fp_y, fp_rot, fp_body in fp_blocks:
    fx, fy = float(fp_x), float(fp_y)
    rot = float(fp_rot) if fp_rot else 0.0
    
    # get reference
    ref_match = re.search(r'\(property\s+"Reference"\s+"([^"]+)"', fp_body)
    ref = ref_match.group(1) if ref_match else fp_name
    
    # parse pads in footprint
    pad_matches = re.finditer(r'\(pad\s+"([^"]+)"\s+(\w+)\s+(\w+)\s+\(at\s+([0-9.-]+)\s+([0-9.-]+)(?:\s+([0-9.-]+))?\)\s+\(size\s+([0-9.-]+)\s+([0-9.-]+)\)(?:.*?\(drill\s+([0-9.-]+)\))?(?:.*?\(net\s+([0-9]+)\s+"([^"]*)")?', fp_body)
    for pm in pad_matches:
        pnum = pm.group(1)
        ptype = pm.group(2) # thru_hole or smd
        pshape = pm.group(3) # circle, rect, roundrect
        px, py = float(pm.group(4)), float(pm.group(5))
        prot = float(pm.group(6)) if pm.group(6) else 0.0
        sx, sy = float(pm.group(7)), float(pm.group(8))
        drill = float(pm.group(9)) if pm.group(9) else 0.0
        net = int(pm.group(10)) if pm.group(10) else 0
        net_name = pm.group(11) if pm.group(11) else ""
        
        # calculate world position
        # apply footprint rotation
        rad = np.radians(rot)
        wx = fx + px * np.cos(rad) - py * np.sin(rad)
        wy = fy + px * np.sin(rad) + py * np.cos(rad)
        
        pads.append({
            'ref': ref,
            'num': pnum,
            'type': ptype,
            'shape': pshape,
            'x': wx,
            'y': wy,
            'sx': sx,
            'sy': sy,
            'drill': drill,
            'net': net,
            'net_name': net_name,
            'fp_layer': fp_layer
        })

print(f"Loaded: {len(segments)} segments, {len(vias)} vias, {len(pads)} pads")

# 5. Plotting Figure
plt.style.use('dark_background')
fig, axes = plt.subplots(1, 3, figsize=(24, 8.5), dpi=300)

# PCB Outline (50x50mm, X:100..150, Y:100..150 with 2mm chamfers)
chamfer_pts = [
    (102.0, 100.0), (148.0, 100.0),
    (150.0, 102.0), (150.0, 148.0),
    (148.0, 150.0), (102.0, 150.0),
    (100.0, 148.0), (100.0, 102.0),
    (102.0, 100.0)
]
poly_x, poly_y = zip(*chamfer_pts)

def draw_base_pcb(ax, title):
    # PCB Body
    pcb_patch = patches.Polygon(chamfer_pts, closed=True, facecolor='#11161B', edgecolor='#455A64', linewidth=2, zorder=1)
    ax.add_patch(pcb_patch)
    
    # Grid
    ax.set_xlim(98, 152)
    ax.set_ylim(98, 152)
    ax.set_aspect('equal')
    ax.invert_yaxis() # KiCad Y increases downwards
    ax.grid(True, linestyle=':', color='#263238', alpha=0.6, zorder=0)
    ax.set_xlabel('X Coordinate (mm)', fontsize=11, color='#ECEFF1', labelpad=6)
    ax.set_ylabel('Y Coordinate (mm)', fontsize=11, color='#ECEFF1', labelpad=6)
    ax.set_title(title, fontsize=14, fontweight='bold', color='#00E5FF', pad=12)
    
    # 4 Mounting Holes (M3, Dia 3.2, Pad 5.5)
    for hx, hy in [(103.5, 103.5), (146.5, 103.5), (103.5, 146.5), (146.5, 146.5)]:
        ax.add_patch(patches.Circle((hx, hy), 5.5/2, facecolor='#2C3E50', edgecolor='#27AE60', linewidth=1.5, zorder=2))
        ax.add_patch(patches.Circle((hx, hy), 3.2/2, facecolor='#000000', edgecolor='#7F8C8D', linewidth=1, zorder=3))
        ax.text(hx, hy, 'M3\nGND', color='#2ECC71', fontsize=7, ha='center', va='center', fontweight='bold', zorder=4)

# Component Outlines to show context
comp_boxes = [
    {"name": "DFRobot Beetle ESP32-C6 (Top)", "x": 114.75, "y": 100.0, "w": 20.5, "h": 25.0, "color": "#78909C"},
    {"name": "BH1750 (Top)", "x": 135.8, "y": 106.7, "w": 13.7, "h": 18.5, "color": "#78909C"},
    {"name": "GPS ATGM336H (Bottom)", "x": 100.86, "y": 107.5, "w": 13.1, "h": 15.7, "color": "#546E7A"},
    {"name": "SHT45 Qwiic (Bottom)", "x": 100.8, "y": 125.5, "w": 25.2, "h": 17.8, "color": "#546E7A"},
    {"name": "GY-521 IMU (Bottom)", "x": 128.0, "y": 125.5, "w": 20.5, "h": 15.5, "color": "#546E7A"},
    {"name": "JST-PH 2.0 (Top)", "x": 120.0, "y": 144.5, "w": 6.0, "h": 4.5, "color": "#78909C"},
    {"name": "SW1 Switch (Top)", "x": 112.5, "y": 144.5, "w": 7.0, "h": 4.0, "color": "#78909C"},
    {"name": "R3 (Top)", "x": 120.8, "y": 141.0, "w": 2.4, "h": 2.0, "color": "#78909C"},
    {"name": "R4 (Top)", "x": 126.8, "y": 141.0, "w": 2.4, "h": 2.0, "color": "#78909C"},
]

def draw_components(ax):
    for b in comp_boxes:
        rect = patches.Rectangle((b['x'], b['y']), b['w'], b['h'], fill=False, edgecolor=b['color'], linestyle='--', linewidth=0.9, alpha=0.5, zorder=2)
        ax.add_patch(rect)

def draw_pads(ax, layer_filter=None):
    for p in pads:
        if p['ref'].startswith('MountingHole'):
            continue
        # check layer filter
        if layer_filter == 'F.Cu' and p['type'] == 'smd' and p['fp_layer'] != 'F.Cu':
            continue
        if layer_filter == 'B.Cu' and p['type'] == 'smd' and p['fp_layer'] != 'B.Cu':
            continue
            
        color = net_colors.get(p['net'], '#7F8C8D')
        if p['shape'] in ['circle', 'thru_hole']:
            ax.add_patch(patches.Circle((p['x'], p['y']), p['sx']/2, facecolor='#212F3D', edgecolor=color, linewidth=1.5, zorder=6))
            if p['drill'] > 0:
                ax.add_patch(patches.Circle((p['x'], p['y']), p['drill']/2, facecolor='#000000', zorder=7))
        elif p['shape'] == 'rect':
            ax.add_patch(patches.Rectangle((p['x']-p['sx']/2, p['y']-p['sy']/2), p['sx'], p['sy'], facecolor='#212F3D', edgecolor=color, linewidth=1.5, zorder=6))
            if p['drill'] > 0:
                ax.add_patch(patches.Circle((p['x'], p['y']), p['drill']/2, facecolor='#000000', zorder=7))
        else: # smd roundrect
            ax.add_patch(patches.Rectangle((p['x']-p['sx']/2, p['y']-p['sy']/2), p['sx'], p['sy'], facecolor='#212F3D', edgecolor=color, linewidth=1.2, zorder=6))
            
        # Text label on pad
        if p['net'] > 0:
            short_net = net_names[p['net']].replace('I2C_', '').replace('GPS_', '')
            ax.text(p['x'], p['y']-0.1, short_net, color='#FFFFFF', fontsize=5.5, ha='center', va='center', fontweight='bold', zorder=8)

# -------------------------------------------------------------
# Panel 1: Composite 2-Layer X-Ray (Both Layers)
# -------------------------------------------------------------
ax1 = axes[0]
draw_base_pcb(ax1, "Panel 1: Complete 2-Layer Routing (X-Ray Composite)")
draw_components(ax1)
draw_pads(ax1)

# Draw B.Cu segments first (Bottom = Cyan / Blue tint)
for s in segments:
    if s['layer'] == 'B.Cu':
        c = net_colors.get(s['net'], '#3498DB')
        ax1.plot([s['x1'], s['x2']], [s['y1'], s['y2']], color=c, linewidth=2.8, alpha=0.85, zorder=4, solid_capstyle='round')

# Draw F.Cu segments (Top = Warm / Red tint)
for s in segments:
    if s['layer'] == 'F.Cu':
        c = net_colors.get(s['net'], '#E74C3C')
        ax1.plot([s['x1'], s['x2']], [s['y1'], s['y2']], color=c, linewidth=2.4, alpha=0.95, zorder=5, solid_capstyle='round')

# Draw Vias
for v in vias:
    c = net_colors.get(v['net'], '#F39C12')
    ax1.add_patch(patches.Circle((v['x'], v['y']), v['size']/2, facecolor='#F39C12', edgecolor='#FFFFFF', linewidth=1.0, zorder=9))
    ax1.add_patch(patches.Circle((v['x'], v['y']), v['drill']/2, facecolor='#000000', zorder=10))

# -------------------------------------------------------------
# Panel 2: Front Layer (F.Cu) - Power & Top Connections
# -------------------------------------------------------------
ax2 = axes[1]
draw_base_pcb(ax2, "Panel 2: Top Layer (F.Cu) - 3.3V, BAT, GND & Pull-ups")
draw_components(ax2)
draw_pads(ax2, 'F.Cu')

for s in segments:
    if s['layer'] == 'F.Cu':
        c = net_colors.get(s['net'], '#E74C3C')
        ax2.plot([s['x1'], s['x2']], [s['y1'], s['y2']], color=c, linewidth=3.0, alpha=0.95, zorder=5, solid_capstyle='round')

for v in vias:
    c = net_colors.get(v['net'], '#F39C12')
    ax2.add_patch(patches.Circle((v['x'], v['y']), v['size']/2, facecolor='#F39C12', edgecolor='#FFFFFF', linewidth=1.0, zorder=9))
    ax2.add_patch(patches.Circle((v['x'], v['y']), v['drill']/2, facecolor='#000000', zorder=10))

# Annotations for F.Cu
ax2.annotate("3.3V Power Trunk (F.Cu)", xy=(137.67, 114.0), xytext=(140.0, 102.5),
             arrowprops=dict(arrowstyle="->", color="#E74C3C", lw=1.5), fontsize=8.5, color="#FF6B6B", fontweight='bold', zorder=12)
ax2.annotate("BAT Spine (X=125.0)", xy=(125.0, 120.0), xytext=(118.0, 134.0),
             arrowprops=dict(arrowstyle="->", color="#F39C12", lw=1.5), fontsize=8.5, color="#F39C12", fontweight='bold', zorder=12)
ax2.annotate("R3/R4 Pull-Up Pads", xy=(124.5, 142.0), xytext=(114.0, 138.5),
             arrowprops=dict(arrowstyle="->", color="#FFFFFF", lw=1.2), fontsize=8.5, color="#FFFFFF", fontweight='bold', zorder=12)

# -------------------------------------------------------------
# Panel 3: Back Layer (B.Cu) - Signal Highways & UART
# -------------------------------------------------------------
ax3 = axes[2]
draw_base_pcb(ax3, "Panel 3: Bottom Layer (B.Cu) - I2C & GPS Channels")
draw_components(ax3)
draw_pads(ax3, 'B.Cu')

for s in segments:
    if s['layer'] == 'B.Cu':
        c = net_colors.get(s['net'], '#3498DB')
        ax3.plot([s['x1'], s['x2']], [s['y1'], s['y2']], color=c, linewidth=3.0, alpha=0.95, zorder=5, solid_capstyle='round')

for v in vias:
    c = net_colors.get(v['net'], '#F39C12')
    ax3.add_patch(patches.Circle((v['x'], v['y']), v['size']/2, facecolor='#F39C12', edgecolor='#FFFFFF', linewidth=1.0, zorder=9))
    ax3.add_patch(patches.Circle((v['x'], v['y']), v['drill']/2, facecolor='#000000', zorder=10))

# Annotations for B.Cu
ax3.annotate("SCL Highway (Y=130.0)", xy=(125.0, 130.0), xytext=(127.0, 134.5),
             arrowprops=dict(arrowstyle="->", color="#9B59B6", lw=1.5), fontsize=8.5, color="#D7BDE2", fontweight='bold', zorder=12)
ax3.annotate("SDA Highway (Y=125.0)", xy=(128.0, 125.0), xytext=(129.0, 120.0),
             arrowprops=dict(arrowstyle="->", color="#00BCD4", lw=1.5), fontsize=8.5, color="#80DEEA", fontweight='bold', zorder=12)
ax3.annotate("GPS UART (No Vias, Direct)", xy=(110.0, 111.0), xytext=(101.5, 102.5),
             arrowprops=dict(arrowstyle="->", color="#1ABC9C", lw=1.5), fontsize=8.5, color="#A3E4D7", fontweight='bold', zorder=12)
ax3.annotate("Zero Collisions with MCU Pin 8", xy=(114.5, 120.44), xytext=(102.0, 121.5),
             arrowprops=dict(arrowstyle="->", color="#00E5FF", lw=1.5), fontsize=8.5, color="#00E5FF", fontweight='bold', zorder=12)

# Global Legend
legend_elements = [
    patches.Patch(color=net_colors[2], label='Net 2: 3V3 Power (Top F.Cu)'),
    patches.Patch(color=net_colors[1], label='Net 1: GND Plane/Bus'),
    patches.Patch(color=net_colors[5], label='Net 5: I2C_SDA (Bottom B.Cu)'),
    patches.Patch(color=net_colors[6], label='Net 6: I2C_SCL (Bottom B.Cu)'),
    patches.Patch(color=net_colors[7], label='Net 7: GPS_RX (Bottom B.Cu)'),
    patches.Patch(color=net_colors[8], label='Net 8: GPS_TX (Bottom B.Cu)'),
    patches.Patch(color=net_colors[4], label='Net 4: BAT (Top F.Cu)'),
    patches.Patch(color='#F39C12', label='Via (Dia 0.8mm / Drill 0.4mm)')
]
fig.legend(handles=legend_elements, loc='lower center', ncol=4, fontsize=10, frameon=True, facecolor='#1C2833', edgecolor='#566573')

plt.tight_layout(rect=[0, 0.07, 1, 0.96])
plt.suptitle("CarrierBoard Beetle ESP32-C6 EdgeUSB (50x50mm) - Production Routing Verification (DRC 0 Errors)", fontsize=16, fontweight='bold', color='#FFFFFF')

plt.savefig(OUT_IMG, dpi=300, facecolor='#0B0E11')
plt.savefig(ARTIFACT_IMG, dpi=300, facecolor='#0B0E11')
print(f"Generated {OUT_IMG} and copied to {ARTIFACT_IMG}")
