sungmin9910/ColdChain-DigitalTwin-Platform/scratch/test_routing_perfection.py

import numpy as np

pads = [
    # M3 holes
    ('H1', 1, 103.5, 103.5, 2.75),
    ('H2', 1, 146.5, 103.5, 2.75),
    ('H3', 1, 103.5, 146.5, 2.75),
    ('H4', 1, 146.5, 146.5, 2.75),
    # JST-PH
    ('J1_1', 3, 122.0, 146.5, 0.8),
    ('J1_2', 1, 124.0, 146.5, 0.8),
    # SW1
    ('SW1_1', 3, 114.5, 146.5, 0.6),
    ('SW1_2', 4, 116.0, 146.5, 0.6),
    ('SW1_3', 0, 117.5, 146.5, 0.6),
    # R3
    ('R3_1', 5, 121.25, 142.0, 0.55),
    ('R3_2', 2, 122.75, 142.0, 0.55),
    # R4
    ('R4_1', 6, 127.25, 142.0, 0.55),
    ('R4_2', 2, 128.75, 142.0, 0.55),
]

# MCU Left
mcu_l_nets = [4, 1, 0, 7, 8, 5, 6, 0]
for i, n in enumerate(mcu_l_nets):
    pads.append((f'MCU_L_{i+1}', n, 116.11, 102.66 + i*2.54, 0.8))

# MCU Right
mcu_r_nets = [1, 2, 0, 0, 0, 0, 0, 0]
for i, n in enumerate(mcu_r_nets):
    pads.append((f'MCU_R_{i+1}', n, 133.89, 102.66 + i*2.54, 0.8))

# BH1750 (Right Wing, Y=123.2)
bh_nets = [2, 1, 6, 5, 1]
for i, n in enumerate(bh_nets):
    pads.append((f'BH_{i+1}', n, 137.67 + i*2.54, 123.2, 0.8))

# GPS (Left Wing, Y=109.5)
gps_nets = [2, 1, 7, 8, 0]
for i, n in enumerate(gps_nets):
    pads.append((f'GPS_{i+1}', n, 102.33 + i*2.54, 109.5, 0.8))

# SHT45 (Top-Left, Y=127.5)
sht_nets = [2, 0, 1, 6, 5]
for i, n in enumerate(sht_nets):
    pads.append((f'SHT_{i+1}', n, 108.17 + i*2.54, 127.5, 0.8))

# GY-521 (Top-Right, Y=127.5)
gy_nets = [2, 1, 6, 5, 0, 0, 1, 0]
for i, n in enumerate(gy_nets):
    pads.append((f'GY_{i+1}', n, 129.56 + i*2.54, 127.5, 0.8))

def dist_point_to_segment(px, py, x1, y1, x2, y2):
    dx = x2 - x1
    dy = y2 - y1
    if dx == 0 and dy == 0:
        return np.hypot(px - x1, py - y1)
    t = max(0, min(1, ((px - x1)*dx + (py - y1)*dy) / (dx*dx + dy*dy)))
    proj_x = x1 + t * dx
    proj_y = y1 + t * dy
    return np.hypot(px - proj_x, py - proj_y)

# -------------------------------------------------------------
# Clean Routing Definitions
# -------------------------------------------------------------

# TOP LAYER TRACES
top_traces = [
    # 1. Net 3: BAT+
    ("BAT+_1", 3, 122.0, 146.5, 122.0, 148.2),
    ("BAT+_2", 3, 122.0, 148.2, 114.5, 148.2),
    ("BAT+_3", 3, 114.5, 148.2, 114.5, 146.5),
    
    # 2. Net 4: BAT (route via X=120.0 to clear SHT_5 at 118.33)
    ("BAT_1", 4, 116.0, 146.5, 116.0, 135.0),
    ("BAT_2", 4, 116.0, 135.0, 120.0, 131.0),
    ("BAT_3", 4, 120.0, 131.0, 120.0, 102.66), # X=120.0 is completely clear!
    ("BAT_4", 4, 120.0, 102.66, 116.11, 102.66), # into MCU Pin 1!
    
    # 3. Net 2: 3V3 on Top Layer
    # MCU Right Pin 2 (133.89, 105.20) to BH1750 Pin 1 (137.67, 123.2):
    ("3V3_T1", 2, 133.89, 105.20, 137.67, 105.20),
    ("3V3_T2", 2, 137.67, 105.20, 137.67, 123.2),
    # Feed Pull-ups via X=131.5:
    ("3V3_T3", 2, 133.89, 105.20, 131.5, 105.20),
    ("3V3_T4", 2, 131.5, 105.20, 131.5, 124.5),
    ("3V3_T5", 2, 131.5, 124.5, 128.75, 124.5),
    ("3V3_T6", 2, 128.75, 124.5, 128.75, 142.0), # into R4 Pin 2!
    ("3V3_T7", 2, 128.75, 138.0, 122.75, 138.0),
    ("3V3_T8", 2, 122.75, 138.0, 122.75, 142.0), # into R3 Pin 2!
    
    # 4. Net 5: I2C_SDA on Top Layer
    # MCU Left Pin 6 (116.11, 115.36) to R3 Pin 1 (121.25, 142.0):
    ("SDA_T1", 5, 116.11, 115.36, 121.25, 120.50),
    ("SDA_T2", 5, 121.25, 120.50, 121.25, 142.0),
    # To BH1750 Pin 4 (145.29, 123.2):
    # Route via Y=121.75 (above MCU_R_8 at 120.44):
    ("SDA_T3", 5, 121.25, 121.75, 145.29, 121.75),
    ("SDA_T4", 5, 145.29, 121.75, 145.29, 123.2), # into BH1750 Pin 4!
    
    # 5. Net 6: I2C_SCL on Top Layer (only feeds R4 from MCU Pin 7)
    ("SCL_T1", 6, 116.11, 117.90, 127.25, 129.04),
    ("SCL_T2", 6, 127.25, 129.04, 127.25, 142.0), # into R4 Pin 1!
]

# BOTTOM LAYER TRACES
bottom_traces = [
    # 1. Net 2: 3V3 on Bottom Layer
    ("3V3_B1", 2, 133.89, 105.20, 129.56, 105.20),
    ("3V3_B2", 2, 129.56, 105.20, 129.56, 127.5), # into GY-521 Pin 1!
    ("3V3_B3", 2, 129.56, 125.0, 108.17, 125.0),
    ("3V3_B4", 2, 108.17, 125.0, 108.17, 127.5), # into SHT45 Pin 1!
    ("3V3_B5", 2, 108.17, 125.0, 102.33, 125.0),
    ("3V3_B6", 2, 102.33, 125.0, 102.33, 109.5), # into GPS Pin 1!
    
    # 2. Net 5: I2C_SDA on Bottom Layer
    # MCU Left Pin 6 (116.11, 115.36) to SHT45 Pin 5 (118.33, 127.5)
    ("SDA_B1", 5, 116.11, 115.36, 118.33, 117.58),
    ("SDA_B2", 5, 118.33, 117.58, 118.33, 127.5), # into SHT45 Pin 5!
    # To GY-521 Pin 4 (137.18, 127.5) via upper channel Y=131.0:
    ("SDA_B3", 5, 118.33, 127.5, 118.33, 131.0),
    ("SDA_B4", 5, 118.33, 131.0, 137.18, 131.0),
    ("SDA_B5", 5, 137.18, 131.0, 137.18, 127.5), # into GY-521 Pin 4 from top!
    
    # 3. Net 6: I2C_SCL on Bottom Layer
    # MCU Left Pin 7 (116.11, 117.90) to SHT45 Pin 4 (115.79, 127.5)
    # Route via X=119.5 (away from MCU_L_8 at 116.11):
    ("SCL_B1", 6, 116.11, 117.90, 119.5, 117.90),
    ("SCL_B2", 6, 119.5, 117.90, 119.5, 125.0),
    ("SCL_B3", 6, 119.5, 125.0, 115.79, 125.0),
    ("SCL_B4", 6, 115.79, 125.0, 115.79, 127.5), # into SHT45 Pin 4!
    # Branch to GY-521 Pin 3 (134.64, 127.5) via upper channel Y=132.5:
    ("SCL_B5", 6, 115.79, 127.5, 115.79, 132.5),
    ("SCL_B6", 6, 115.79, 132.5, 134.64, 132.5),
    ("SCL_B7", 6, 134.64, 132.5, 134.64, 127.5), # into GY-521 Pin 3 from top!
    # Branch to BH1750 Pin 3 (142.75, 123.2) on Bottom Layer:
    ("SCL_B8", 6, 134.64, 127.5, 134.64, 121.8),
    ("SCL_B9", 6, 134.64, 121.8, 142.75, 121.8),
    ("SCL_B10", 6, 142.75, 121.8, 142.75, 123.2), # into BH1750 Pin 3!
    
    # 4. Net 7: GPS_RX (MCU GPIO17 at 116.11, 110.28 to GPS Pin 3 at 107.41, 109.5)
    ("GPS_RX_1", 7, 116.11, 110.28, 114.5, 110.28),
    ("GPS_RX_2", 7, 114.5, 110.28, 111.5, 113.28),
    ("GPS_RX_3", 7, 111.5, 113.28, 107.41, 113.28),
    ("GPS_RX_4", 7, 107.41, 113.28, 107.41, 109.5),
    
    # 5. Net 8: GPS_TX (MCU GPIO16 at 116.11, 112.82 to GPS Pin 4 at 109.95, 109.5)
    ("GPS_TX_1", 8, 116.11, 112.82, 109.95, 112.82),
    ("GPS_TX_2", 8, 109.95, 112.82, 109.95, 109.5),
]

# GROUND TRACES (NET 1)
gnd_traces = [
    # Top GND:
    ("GND_T1", 1, 133.89, 102.66, 146.5, 102.66),
    ("GND_T2", 1, 146.5, 102.66, 146.5, 103.5),
    ("GND_T3", 1, 146.5, 103.5, 148.5, 105.5),
    ("GND_T4", 1, 148.5, 105.5, 148.5, 123.2),
    ("GND_T5", 1, 148.5, 123.2, 147.83, 123.2), # into BH1750 Pin 5!
    ("GND_T6", 1, 148.5, 116.0, 140.21, 116.0),
    ("GND_T7", 1, 140.21, 116.0, 140.21, 123.2), # into BH1750 Pin 2!
    
    # Bottom GND:
    ("GND_B1", 1, 116.11, 105.20, 104.87, 105.20),
    ("GND_B2", 1, 104.87, 105.20, 104.87, 109.5), # into GPS Pin 2!
    ("GND_B3", 1, 104.87, 105.20, 103.5, 103.83),
    ("GND_B4", 1, 103.5, 103.83, 103.5, 103.5), # into H1!
    
    ("GND_B5", 1, 113.25, 127.5, 113.25, 139.0),
    ("GND_B6", 1, 113.25, 139.0, 103.5, 139.0),
    ("GND_B7", 1, 103.5, 139.0, 103.5, 146.5), # into H3!
    
    ("GND_B8", 1, 132.10, 127.5, 132.10, 139.0),
    ("GND_B9", 1, 132.10, 139.0, 144.80, 139.0),
    ("GND_B10", 1, 144.80, 139.0, 144.80, 127.5), # into GY-521 Pin 7!
    ("GND_B11", 1, 144.80, 139.0, 146.5, 139.0),
    ("GND_B12", 1, 146.5, 139.0, 146.5, 146.5), # into H4!
    
    ("GND_T8", 1, 124.0, 146.5, 124.0, 148.5),
    ("GND_T9", 1, 124.0, 148.5, 146.5, 148.5),
    ("GND_T10", 1, 146.5, 148.5, 146.5, 146.5), # into H4!
]

print("=== CHECKING ALL TRACE CLEARANCES ===")
errors = 0
all_traces = top_traces + bottom_traces + gnd_traces
for name, net, x1, y1, x2, y2 in all_traces:
    for p_name, p_net, px, py, p_rad in pads:
        if p_net == net:
            continue
        d = dist_point_to_segment(px, py, x1, y1, x2, y2)
        clearance = d - p_rad - 0.35/2.0
        if clearance < 0.20:
            print(f"ERROR: {name} (Net {net}) too close to {p_name} (Net {p_net})! Clearance = {clearance:.3f} mm")
            errors += 1

print(f"\nTotal Trace-to-Pad Clearance Errors: {errors}")
if errors == 0:
    print("SUCCESS: 100% CLEAN ELECTRICAL ROUTING! ZERO SHORTS, ZERO VIOLATIONS!")
